showmin/ear_3d_model_survey/jp/05-acoustic-constraints.md

# Part 5 — 音響幾何制約

ステータス：受入済 ｜ 最終更新 2026-08-21

> 🌐 中文版：[cn/05-acoustic-constraints.md](../cn/05-acoustic-constraints.md)

---

## 5.0 手法の説明

ドライバがまだ選定されていないため、容積系の数値は現段階では絶対値を示せない。本節が示すのは**計算方法と比例関係**である。【仮定・要検証】と表示した箇所は、ドライバ仕様と各機種（S／M／L）のシェルエンベロープが確定した時点でそのまま代入でき、方法を設計し直す必要はない。

IEC 標準の正式条文への取得経路がないため、以下では公開情報で確認できる表題と適用範囲のみを用い、**条文の詳細を捏造しない**。

## 5.1 前気室容積 V_front、後気室容積 V_back

### 5.1.1 ⚠️ まず密閉するか否かを確定する——それが V_front の境界を決める

**同じ「前気室」でも、密閉型と非密閉型では定義がまったく異なる。取り違えれば集中定数モデル全体の境界が誤る。**

| 形態 | V_front の定義 | 証拠等級 | 備考 |
|---|---|---|---|
| **密閉型カナル**（イヤーチップが外耳道内で密閉を形成） | V_front ＝ ドライバ振動板からイヤーチップ内孔までの機器内部空間 ＋ イヤーチップから鼓膜までの残留外耳道容積。**耳甲介（concha）は密閉面の外側で大気に開放されており、V_front に算入しない** | 【慣例】電気音響アナロジーの集中定数モデル境界定義 | V_front を規定するのは**外耳道の幾何と挿入深さ**であり、耳甲介ではない |
| **非密閉型イヤホン**（本体が耳甲介腔に座り、外耳道内で密閉しない） | 明確な閉じた前気室は存在しない。本体と耳甲介腔・外界が漏れ結合を形成し、耳甲介容積は**結合気室＋漏れ経路**として模型に入る | 【慣例】同上 | この場合にのみ耳甲介の幾何が関係するが、**役割は結合気室であり密閉 V_front ではない** |

> ⚠️ **耳甲介の寸法は V_front ではない。**
> [Part 2.3](02-anthropometric-basis.md) の耳甲介幅（CW）と耳甲介深さ（CD）が規定するのは**シェルの外形エンベロープ**——本体をどれだけ大きくできるか——であり、音響的な前気室容積ではない。
> また CW／CD は**線形寸法**であり、容積へ換算するには形状仮定を追加で重ねる必要がある（耳甲介は不規則な椀状）。そうして得た数値は「文献の線形値＋形状仮定＋集団年齢の外挿」の複合推定であり、**【文献】と表示してはならない**。
> **本文書はこの外挿を行わない。**
> ⚠️ **耳甲介の「容積」を当チームは取得していない。** [Part 2.4](02-anthropometric-basis.md) が実測したのは耳甲介の**深さ**（CD、単一の長さ）であり容積ではない。P1–P5 の命名ランドマークを要する測定は、2D 注釈と 3D 点群を位置合わせできず中止した（Part 2.4.5 参照）。**したがって V_front には現時点で実測に基づく桁の参照値がない。** ドライバ選定後に機器内部の幾何から直接計算するか、別途、気室容積の測定を取得する必要がある。

### 5.1.2 容積換算と設計目標

| 項目 | 数値／しきい値 | 証拠等級 | 出典 | 備考 |
|---|---|---|---|---|
| 容積→音響コンプライアンス換算 | Ca = V/(ρ₀c²) | 【慣例】 | 線形音響の電気音響アナロジー標準理論 | 前後気室それぞれに代入 |
| 後気室の設計目標 | V_back とドライバ V_as の比を、密閉箱システム理論に従って整合させる | 【仮定・要検証】 | 学術論文：Thiele (1961)、Small (1972) の密閉箱システム理論 | ドライバ選定前は絶対値 cc を示せない。方法は確定済み |
| 桁のサニティチェック（**規範値ではない**） | 小型カナル型イヤホンの後気室容積は概ね 1–10 cm³ の桁 | 【仮定、参考のみ】 | 米国特許文献（請求範囲を逐一照合していない） | 業界標準ではなく桁の傍証にすぎない。**設計根拠としてはならない** |
| 機種 S／M／L の扱い | 各機種のシェル利用可能内部容積に応じて V_front/V_back を**比例配分**し、3 つの固定絶対値は与えない | 【仮定・要検証】 | — | Part 6 が各機種のシェルエンベロープ容積を提供した時点で代入する。機種が変わっても規則を書き直す必要はない。**注意：機種 ≠ 耳型区分。Part 0.4b 参照** |

## 5.2 チューニングポート（採用する場合）

| 項目 | 数値／しきい値 | 証拠等級 | 出典 | 備考 |
|---|---|---|---|---|
| 音響質量の式 | Ma = ρ₀(L+ΔL)/A | 【慣例】 | 線形音響の標準教科書（Helmholtz 共振器のネック理論） | — |
| 開口端補正（unflanged、開口周囲に平面なし） | ΔL ≈ 0.6133 × 半径 | 【文献】 | 学術論文：Levine & Schwinger (1948), *On the Radiation of Sound from an Unflanged Circular Pipe*, Physical Review | 開口が外耳道側へ開く場合に適用 |
| 開口端補正（flanged、開口周囲に平面あり） | ΔL ≈ 0.82 × 半径 | 【文献】 | Rayleigh の古典的近似。後続の数値研究で約 0.8216 と確認 | **文献には 8/(3π)≈0.849 という表記もある**（無限バッフル上のピストン放射の端補正の古典形）。どちらの数値も一般的であり、引用時に採用した方を明記すること |
| チューニングポートを設けない場合 | 前後気室を単一の音響コンプライアンスとみなすか、漏れ経路で代替する | — | — | ポートの要否は音響アーキテクチャ全体の判断であり必須ではない |

> ⛔ **以下はアーキテクチャ別に分ける。密閉式と開放式ではダクトの役割がまったく異なり、取り違えれば「式は正しく、アーキテクチャの適用先が誤り」となる。**

### 5.2.1 開放式（vented／ported）——判定可能

| 項目 | 数値／しきい値 | 証拠等級 | 備考 |
|---|---|---|---|
| 調律関係 | f₀ = (c/2π)·√(A/(V·L_eff))、L_eff = L + ΔL（ΔL は上表の端補正係数） | 【慣例】 | 標準線形音響（ヘルムホルツ共振器）。c=343 m/s |
| **設計手順** | 目標 f₀ と接続する気室容積 V を先に定め → A/L_eff を逆算する。**A と L の自由度は 1 つだけであり、両方を自由に与えてはならない** | 【慣例】 | 判定可能：f₀ と V が与えられていれば、誰でも設計者の A・L を代入して検算できる |
| 表示要求 | 設計値は f₀ と V を併記すること | 条文 | A・L のみで f₀・V がなければ、本条は検査できない |
| CAD 側の孔径補償 | 目標 d、収縮 u → CAD 上は d/(1−u) で作図。収縮 2%→2.041mm、4%→2.083mm（目標 2.0mm） | 【慣例】 | 収縮量は [Part 6.A](06-structure-materials.md#sec-6-a) 参照。**開放式のみ必要**（f₀ が設計目標であるため） |
| f₀ のずれの向き | 未補償の場合 f₀ は**系統的に 2–4% 低くなる**（d −2%→A −4.0%→f₀ −2.0%、d −4%→A −7.8%→f₀ −4.0%） | 【計算｜入力：定数】 | **一方向のずれであり偶然誤差ではない。** 数を多く造形して平均しても消えず、CAD 側での補償が必須 |

### 5.2.2 密閉式（sealed）——**上式は適用不可。一部は欠落として登録**

| 項目 | 内容 | 証拠等級 | 備考 |
|---|---|---|---|
| ダクトの役割 | 音導管は前気室の経路に直列に入る**音響質量** Ma = ρ₀·L_eff/A であり、**調律ネックではない。密閉式に設計者が選べる f₀ は存在しない** | 【慣例】 | 高域のロールオフと位相に効くのであって、共振の調律点ではない |
| 制約(a)：容積収支 | ダクト内容積は V_front に算入される（[5.1.1](#sec-5-1-1) 参照）。前気室の容積配分と食い合う | 【慣例】 | V_front の予算が決まれば判定できる |
| 制約(b)：高域上限 | ダクトの音響質量と**挿入後の残存外耳道容積**のコンプライアンスが高域共振／ロールオフを作る。数学的形式は 5.2.1 と同じだが、ここでの V は**利用者の残存外耳道容積であり設計者が制御できる気室ではない** → 「目標として逆算する」ものではなく「結果として検査する」もの | 【推論】 | 下記の欠落を参照 |
| **⛔ 欠落として登録** | **制約(b) に数値しきい値を与えられない。** 欠けているのは挿入後の残存外耳道容積：本案件のデータに外耳道内部は含まれず（[Part 2](02-anthropometric-basis.md) 参照）、挿入深さも未定の設計変数である。両方とも欠けているため、この検査は閉じない | 【欠落】 | いずれかが埋まれば判定可能になる：残存外耳道容積の実測値、または挿入深さを凍結した外耳道モデル |
| 制約(c)：漏れ経路としての側面 | 密閉が完全でない場合、ダクト自体が [5.3](#sec-5-3) の漏れ経路の 1 つとなる。その形状は 5.3 に従い測定状態を明記すること | 【推論】 | — |

### 5.2.3 両アーキテクチャ共通の下界

| 項目 | 数値／しきい値 | 証拠等級 | 備考 |
|---|---|---|---|
| 造形孔径の下限 | FDM 水平孔 ≥2.0mm、造形 Z 軸に沿う垂直孔 ≥1.0mm | 【慣例】 | 正本は [Part 6.A](06-structure-materials.md#sec-6-a)。⚠️ **最小フィーチャ寸法（0.5mm）とは異なる**（後者は薄壁／細柱用）。断面積の下限で約 16 倍の差 |
| 造形方向 | **調律孔／音導孔の軸は造形 Z 軸に平行とすること。** 平行にできない場合は内部サポートが完全に除去できることを検証し、**除去できないものは音響経路の失効とみなす**（精度劣化ではない） | 条文 | 逆方向の制約は [Part 6.A](06-structure-materials.md#sec-6-a)：機体の造形配置方向は自由変数ではない |
| 質量モデルの適用可能性 | せん断波数 **円孔 s = r·√(ρ₀ω/μ)／狭スリット s = (h/2)·√(ρ₀ω/μ)（h はスリット高。半分を代入）**。**対象帯域の最低周波数で確認すること。** s ≳10 なら質量モデルが綺麗、s ≲1 なら 5.3 の粘性狭路モデルへ、中間はどちらも綺麗でない | 【慣例】 | ⚠️ **これはモデル適用性の基準であって伝達量の基準ではない**——下記の定義境界を参照。**⚠️ 狭スリットは必ず半高を代入する（円管で半径を用いるのと同じ）。全高では s が 2 倍ずれ、s はしきい値と比較する量なので判定が逆側へ反転する** |
| s の実算値 | 2.0mm 孔：100Hz→6.5／500Hz→14.5／1kHz→20.5。1.0mm 孔：100Hz→3.2／500Hz→7.2／1kHz→10.2 | 【計算｜入力：定数】 | **最小造形孔は低域では綺麗な質量支配ではない。** 対象帯域に低域を含む場合、最小孔の質量モデルの結果自体に誤差がある |
| **孔数：単孔を既定とする** | **同一の音響機能の開口は単孔を既定とする。** 独立した 3 つの理由：①分割すると各孔の s が下がる ②各孔径がより早く造形下限を割る ③**総面積が等しくても音響的に等価ではない**（端補正 ΔL ∝ r。n 個に分けると r→r/√n となり L_eff が小さくなって f₀ が上がる） | 【推論】 | ダクトが短いほどずれは大きく、睡眠用イヤホンのダクトはもともと短い |
| 多孔の端補正（独立孔の極限） | n 個の孔にそれぞれ ΔL(r₁/√n) を適用した場合、f₀ のずれは n=2→+5.8%、n=4→+10.5% | 【計算｜入力：定数】 | ⚠️ **孔が音響的に独立とみなせる場合にのみ成立する。本案件の幾何（中心距離/半径≈4）はこの極限にはなく、この値は実際のずれではない** |
| **⛔ 欠落として登録** | **中心距離/半径 ≈ 2–10 の区間における多孔の有効端補正が未確定。** 開口率補正の系はずれがより大きい方向を示し、合体の極限はより小さい方向を示す。両者は矛盾し、しかも前者は本件の開口率では信頼できる範囲の縁にある | 【欠落】 | 必要なもの：この区間を扱う検証可能な文献、または BEM／FEM の数値解。**単孔を既定とするのは、この未解決区間を丸ごと回避するためである** |

> ⚠️ **正しい比は「中心距離/孔半径」であって「中心距離/波長」ではない。** 孔どうしが影響し合うのは付加質量の近傍場の重なりであり、その尺度は孔半径である。中心距離/λ で判定すると「可聴域に独立とみなせる孔配列は存在しない」という結論になり、バスレフポートや有孔板の実務と矛盾する。

### 5.2.4 ⚠️ s 基準の定義境界——今回の誤りの根本修正

| 項目 | 内容 | 証拠等級 | 備考 |
|---|---|---|---|
| s 基準の性質 | **せん断波数 s は「モデル適用性」の基準であって「伝達量」の基準ではない。** s≳10 は粘性を無視でき質量モデルが綺麗であることを、s≲1 は粘性抵抗が支配的で狭路モデルへ移るべきことを意味する | 【慣例】 | 標準的な粘熱音響 |
| ⛔ 禁止される推論 | **s から「音が通るか」や「最小開口寸法」を逆算してはならない。** s<10 は伝達しないことを意味せず、**粘性損失を伴って伝達する**ことを意味する。損失量は完全な粘熱音響インピーダンスから別途計算する | 条文 | **実例**：s≳10 から「520 Hz には 1.36mm の開口が必要」と逆算し、密閉式は成立しないと推論したことがある。**当該推論は撤回済み** |
| **⛔ スリット高の不均一性：補正係数を探してはならない。それは係数ではない** | 平均スリット高を固定しても、区間ごとのインピーダンス合計の倍率は**分布の集中度に依存し、上界がない**：N 区間・指数 n で上界 = N^(n−1)（n=3・N=4 → 16×／N→∞ で非有界）。**倍率は建模者が周方向を何区間に切るかにも依存する** | **【計算｜入力：定数】** | **「文献が来れば書ける」性質のものとは異なる——原理的に係数ではない。** 平均 50µm の 4 区間例：35/35/35/95→1.97×／20/20/20/140→5.54×／0/0/50/150→7.00×／0/0/0/200→16.0× |
| **⛔ さらに実分布は二峰性であり、平均まわりの揺らぎではない** | 軟質イヤーチップを外耳道へ押し込むとき、接触力学が与えるのは**接触域（h＝0。微小な h ではなく隙間が無い）と分離域**である。外耳道断面は円ではないため、密着は**複数の接触パッチ ＋ その間の開放円弧**となる | 【推論】 | **物理的に意味のあるパラメータは開放円弧の弧長と高さであり、全周の平均高さではない。** 二峰の場合（例：0/0/50/150）の倍率は 7×–16× であって 2× ではない。**Part 6 D 節の F_i パッチ単位条文と同一の物理像の別表現である** |
| 伝達量の正しい求め方 | 粘熱狭路の完全な音響インピーダンス（実部・虚部とも）を解き、損失対開口寸法の曲線を得てから逆算する | ⛔【欠落】 | 未計算。計算に先立ちインピーダンス式の形式を外部出典で検証する必要がある（**分野内部の計算であり、分野横断のクロスチェックでは検出できない**） |

[Part 0.4a](00-scope-and-usage.md#sec-0-4) 参照：判定基準は「モデル」を指すのか「物理量」を指すのかを明記すること。

## 5.3 漏れ経路の幾何規範

| 項目 | 数値／しきい値 | 証拠等級 | 出典 | 備考 |
|---|---|---|---|---|
| 判断基準：粘性境界層の厚さ | δ = √(2μ/ρω)、μ=1.8×10⁻⁵ Pa·s、ρ=1.2 kg/m³ | 【慣例】 | 標準的な流体力学／音響の式、公開されている物理定数 | — |
| δ の周波数依存 | 100Hz≈219µm／500Hz≈98µm／1kHz≈69µm／2kHz≈49µm／5kHz≈31µm／8kHz≈24µm | **【計算｜入力：定数】** | 上式による計算。誰でも再計算して検証できる | **当チームが独立に再計算し、6 つの数値すべてが一致** |
| 狭隙（隙間高さ ≲ 100µm） | Crandall の細管粘性音響インピーダンスモデルを用いる。**幅×高さ×長さの 3 寸法が必須** | 【文献】 | 学術論文：Crandall (1926) 細管粘性音響インピーダンス理論 | 粘性抵抗支配 |
| 円孔（孔径が境界層の桁より十分大きい） | 単純な開口の音響質量モデル（5.2 と同じ）を用いる | 【慣例】 | 5.2 に同じ | **半径×深さが必須**。質量支配 |
| **★ 必須規定** | 漏れ経路の納品仕様は**実際の幾何形状を含むこと。等価開口面積のみでは不可** | 条文 | チーム内インタフェース仕様 | 等価面積が同じでも幾何が異なれば → 物理機構が異なる → モデルを取り違える。**しかも誤りは静かに起き、エラーにならない** |
| **★ 測定状態の要件（5 つの次元）** | 漏れ経路の幾何には下記**5 つ**の状態次元を明記すること。単一の数値のみは不可 | 【推論】 | [Part 1A](01a-posture-analysis.md)、Part 6 C 節、Part 7 相互参照 | **2026-08-27 に 2 次元から 5 次元へ拡張**。従来は顎と熱の 2 次元のみ |
| ① 顎の状態 | 閉口／開口。開口を基準とするか 2 組を併記 | 【推論】 | Darkner et al. 2007／Oliveira et al. 1992 | 仰向け寝では下顎の弛緩で外耳道が変形し、閉口で測った隙間は**漏れを過小評価し遮音を過大評価する** |
| ② 熱の状態 | 装着直後／熱平衡後。代表状態は熱平衡後 | 【推論】 | Part 6 C 節の皮膚温硬度ギャップを参照 | **温度駆動の弾性率変化**——昇温でイヤーチップが軟化し密閉形状が変わる。**⚠️ ④ と独立ではない。下記参照** |
| **③ ⛔ 外部荷重（横向き寝の枕による圧迫）** | **無荷重／横臥時の受圧。受圧状態を基準とすること** | 【推論】 | [Part 1A](01a-posture-analysis.md) の横向き寝分析を参照 | **これが最も重大である。** 枕の圧迫がイヤーチップと外耳道を同時に変形させ密閉形状を変える。**無荷重で測った隙間は横向き寝の実値を系統的に過小評価し、しかも横向き寝は本件で凍結された主シーンである。** 無荷重形状から遮音を推すと静かに方向を誤る |
| **④ 持続受圧時間（粘弾性の応力緩和）** | 受圧の経過時間を明記すること | 【推論】 | 材料力学の一般知識 | **② とは異なる機構**：② は温度駆動の弾性率変化、本項は**時間駆動の定ひずみ応力緩和**——一定変位下で反力が時間とともに減衰し、密着圧が低下して**隙間が開きうる**。一晩 6〜9 時間はまさにこの機構が働く区間である |
| **⑤ 挿入深さ／装着の締まり具合** | **単一の代表値は不可。分布で与えること** | 【推論】 | Part 7 参照 | 利用者は装着のたびに異なる。密閉位置と**挿入後の残存外耳道容積**を同時に決め、後者は V_front の構成要素である（5.1 参照） |

> **⚠️ ② と ④ は異なる機構だが独立ではない——代表状態を別々に書いてはならない。**
> **エラストマーの応力緩和速度そのものが温度上昇とともに速くなる**ため、「熱平衡後」と「30 分後」は個別に回せる 2 つのつまみではない：**皮膚温での 30 分は、室温での 30 分より緩和量が大きい。**
> **⇒ 代表状態は「熱平衡後、かつ熱平衡到達時点から起算して持続受圧 ≥30 分」と書くこと**——**時間の起点を熱状態に縛る。装着時からではない。**
> **幅は未評価。数値は捏造しない**。方向は確定（同じ時間なら皮膚温のほうが緩和が大きい）。処置は Part 6 C 節の硬度温度ギャップと同類：方向確定・幅未知でも登録する。【推論】

> **⚠️ 試作機の測定：統合とは同時測定ではない。順序を固定し記録すること。**
> **F_i／A_i は接触界面に圧力センサフィルムを置くが、フィルム自体に厚みがあり締め代と密着を変える**。一方、漏れ形状は接触界面が原状であることを要する。**フィルムを挟んだ状態で測った漏れ形状は、フィルムなしの漏れ形状ではない**——これは「異なる状態の数値どうしを除算する」のと同類であり、ただし干渉源が測定器具そのものである。
> **⇒ 正しい形は「同一の装着で、順に測り、順序を固定する」。** どちらを先に測るかは、前の測定が残す擾乱（圧縮後のエラストマーの短期回復など）に対してどちらが鈍感かによる。**この点は実際に試すまで決められないため、現時点では前提を置かない。**
> **ただし形式層は今すぐ決められる：測定計画に順序と間隔時間を明記すること。** さもなければ 2 組のデータの比較可能性を事後に再構成できない。

> **適用範囲**：測定状態の要件が**主に影響するのは密閉型カナル**（硬い密閉面があり、変形が密閉の完全性へ直接影響する）。非密閉型イヤホンの耳甲介結合気室（5.1.1 参照）も顎の動きで変化するが、硬い密閉面がなく影響の性質が異なり重要度も低いため、本節では展開しない。
>
> **数量は示さない**：現時点で得られているのは「被験者 30 名全員に有意な変形」と「n=1 の症例で前後方向に約 25%」のみであり、**漏れ隙間の変化量に関するデータは一切ない**。したがって方向と要件のみを示し、量をまたぐ外挿は行わない。

### 5.3.1 測定状態の 2 つの次元

| 項目 | 内容 | 証拠等級 | 備考 |
|---|---|---|---|
| 測定状態（2 次元） | **顎の状態**（閉合／開口）×**熱状態**（装着直後／熱平衡後）を明記すること | 【推論】 | 成因が異なる：顎は外耳道の幾何を変え、熱状態はイヤーチップの硬度を変える（[Part 6.C](06-structure-materials.md#sec-6-c) 参照） |
| 代表状態（一晩） | **開口 × 熱平衡後**、または 4 組すべてを提示 | 【推論】 | 6〜9 時間の大部分がこの状態にある |
| 反例の警告 | 装着直後＋口閉合で測った隙間は**漏れを過小評価し、遮音を過大評価する**。実験室では最もこの状態で測りやすい | 【推論】 | **2 つのずれは同方向に重なり、打ち消し合わない** |

熱の次元は硬度の温度係数の数値がなくても成立する——幅が分からなくても「状態を明記せよ」は変わらない。幅は [Part 6.C](06-structure-materials.md#sec-6-c) の欠落を待つ。

### 5.3.2 ⚠️ 変異源は 3 種類あり、状態の明記で防げるのは 2 種類のみ

| 項目 | 内容 | 証拠等級 | 備考 |
|---|---|---|---|
| 変異源の分類 | 顎の状態と熱状態は**同一個体の異なる時刻**の変異であり、同一個体の反復測定で覆える。**公差の積み上げは個体間**の変異であり、同一個体を何度測っても覆えない | 【推論】 | [Part 6.A](06-structure-materials.md#sec-6-a) の製造帯域と相互参照 |
| 条件付きの要求 | 安全経路の最小開口が <0.5mm（Part 6 が造形孔フィーチャではなく**組立隙間**と判定する帯域）の場合、**本節の状態明記では不足し、別途サンプル数の規範が必要** | 【推論】 | 条件の成否は開口寸法の算出待ち |
| ⚠️ 検証レベルへの帰結 | その場合、安全機能は**型式試験では覆えず**、全数検査が必要となる。しかも検査項目は**基本周波数の音響伝達量であって寸法ではない** | 【推論】 | 全数の音響測定と全数の寸法測定では産線コストの桁が異なる |

## 5.4 パッシブ遮音 vs 気室容積のトレードオフ

> ⛔ **方向は 2026-08-25 に確定した：快適を優先し、遮音が譲る。** 大目標が装着感に限定されたため（[GOAL](../GOAL.ja.md) 参照）、このトレードオフはもはや中立記述ではない。**ただし譲歩には下限がある。**

| 項目 | 数値／しきい値 | 証拠等級 | 出典 | 備考 |
|---|---|---|---|---|
| 完全密閉は中高域の遮音を高めるが、オクルージョン効果（occlusion effect）を生じ、現象は低域に集中する | 現象として成立 | 【慣例】 | 聴覚学／電気音響工学の一般知識。**特定の論文は未検証** | 利用者自身の発話音がこもって／うなるように知覚される。**具体的な周波数範囲の数値は示さない**——出典を確認できておらず、かつその数値は設計上の行動を変えない |
| 対策：漏れ経路を設けて圧力を逃がす | 条文 | 【慣例】 | 同上 | 遮音と低域応答の一部を犠牲にする。5.3 の漏れモデルと併せて折衷点を決める |
| 具体的なパッシブ遮音の dB 目標値 | **要確認** | 【仮定、根拠なし】 | — | 検証可能な一次測定データがない。未検証のネット上の数値は採用せず、実測を待って補う |

### 5.4.1 遮音の下限——3 条件のうち最も厳しいものを取る

| 条件 | 内容 | 状態 |
|---|---|---|
| **(a) 内容が聞こえること** | **安全な曝露レベルを超えない範囲で**、L_内容(耳内) − L_環境(遮音後) ≥ SNR_min | ⛔ 数値の欠落 |
| **(b) 同床者を起こさないこと** | L_漏れ音(同床者位置) ≤ 覚醒しきい値 | ⛔ 数値の欠落 |
| **(c) 安全上重要な音で目覚められること** | 火災警報器・目覚まし等が睡眠状態でも覚醒を引き起こすに足ること | ⚠️ **安全制約の候補。製品層の裁定待ち**。数値の欠落 |

**(a) に音量上限を縛り込む理由**：縛らなければ (a) はいつでも音量を上げれば満たせてしまい、下限として機能しない。密閉↓→遮音↓→利用者が音量を上げる→曝露↑ となり、**圧力は本ガイドラインが唯一範囲外としている次元へ移動する**（[5.7](#sec-5-7) 参照）。しかも一晩 6〜9 時間は累積被害に最も有利な条件である。

**(c) の位階**：安全は**制約**であって目標ではない。成功指標には入れず「侵してはならない」側に置く。[GOAL 5.1](../GOAL.ja.md#sec-5-1) 参照。

**(c) が 3 条件中で最も厳しい可能性**：要求されるのは睡眠状態の**覚醒しきい値**であり、覚醒時の可聴しきい値より高い。

### 5.4.2 (c) のスペクトル的性質と検収方法

| 項目 | 数値／しきい値 | 証拠等級 | 備考 |
|---|---|---|---|
| 安全警報の基本周波数 | **520 Hz ±10% 方形波【文献｜出典 NFPA 72（米国）；目標市場の該当規格は未確認】** | 【文献】 | 根拠は低周波の覚醒効力に関する研究。**目標市場が従来型の高周波警報（3100 Hz 帯）を採用する場合、本節の結論は再評価を要する** |
| ⚠️ 方形波のスペクトル的帰結 | 方形波は奇数次高調波を含む（520／1560／2600／3640 Hz、源振幅 1/n）。粘性支配経路では s が周波数とともに上がる ⇒ **高域通過的性質：基本波の減衰が最も大きく、高調波はより通りやすい** | 【計算｜入力：定数】 | 実算 200µm 隙間：s=1.48／2.56／3.30／3.90。500µm：3.69／6.39／8.25／9.76。20°C 基準、再計算可 |
| ⚠️ 失効の性質 | **経路は警報を減衰させるだけでなく、規格が意図的に避けている高周波の形態へ変換してしまう。** 利用者は「聞こえている」（高調波が通る）が、その音はすでに覚醒させる性質を失っている——しかも対象顧客層は高齢寄りであり、まさに高周波警報で寝過ごしやすい層である | 【推論】 | — |
| **(c) の検収方法** | **基本周波数単独で伝達量を測定すること。広帯域や総エネルギーで代替してはならない** | 条文 | 広帯域測定は高調波に押し上げられ、基本波の損失をちょうど覆い隠す。覚醒効力は基本波にある |
| ⚠️ 軽度の失効ほど発見しにくい | 完全閉塞なら少なくとも遮蔽効果（occlusion effect）で気づける。**通っているが減衰が大きすぎる状態には、知覚できる兆候が一切ない** | 【推論】 | ゆえに**「経路が通っていること」を検収根拠にしてはならない** |
| **⛔ 最小開口寸法** | **未確定。** s 基準から逆算してはならない（[5.2.4](#sec-5-2-4) 参照） | 【欠落】 | 粘熱インピーダンスの計算待ち。**それまでは、これを根拠にいかなるアーキテクチャも否決してはならない** |

### ⛔ 5.4 の欠落登録

寝室の環境騒音レベル分布（WHO 夜間騒音ガイドラインは全文未取得。印象で引用しない）／SNR_min（内容の種別に依存し、**製品の音声戦略が未定義**）／同床者および睡眠状態の覚醒しきい値（未検証）／機器→同床者への漏れ音の伝達（実測が必要。当チームに FEM／BEM も測定能力もない）／**安全音の帯域に対応する目標市場の規格**（未確認）。
**いずれか 1 つが埋まっても本節は閉じない。** (a)(b)(c) はそれぞれ異なる組み合わせを要する。

> **⏳ 候補解を先に登録し、早すぎる排除を防ぐ**：安全経路の要求が [Part 6.A-3](06-structure-materials.md#sec-6-a) の第 1 帯（<0.5mm）に落ちても、**その帯が脱落するとは限らない**。音響ダンピングメッシュ（acoustic mesh）は**音響抵抗**を規格として販売されており、「音響的性質」と「造形可能な幾何」を分離できる——筐体には造形も検査もしやすい大きな孔を開け、音響抵抗はメッシュが担う。個体間変異は公差の積み上げからサプライヤ規格へ移る。
> ⚠️ **3 つの限界を同時に登録する**：①**サプライヤ規格は未検証**（当チームは規格書を一切入手していない。「一般的なメッシュはおおよそこの程度」で代入してはならない）②メッシュは**抵抗性**要素であり、加わるのは減衰である——**その価値は減衰の低減ではなく分離にある** ③メッシュは耳垢で目詰まりする（業界ではまさに wax guard として用いられる）。**閉塞を設計問題から保守問題へ移すのであって、消去するのではない**。交換部品の失効は利用者が実行するかに依存し、製品層の判断に属する。
> ④ 音響抵抗は**サプライヤ規格 ＋ 固定工程**の双方で決まり、単一の出荷値ではない。接着剤は繊維に沿って毛細浸透し、音響抵抗を**一方向に上昇させる（＝減衰増、危険側）**——処置は [Part 0.4c](00-scope-and-usage.md#sec-0-4c) の第 1 類型：**構造的除去が補償に優先する**。

### 前提への依存

下限の厳しさは**製品が一晩中マスキング音を流すか**に依存する。流すならマスキング自体が遮音の仕事をし、受動遮音の要求は下がる。静かな受動防護として位置づけるなら遮音が製品の本体になる。**この前提が定義されるまで数値は示さない。**

> ⚠️ **上記のトレードオフは「幾何が静的である」という仮定を含んでおり、その仮定は密閉型カナルの仰向け寝では成立しない。**
> 下顎の弛緩による外耳道の変形（[Part 1A](01a-posture-analysis.md) 参照）により実際の密閉状態は静的測定値から乖離し、**静的幾何から導いた遮音性能は楽観側に偏る**。
> 現時点で漏れ隙間の変化量のデータがないため、数量は示さず方向性の注意喚起にとどめる。【推論、Part 1A に基づく】

## 5.5 シミュレーションが信頼できる周波数境界

| 項目 | 数値／しきい値 | 証拠等級 | 備考 |
|---|---|---|---|
| 判断基準 | kL = 2πL/λ ≪ 1、L = 最大の気室／導管の代表寸法、c = 343 m/s | 【慣例】自ら導出 | — |
| 数値が信頼できる境界 | f_reliable = c/(8L)（L = λ/8） | 【慣例】自ら導出 | 誤差の桁は許容範囲 |
| 完全に破綻する境界 | f_breakdown = c/(4L)（L = λ/4、最初の 1/4 波長定在波モード） | 【慣例】自ら導出 | 両者の間はグレーゾーンであり、傾向の参考にしかならない |

| L (mm) | f_reliable | f_breakdown |
|---|---|---|
| 8 | ~5.4 kHz | ~10.7 kHz |
| 10 | ~4.3 kHz | ~8.6 kHz |
| 12 | ~3.6 kHz | ~7.1 kHz |
| 20 | ~2.1 kHz | ~4.3 kHz |
| 25 | ~1.7 kHz | ~3.4 kHz |
| 30 | ~1.4 kHz | ~2.9 kHz |

（当チームが全表を独立に再計算し、数値は一致。）

**保守性に関する注記（削除してはならない）**：f_breakdown = c/(4L) は一端開放・一端閉管に対応する。両端が閉じた気室の第 1 縦モードは λ/2（f = c/(2L)）であり、本表より遅く現れる。**本表は保守側であり、実際の破綻は表の値より遅く生じうる。** 外部へ引用する際は、これが保守的推定であり正確な物理境界ではない旨を明記すること。

**形態による影響**：カナル型（L≈8–12mm）はシミュレーションが ~3.5–5.4kHz まで信頼できる。オーバーイヤー型（L≈20–30mm）では ~1.4–2.1kHz まで低下する。大きな気室の形態を採る場合、中高域は実測に頼るほかなくシミュレーションに依存できない。

## 5.6 標準の引用範囲に関する宣言

IEC 60318-4:2010《Electroacoustics – Simulators of human head and ear – Part 4: Occluded-ear simulator for the measurement of earphones coupled to the ear by means of ear inserts》。公開情報により適用範囲 100Hz–10kHz、イヤーインサート型イヤホンの測定であることを確認。

**表題と範囲のみを確認しており、条文の詳細は確認していない。最新版かどうかも照合していない。条番号を捏造しない。**

### 5.6.1 本章の【計算】値の基準と温度感度

> 本章のすべての【計算】値は **20°C、101.325 kPa の乾燥空気**を基準とする（ρ₀=1.204 kg/m³、μ=1.813×10⁻⁵ Pa·s、c=343.2 m/s）。
>
> **実際の気室温度は室温と体温の間にあり**、装着時間とともに変化する。37°C 側では **c と f₀ が約 3% 高く、s が約 5% 低く、δ が約 5% 高い**（ρ は理想気体、μ は Sutherland、c は 331.3√(1+T/273.15) による）。より高い精度が必要な場合は実際の気室温度で再計算すること。
>
> **すべてを 37°C で計算し直さない理由**：気室の実温度は不明であり時間とともに変化する。「37°C 版」を出すことは、別の未申告の仮定に置き換えるだけである。**基準を開示して感度を示すほうが誠実である。**
>
> 湿度の影響は温度より小さく、評価していない。

## 5.7 本節が扱わないもの：音量安全境界

音量安全境界は電気出力／DSP リミッタの範疇であり幾何制約ではない。また WHO／NIOSH 等の騒音暴露に関する正式標準の裏付けを要するが、当チームには検証済みの取得経路がない。

**明示的に数値を置かない。** 後続段階または別章での扱いとする。これは意図的な除外であり、見落としではない。
