showmin/ear_3d_model_survey/jp/09-checklist.md

# Part 9 — チェックリスト

ステータス：初稿 ｜ 最終更新 2026-08-21

> 🌐 中文版：[cn/09-checklist.md](../cn/09-checklist.md)

## このリストは誰のためのものか

**利用者＝このガイドラインを使って設計する人。** 3D モデルを作成した後、本リストと項目ごとに照合して自己点検する。

**これは要求元に記入して返してもらうアンケートではない。** リストは成果物の一部であり、成果物を書くための前提条件ではない。

リストには性質の異なる 2 種類の項目がある。分けて読むこと：

| 区分 | 性質 | 誰がいつ扱うか |
|---|---|---|
| **A. シーン前提** | **プロジェクト範囲の決定** | **要求元が着手前に確定する**。以降は変更しない。3–4 問のみ |
| **B–H** | **モデル点検項目** | **設計者がモデル完成後に**自分のモデルを項目ごとに照合する |

表示の説明：
- 「⛔」＝**却下項目**：不適合なら製品として成立しない。減点ではない
- 「⏳」＝**現時点で数値しきい値がない**。本ガイドラインは方法のみを示し、実測で補う必要がある
- 「**⚑**」＝**ゲート項目**｜「**◆**」＝**形式制約**：下記参照

**すべての項目は判定可能である**——はい／いいえで答えられる。答えられなければその項目の情報が不足しているということであり、それ自体が結論である。

### 0. これらの規範自体の索引——「いつ使うか」で並べる。長い一覧にしない

**規範層は 1 日で 5 条まで増えた。どれにも実際の由来がある。しかし規則が一定数を超えると、遵守はいつのまにか選択的遵守に変わり、どれを選んだかは外から見えない。** それは規範層に、我々がずっと防いできたのと同じ現象を起こす：**規則は揃って見えるのに誰も全部は使っていない。しかも文書上の証拠が揃っているぶん、規則がない場合より気づきにくい。**

**対処は規則を削ることではなく、各条をその発動タイミングに結びつけることである。** ある作業のときだけ効く規則は、別の作業のときに頭の容量を取らない。

| いま何をしているか | 適用される条 | その条が防いだ実際の誤り |
|---|---|---|
| **新しい項目を書く** | 「無作為時の既定値は失敗側に」 | 5.2-6「ヘルムホルツを使っていない」——何もしなくても通過し、条項として機能しない |
| **項目に印を付ける** | ⚑ ゲートの見分け方／◆ 形式制約（⚑ と併存可） | 6C-2-1 を二者択一にすると「Shore A と 00 は相互比較不可」の半分が失われる |
| **ゲート判定のあと** | 3 つの表示状態（判定不能／非該当／入力待ち） | 開口 <0.5mm のとき孔径項目を「判定不能」と書くと、永久に閉じられない偽の穴が残る |
| **他章の項目を参照する** | 否定形には肯定形を対に＋前提を明記 | 「配置方向が孔軸に抵触していない」だけでは、孔軸が未指定の設計が静かに通過する |
| **ある出典の結論を別分野へ持ち込む** | **持ち込み先の分野の担当者に一言貼ってから使う**（下記参照） | 3 件の持ち込み誤りはすべて**持ち込み先**が検出。持ち込んだ側は一度も自分で気づかなかった |
| **しきい値が手に入らないとき** | 先に形式を固める（◆）。空欄にも保留にもしない——**ただし形式そのものが固定可能かを先に確認する。判定基準は下記** | P9-A：未定なのはしきい値だけでなく、どの帯域を見るかも未定 |

> **⚠️「先に形式を固める」は常にできるとは限らない。判定基準は、形式の候補を列挙できるかである。**
>
> | 状況 | 候補を列挙できるか | 処置 |
> |---|---|---|
> | 帯域が未定（P9-A） | **できる**——オクターブ／1/3 オクターブ帯は有限集合 | **形式を固める**：帯域で記し、しきい値が来たら埋める |
> | 回路トポロジーが未定（メッシュ前容積の無関係性基準） | **現時点ではできないが、本質的にできないのではない**（2026-08-27 訂正） | **止めて欠落として登録し、何を待っているのかを明記する** |
>
> 後者の実例：当該基準は 3 版とも誤っていた（無次元比 → 純体積比 → ωR·C ≪ 1）。第 4 版は提出が拒否された。**そのとき挙げた理由は「分野内部の誤りでクロスチェックが効かない」——それは検証が要る理由であって、形式を先に固められない理由ではない。** 完全な理由は候補が列挙できないことである。
> **この行がなければ「先に形式を固める」は形容詞規則になる**——常に可能に聞こえ、いつ不可能かが分からない。
>
> **⚠️ ただし「列挙できない」はさらに 2 種に分けること。さもないと一時的なものを恒久的なものとして書いてしまう**（2026-08-27 訂正）：
>
> | | 意味 | 処置 |
> |---|---|---|
> | **本質的に列挙不能** | 候補集合そのものが非有界 | 本当に書ける形式がない |
> | **まだ列挙できる時点に達していない** | **列挙できないのは上流の設計が未選択だからであり、設計が決まれば一意になる** | **待っているのは文献ではなく決定である。誰のどの決定を待っているかを明記する** |
>
> **実例**：メッシュ前容積の判定基準のトポロジーは固定方式に依存する（座ぐり容積の有無／押さえリングの絞りの有無／接着溝が幾何を変えるか）。3 通りの作り方が 3 つの異なる回路を与える。**先に「トポロジーの候補は列挙できない」と書いたのは半分しか当たっていない**——非有界なのではなく**設計が未定**なのである。固定方式は安全経路の形態条文に属し現在は停止対象なので、真の順序は：**設計の決定 → トポロジーが一意に定まる → そこで初めて当該トポロジーの式を文献に求める。**

> ⛔ **規範を追加する条件：それが防いだ実際の誤りを名指しできないなら、追加しない。**
> この条は規則を**増やす**のではなく**減らす**ために置く——「もっともらしい」だけでは規範にならない。
> 上表の最終列は簡素化のときの判断材料でもある：**後から規則が多すぎると感じた人が手を付ける際、各条が何を防いだかが見えていなければならない。見えなければ直感で削ることになり、直感は最も直感に反する条から削る**——充足性ゲートと否定形の対付けはまさにその種であり、そしてまさに実際に踏んだものである。

### ⚠️ 結論を持ち込むとき、誤りが見えるのは持ち込み先であって出典側ではない

2026-08-27 の文献統合で同型の誤りが 3 件続いた。**いずれもある出典の結論を別の文脈へ持ち込んだものである**：

| 持ち込み | 誰が検出したか |
|---|---|
| 深さに年齢傾向なし → 容積に年齢傾向なし（**次元**をまたぐ） | 音響の容積計算へ持ち込み → **音響側**が検出 |
| 彼らの CD の免除 → 我々の CD の免除（**定義**をまたぐ） | 我々の測定定義へ持ち込み → **測定側**が検出 |
| 左右相関係数 → 解剖学的対称性の証拠（**測定の性質**をまたぐ） | 測定信頼性の領域へ持ち込み → **測定側**が検出 |

**3 件とも持ち込んだ本人は気づいていない。これは不注意ではなく構造的である：**

> **出典の文脈では、その文は正しい。** 持ち込んだ側が見直しても、見えるのは依然として正しい文である。
> **持ち込み先の前提を知っているのは持ち込み先だけ**なので、そこで成立しないことを見抜けるのも持ち込み先だけである。

**⇒ この種に自己点検は効かない。** 対処は[公告規則](#sec-9-rules)の発動タイミングを「指示を受けたとき」から「結論を持ち込むとき」へ広げることである：**X 分野の結論を Y 分野で使う前に、「X のこの結論を Y で使う」と一言 Y の担当者へ貼る。** 返信を待つ必要はなく、貼れば足りる——**これは新しい規則ではなく、既存の公告規則の発動タイミングの拡張である。**

**持ち込む前に自問する 3 点**（上表の 3 類型から）：**次元は同じか。定義は同じか。この数値は自分が思っているものを測っているか。**

### ⚠️ 発動タイミングのある誤り vs ない誤り——後者は定期的な全表点検でしか取れない

**どちらも他者の目を要するが、予見可能性が異なる：**

| | 機構 | 「いま自分はそれをしている」瞬間があるか | 処置 |
|---|---|---|---|
| **持ち込みの誤り**（分野をまたいで結論を使う） | **視点**——持ち込み先の前提を知るのは持ち込み先だけ | **ある**。持ち込む前に自分で分かる | **発動タイミングに紐づける**：持ち込む前に一言貼る |
| **⛔ 切り分けの誤り**（表そのものの切り方が違う） | **惰性**——自分が作った表は、見直すとき当初の切り方に沿って読んでしまい、**切り方自体の誤りが見えない** | **ない**。表は静的で、誤りはずっとそこにある | **⇒ 定期的に表全体を通す。この種には紐づけられる事象がない** |

**実例（同日、方向が逆の 2 件）**：
- **前段の層を落とす** → 実際より単純に見える（F_i を「試作機待ち」と登録したが、第一層の測定状態は今すぐ決めるべきだった）
- **2 つの量を統合する** → 実際より阻害されて見える（耳甲介容積と筐体利用可能総容積を合報し、**アーキテクチャに依存しないツールの問題**まで (c) に阻まれているように見せた）

> **どちらも自分で気づいたものではなく、相手の反例を見て初めて戻って調べたものである。** だから**「報告された数件を直す」では足りず、表全体を一度通す必要がある**——切り分けの誤りはひとりでに浮かび上がらない。

### ⚑ ゲート項目——通過していない場合、その配下は「判定不能」とする

一部の項目は**他の項目を判定するための前提**である。例：「構成を密閉型かベント型か宣言済みか」。宣言せずに先へ進むと、**誤ったほうの組にチェックを付け、しかもすべて通過してしまう。**

> ⛔ **チェックリストで最も危険な失効は「通らないこと」ではなく、「誤った組に付けて全部通ること」である。**

**規則**：ゲート項目が通過していない場合、その配下の項目はすべて**「判定不能」**と記す。
**空欄にしてはならない**（「まだやっていない」と読まれる）。**チェックを付けてもならない**（偽の通過である）。

### 項目の「無作為時の既定値」は失敗側になければならない

判定基準は**項目が肯定形か否定形か**ではなく、**設計者が何もしなかったときにその項目が通るか通らないか**である。

> ⛔ **既定値が通過側にある項目は、無いのと同じである。**

| 項目 | 何もしないと | 判定 |
|---|---|---|
| 「ヘルムホルツ f₀ の逆算でダクト寸法を決めていない」（密閉型） | 実際に使っていない → **通過** | ⛔ 素通り。「ダクト寸法の決定根拠を記載済みか」を対にする |
| 「f₀ の収縮補償を適用していない」（密閉型） | 実際に適用していない → **通過** | ⛔ 素通り。「補償していない」≠「正しく処理した」。「収縮量の V_front への影響を算入済みか」を対にする |
| 「硬度のギャップを保守的推定として扱っていない」 | そもそもギャップに言及していない → **通過** | ⛔ 素通り。「ギャップを記載済みか」を前提にする |
| 「機体の造形配置方向が音響孔軸に抵触していない」 | 孔軸が一度も指定されていない → **通過** | ⛔ 素通り。「孔軸を Z 軸と平行に指定済みか」を前提にする |
| 「接触領域に R < X の稜線が存在しない」 | CAD の既定エッジは鋭角 R≈0 < X → **失敗** | ✅ 成立。無作為が安全側に落ちる |

**最後の行は対照例である**：同じく否定形だが既定状態が失敗であるため、対にする必要がない。**チェックリストを書くときは各項目について「何もしなければどうなるか」を問い、「否定文かどうか」を問わない。**

### ⚑ ゲート項目の見分け方

**「測る基準を定義しないと、どのしきい値を使うのか／何を個別に確認するのかが決まらない」項目がゲートである。**

本ガイドラインの 6 つのゲートはすべてこの形をとる——5.2-1 は構成を、5.3-1 は形状を、5.5-1 は特徴寸法を、6A-3-1 は寸法帯を、6C-2-1 は硬度スケールを、6D-2-1 はパッチ集合を定義する。**まず測る基準を定義し、それからしきい値を語る。**

### ◆ 形式制約——⚑ ゲートと直交する。同時に成立しうる

**両者は異なる問いに答えるものであり、同一分類の 2 つの値ではない：**

| 表示 | 何に答えるか | 何についてか |
|---|---|---|
| **⚑ ゲート** | これが通らないと**後続を判定できるか** | **依存と順序** |
| **◆ 形式制約** | 値を入れたあと、**しきい値と比較できるか** | **比較可能性** |

**1 つの項目が両方でありうる。** 例：
- **6C-2-1**（ショア硬度のスケール）：ゲートであり（未記載なら後続の硬度項目でどちらの組を使うか決まらない）、形式制約でもある（**Shore A と Shore 00 の数値は相互比較できない**）
- **5.3-1**（漏れ経路を実形状で明記）：充足性のゲートであり（等価面積のみでは後続の状態注記が無効）、形式制約でもある（スリットは幅×高さ×長さ、円孔は半径×深さ。**形式が違えば比較できない**）

> ⛔ **どちらか一方を選ばせてはならない。** 両方の性質が実在し、選ばせれば一方が失われる。項目は ⚑ と ◆ を同時に持ってよい。

**★ 形式制約の実務的価値：しきい値を知らなくても書けて、しきい値が確定しても書き直しにならない。** しきい値が未定のとき、形式を先に固めることは唯一無駄にならない作業である。

### 3 つの表示状態。混用してはならない

ゲートは 2 種類の異なる出力を生む。混同すると偽の穴を作るか、本物の穴を消してしまう：

| 表示 | 意味 | 閉じられるか |
|---|---|---|
| **判定不能** | 前提が欠けている（ゲート未実施）。**ゲートを済ませれば解消する** | 一時的 |
| **非該当** | ゲートの答えによって除外された。**どのゲートのどの答えで除外されたか明記すること** | 恒久的 |
| **入力待ち** | 判定可能だが入力が未到着（例：PDT の数値待ち） | 入力待ち |

**例**：6A-3-1 が開口 <0.5mm と判定 → その設計に造形孔は存在しない → 孔径の項目は**非該当**であって判定不能ではない。
誤表示の代償：「非該当」を「判定不能」と書けば**永久に閉じられない偽の穴**ができる。本物の穴を「非該当」と書けばそれが消える。

> **前提関係は項目に明記し、章の並び順に依存しない。** 後で章を並べ替えたとき、並び順の慣習は壊れるが、明記された前提は壊れない。

---

## A. シーン前提（Part 1）

> **本節は要求元が着手前に決定する。** 設計者の点検項目ではない。以下の数問のみであり、B–H 節がモデル点検にあたる。

### A-0 まずこの問いに答える——以下のどの節が該当するかを決める

- [ ] ⛔ **どのシーンを対象とするか？ A 一晩中の臥位睡眠／B 座位睡眠／両方。**
  B はさらに分かれる：**B1 オフィス仮眠**／**B2 短距離通勤**（降車駅を見る必要あり）／**B3 長距離交通**。
  **両方を対象とする場合、両制約の和集合を満たす必要があり、横向き寝が依然として拘束条件となる。**

### A-1 全域項目——シーンを問わず一律に適用

- [ ] 「**利用者は睡眠中に無意識であり**、自分で調整も不快への反応もできない」という前提を受け入れるか？
- [ ] ⛔ **装着試験に高齢被験者を含めているか？** 現有の寸法データは年齢が低いか不明であり、耳の寸法は生涯にわたり増大する。**この欠落は試験でしか埋められず、数値では埋められない**（Part 2.0.2 参照）
- [ ] 寸法設計は上限側に余裕を持たせ、高齢利用者をカバーしているか？
- [ ] 耳珠（tragus）を主たる保持支点にすることを避けているか？ 同部位は**最も圧迫に敏感な領域であり（Part 3）、かつ顎の動きで変形する（Part 1A）**
- [ ] ⛔ **耳型採取または装着検証は「開口」状態を含んでいるか？** 下顎の弛緩が外耳道を変形させる（被験者 30 名全員で発生）。閉口のみでは必要なフィット許容幅を系統的に過小評価する。
  **仰向け寝と座位睡眠の双方で生じる**——仰臥では下顎が落ち、座位では頭部前傾時に口がわずかに開く（[Part 1A.2、1A.4](01a-posture-analysis.md) 参照）

### A-2 シーン A（一晩中の臥位睡眠）専用

- [ ] 製品は**一晩中連続装着**か、それとも入眠後に外すか？ 後者なら圧力と耐久の要求を大幅に緩和できる
- [ ] **右側臥位**を重点的に検証したか？（高齢利用者は右側臥位を明確に好み、右耳の累積圧迫が高い）

### A-3 シーン B（座位睡眠）専用 — ⛔ **非該当（第一段階の範囲外）**

> **本組はすべて「非該当」とする。除外の根拠：発注者が 2026-08-25 に第一段階を夜間の長時間睡眠のみと裁定。**
> **チェックを付けてはならず、「判定不能」と記してもならない**——これは範囲の決定による恒久的な除外であって、前提の欠如ではない（上記の 3 状態の説明を参照）。
> 項目は将来シーンを拡張する際に使えるよう残す。

- [ ] ⛔ **居眠り時に頭部が前傾・側方へ倒れても、保持され脱落しないか？**（保持はシーン B の支配的制約であり、横向き寝の突出高さに代わる位置を占める）
- [ ] U 字型ネックピローが耳後部と頭部側面に接触する影響を考慮したか？（イヤーフック型で特に関係する）
- [ ] 遮音は静かな寝室ではなく交通騒音（低周波が主体）を対象に設計したか？（**B2／B3**）
- [ ] 着脱と収納は容易か？（使用が頻繁であり 1 日 1 回ではない）
- [ ] ⛔ **状況安全に必要な環境音の把握を確保しているか？**（**B2 が最も重要**——降車駅を見る必要があり乗り過ごしてはならない。完全な密閉遮断はこのシーンでは利点ではなく欠点）
- [ ] 公共の場での外観は受容可能か？（**B1 が最も厳しい**——同僚がいる。B3 が最も緩い）
- [ ] 日中の環境光に対処しているか？（**座位睡眠に固有**——夜間の問題は「光をなくす」ことだが、日中は逆に「光が多すぎる」。Part 1A.4.1 参照）

## B. 敏感領域と配置禁止領域（Part 3）

- [ ] ⛔ **荷重を受ける保持構造は耳珠（tragus）を避けているか？**（耳甲介 6 点のうち実測で最も敏感）
- [ ] ⛔ **カナル部は外耳道（EAM）の後下壁を避けているか？**（Arnold 咳嗽反射の誘発領域。約 2–4% の利用者に咳嗽が生じる）
- [ ] 保持力は主に耳輪（helix）／対耳輪（antihelix）が担っているか？
- [ ] 耳甲介舟（cymba conchae）への持続的な集中圧迫を避けているか？
- [ ] 文書やマーケティングで自律神経（autonomic）への効果を主張していないか？（taVNS の文献は電気刺激であり、受動的圧迫へ外挿できない）

## C. 設計可能領域（Part 4）

- [ ] ⛔⏳ **横向き寝の境界を満たすか？ 判定基準は形態ごとに異なる。Part 4.2.1 参照。** 現時点で**数値がなく**、実測後に記入する必要がある
  （**シーン A のみ該当。シーン B は枕による圧迫がないため本項は成立しない**——これは座位睡眠が解消する最大の制約である）
  - カナル型 → 耳介外縁に対する突出高さ
  - イヤーフック型 → 頭部側面最外縁の厚さ ＋ 乳様突起部（mastoid）への圧力 ＋ 耳介が折れ曲がらないこと ＋ フックが剛体レバーでないこと
  - フラットオーバーイヤー型／ヘッドバンド／骨伝導 → Part 4.2.1 の該当行を参照
- [ ] **突出高さは代理指標にすぎず**、本当の物理量は枕から耳へ伝わる接触圧であることを理解しているか？（低くても硬く尖った突起は、高くても幅広く丸く弾性のあるものより痛いことがある）
- [ ] イヤーフック型専用：耳後部本体は十分に薄くしたか？ フックはレバー増幅を避けるため低剛性としたか？
- [ ] ⛔ **イヤーフック型を選ぶ場合：実機による横向き寝検証を計画に入れたか？** 本ガイドラインはイヤーフック型について**実測に基づく根拠を一切持たない**（耳後部のスキャンデータがない）。Part 4.2.2 はすべて推論であり、**そのまま確定してはならない**
- [ ] 幾何は解剖学的エンベロープ内にあるか？（**機種 S／M／L は同一の耳に装着できる 3 種類の本体サイズであり、耳のサイズ区分ではない**。3 つの機種は同一のエンベロープを共有し、それぞれが耳型の全範囲を収容しなければならない）
- [ ] 3 種類の「サイズ」を区別しているか？ **機種 S／M／L**（本体の大きさ）／**イヤーチップ XS〜L**（アクセサリ）／**耳型区分 I／II／III**（利用者の耳の大きさ）。Part 0.4b 参照
- [ ] 寸法の基準に**アジアの成人**データを用いているか？（集団差が顕著であり、欧米のデータと混用してはならない）
- [ ] 解剖学的エンベロープは男女別か？（耳の寸法は分ける。圧迫しきい値は分けない）
- [ ] **角度**を伴う保持構造で、左右共用を前提としていないか？（角度系の寸法は左右非対称）
- [ ] 2 つの境界が衝突する場合、横向き寝の境界を優先しているか？

## D. 音響（Part 5）

- [ ] 前気室（V_front）／後気室（V_back）の容積は定義済みか。各機種のシェル容積に応じて比例配分しているか？
- [ ] ⛔ **漏れ経路は実際の幾何形状を示しているか**（狭隙は幅×高さ×長さ、円孔は半径×深さ）。**等価面積のみになっていないか？**（幾何が質量支配か粘性抵抗支配かを決める。誤ると静かに誤り、エラーにならない）
- [ ] **漏れ経路の幾何に測定時の顎の状態を明記しているか？** 密閉型カナルは開口状態を基準とするか両方を併記する——静止測定は漏れを過小評価し遮音を過大評価する（Part 1A の仰向け寝での外耳道変形を参照）
- [ ] シミュレーションが信頼できる周波数上限を理解しているか？（カナル型 L≈8–12mm → ~3.5–5.4 kHz。オーバーイヤー型 L≈20–30mm → ~1.4–2.1 kHz）
- [ ] 上限を超える音響性能について、シミュレーションではなく実測で検証する計画があるか？
- [ ] 完全密閉を採る場合、オクルージョン効果（occlusion effect）に対処しているか？

### D-2 条文レベルの点検（2026-08-25 追加。[Part 5](05-acoustic-constraints.md) 改訂に対応）

**⚑ 構成の宣言（他の音響項目の前提）**
- [ ] **⚑ 5.2-1 構成をベント型か密閉型か宣言済み**——未宣言なら 5.2-2〜5.2-8 はすべて「判定不能」とする

**ベント型ダクト**〔構成が密閉型なら本組は「非該当（5.2-1＝密閉型）」〕
- [ ] 5.2-2 目標同調周波数 f₀ と接続される空洞体積 V を明記済み
- [ ] 5.2-3 断面積 A と長さ L は f₀ と V から逆算したもので、両者を個別に指定していない
- [ ] 5.2-4 明記した A・L・ΔL・V を f₀=(c/2π)√(A/(V·L_eff)) に代入して明記の f₀ が再現できる
- [ ] 5.2-5 孔径は CAD 側で収縮量を事前補償済み（公称 d を d/(1−u) で作図、u は当該工程の収縮率）

**密閉型ダクト**〔構成がベント型なら本組は「非該当（5.2-1＝ベント型）」〕
- [ ] 5.2-6 ヘルムホルツ f₀ の逆算をダクト寸法の決定に使用していない
- [ ] **5.2-6b〔5.2-6 と対〕ダクト寸法の決定根拠を記載済み**（容積配分／高域上限／漏れ経路としての役割）、または欠落として登録済み
- [ ] 5.2-7 ダクト内容積を V_front に算入済み
- [ ] 5.2-8 f₀ の収縮補償を適用していない（密閉型に f₀ の設計目標は存在しない）
- [ ] **5.2-8b〔5.2-8 と対〕収縮量が V_front の容積計算に与える影響を算入済み**

**開口数と孔軸**
- [ ] 5.2-9 同一音響機能の開口は単一である。複数の場合、端補正の未確定領域（孔中心間距離／孔半径 2–10）に該当することと、f₀ 変位の方向・大きさが未確定であることを明記済み
- [ ] 5.2-10 **音響孔の軸を造形 Z 軸と平行に指定済み**。平行でない場合、内部サポートが完全に除去可能であることを検証済み（除去不能なものは音響経路の喪失とみなす）

**⚑ 漏れ経路**
- [ ] **⚑◆ 5.3-1a 幾何形式**：スリットは幅×高さ×長さ、円孔は半径×深さで与えること。**等価開口面積のみは不可**〔**現時点で判定可能**〕——未達なら 5.3-2〜5.3-5 は「判定不能」（モデルを支えられない形状の上に状態を注記しても、チェックは付くが実質がない）
- [ ] **◆ 5.3-1b 取得状態**：当該形状は**装着・受荷重状態で取得**し、5 つの状態次元を明記すること。**CAD の公称値を本欄の入力としてはならない**〔しきい値系。試作機待ち〕
  > **分割する理由**：元の条文の「実形状」という語は多義的であった——意図は「等価面積ではなく幾何形式」だったが、「実際に測った寸法」とも読める。**設計者が CAD の公称スリット幅を記入しても字面上は適合する**が、それは無荷重・未装着・室温の値である。**接触面積 A_i と同じ問題：異なる状態から来た数値どうしを除算・代入しても物理的な意味がない。**
- [ ] 5.3-2 顎の状態（閉口／開口）を明記済み
- [ ] 5.3-3 熱の状態（装着直後／熱平衡後）を明記済み
- [ ] 5.3-4 代表状態は「開口×熱平衡後」、または 4 組すべてを提示済み
- [ ] 5.3-5 漏れ経路の寸法が造形特徴ではなく組立公差の積み上げで決まる場合、別途サンプリング規定を定めている（状態注記は個体内変動を覆うが**個体間変動は覆わない**）
- [ ] **5.3-6 挿入深さを分布として与えている（単一の代表値ではない）**

- [ ] **◆ 5.3-7 測定計画に各量の測定順序と間隔時間を明記済み**〔**現時点で判定可能**〕

> **★ 試作機の測定計画は統合すること。ただし「統合」＝同一装着で順に測ることであり、同時測定ではない。**
> 挿入深さは密閉位置と挿入後の残存外耳道容積を同時に決めるため、**漏れ形状と接触力 F_i の分布要求は同一の収集アクションから来る**。分けて計画すると 1 巡余分になり、2 組のデータが異なる装着状態から取られれば相互に照合できない。
> **⚠️ しかし同時には測れない**：F_i／A_i は接触界面に圧力センサフィルムを置くが、**フィルムには厚みがあり締め代と密着を変える**。漏れ形状は界面が原状であることを要する——**フィルムを挟んで測った隙間は、フィルムなしの隙間ではない**。干渉源は測定器具そのものである。
> **⇒ 同一装着・順次測定・順序固定。どちらを先にするかは前の測定が残す擾乱への鈍感さで決まり、実際に試すまで確定しない。**
> **順序と間隔は必ず記録すること（5.3-7）**。さもなければ 2 組の数値の比較可能性を事後に再構成できない。

**⚑ シミュレーション信頼限界**
- [ ] **⚑ 5.5-1 本設計の最大空洞／ダクト特徴寸法 L を明記済み**——未明記なら 5.5-2 は「判定不能」（設計者が 2 つの数値を書いても誰も検算できない）
- [ ] 5.5-2 L に基づき f_reliable=c/(8L) と f_breakdown=c/(4L) を明記済み
- [ ] 5.5-3 当該限界が保守的推定であることを明記済み（両端閉空洞の第一縦モードは λ/2 で、λ/4 より遅く現れる）

**計算の基準**
- [ ] 5.6-1 すべての【計算】値に温度・気圧の基準を明記済み（20°C、101.325 kPa 乾燥空気、ρ₀・μ・c の採用値を併記）
- [ ] 5.6-2 37°C 側の感度を明記済み（c と f₀ が約 +3%、s が約 −5%、δ が約 +5%）

## E. 構造と材料（Part 6）

- [ ] 肉厚は選定した造形プロセスの下限を満たすか？（FDM ≥1.0–1.2mm、荷重部材 ≥2.0mm。SLA 0.4–0.6mm）
- [ ] オーバーハング角はサポート不要の上限内か？（FDM 45°。SLA 30° かつ張り出し ≤2mm）
- [ ] ⛔ **耳シェル内腔のサポートは取り出せるか？**（完全に閉じた行き止まり穴を避けるか、可溶性サポート材を用いる）
- [ ] 軟質接触面は**複合方式**（硬質シェルを造形＋軟質チップを外部調達）か、**完全造形**か？ 完全造形の場合、接触面硬度の下限が約 Shore A 43–50（睡眠用イヤーチップに一般的な 10–20A よりはるかに硬い）となることを受け入れるか？
- [ ] Shore A と Shore 00 を混用していないか？（低反発フォーム／軟質ゲルは Shore 00、一般的なシリコーンは Shore A。数値は相互比較できない）
- [ ] 耐久試験方法は材料種別に対応しているか？（弾性材は ASTM D5963。硬質シェル塗膜は ASTM D4060。**両者を混用してはならない**）
- [ ] ISO 105-E04 を誤用していないか？（これは繊維製品の染色堅牢度であり、シリコーン／プラスチックの劣化には適用できない）

### E-2 条文レベルの点検（2026-08-25 追加。[Part 6](06-structure-materials.md) 改訂に対応）

**⚑ 製造帯域（以降どの条文群が適用されるかを決める）**
- [ ] **⚑ 6A-3-1 各音響開口が属する帯域を明記済み**
  - ≥2.0mm：水平孔が確実 → 孔フィーチャ条文を適用
  - ≥1.0mm かつ <2.0mm：垂直孔のみ確実 → 孔フィーチャ条文を適用、配置方向は固定
  - ≥0.5mm かつ <1.0mm：Z 軸垂直孔のみ辛うじて可能 → 孔フィーチャ条文を適用、配置方向は固定
  - **<0.5mm：造形の孔フィーチャとして成立しない → 6A-3-2 を適用。6A-2-4／6A-2-5 は「非該当（6A-3-1＝<0.5mm 帯）」とする**
- [ ] 6A-3-2 〔<0.5mm 帯のみ〕組立隙間による設計へ変更し、公差積み上げ解析を添付済み
- [ ] 6A-3-3 多孔配列の孔壁 ≥1.0mm（FDM 最小肉厚）
- [ ] 6A-3-4 穴径の収縮量を CAD 側で事前補償済み（10mm 以下は 2–4% 小さい。ベント型の補正計算は 5.2-5 の管轄）

**プリント配置方向**〔前提 5.2-10／ゲート 6A-3-1〕
- [ ] 6A-2-1 **前提 5.2-10 が合格済み**（孔軸が指定され方向が確認済み）
- [ ] 6A-2-2 筐体全体のプリント配置方向が 5.2-10 の孔軸に反していないことを確認済み
- [ ] 6A-2-3 DFM 上の理由（サポート低減／表面品質／強度／反り）で配置方向を変更した場合：孔軸が 5.2-10 を依然満たすことを再確認済み
- [ ] 6A-2-4 〔孔フィーチャ帯で適用〕水平穴の径 ≥2.0mm（FDM）
- [ ] 6A-2-5 〔孔フィーチャ帯で適用〕プリント Z 軸に沿った垂直穴の径 ≥1.0mm（FDM）

**⚑ 硬度値のスケールと温度基準**
- [ ] **⚑◆ 6C-2-1 各ショア硬度値に測定スケール（Shore A か Shore 00 か）を明記済み**——未明記なら硬度関連の全項目を「判定不能」とする。**Shore 00 の値を Shore A のしきい値に照合すると、全て合格し、かつ誤った組で合格する**
- [ ] 6C-2-2 各ショア硬度値に温度基準（室温、ASTM D2240 標準試験条件）を明記済み
- [ ] 6C-2-3 ギャップを記載済み：皮膚温下では室温規格値より実際に軟らかい、幅は未評価
- [ ] 6C-2-4 **〔前提 6C-2-3〕** 当該ギャップを保守的推定として扱っていない（装着感には有利、保持力には不利で二方向が相反）

**⚑ 接触パッチ毎の接触圧**
- [ ] **⚑ 6D-2-1 全ての接触パッチを個別に列挙済み**——未列挙なら 6D-2-2／6D-2-4／6D-2-5 は「判定不能」。**接触面積の合計では代替不可**
- [ ] 6D-2-2 荷重分布が不明な場合は最不利分布で計算済み
- [ ] 6D-2-3 耳珠（tragus）を配置禁止領域として指定済み（**⛔ 配置禁止であり「面積を十分取れば可」ではない**。圧迫に最も敏感な領域であり、かつ下顎運動による変形領域でもある）
- [ ] 6D-2-4 〔入力待ち〕各パッチが個別に A_i ≥ F_i / PDT(該当部位) を満たす
- [ ] 6D-2-5 〔入力待ち〕接触領域に R < X のエッジが存在しない（X は PDT から逆算）

> 6D-2-4／6D-2-5 の**入力待ち**は PDT の部位別絶対値である（Yuan et al. 2023, *Applied Ergonomics* 113:104078。ペイウォール。現時点で相対順位のみ取得）。**入手すれば 2 条とも同時に閉じられる。**

## F. 装着圧と快適性（Part 7）

- [ ] ⏳ **本項目はシミュレーション検証できず**、実機装着試験が必須であることを理解しているか？
- [ ] 短時間の PDT をそのまま一晩装着の圧力上限としていないか？（長時間の耐容値は必然的に低いが、どれだけ低いかのデータはない）
- [ ] 接触は点接触ではなく面接触か？
- [ ] 接触面は丸められ、鋭利なエッジや硬い稜がないか？
- [ ] Part 7.4 の 4 項目の実機試験を計画しているか？

**3 つの低コスト簡易スクリーニング（Part 7.4.1）——機器不要。これを済ませてから本測定へ：**

- [ ] **頭振り試験**：素早く首を左右に振り、上下に頷いたとき、イヤホンは微動だにしないか？ ずれる＝サイズが小さすぎるか角度が合っていない
- [ ] ⛔ **咀嚼／開口試験**：口を開閉し話す真似をしたとき、耳珠（tragus）に鋭い痛みが出ないか？ **出ればサイズが大きすぎる。直ちに 1 段小さくする——これは慣れの問題ではなく構造が合っていない**
- [ ] ⛔ **15 分ルール**：装着したまま 15 分歩く。**持続する圧迫感はすべて誤ったサイズの兆候であり、慣れるべきものではない**
- [ ] **装着角度**は耳介の曲線に沿っているか？ 角度がずれれば、サイズが正しくても痛む

## G. CMF（Part 8）

- [ ] ⛔ **スリープモードで充電ケース／ドックのインジケータは既定で全消灯か？**（充電ケースはベッドサイドで目を正面から向いており、イヤホン本体の光よりはるかに重要）
- [ ] 点灯が必要な場合、集団平均 24.6 lux ではなく**最も感受性の高い個人の 6 lux** を基準としているか？
- [ ] 輝度は照度計を用い、**実使用時の距離と角度で目の位置に到達する値**を測定して検証したか。LED のスペックシートを引用していないか？
- [ ] スリープモードで点滅／ブリージング効果を禁止しているか？
- [ ] 左右耳と表裏を**触覚で識別**できるか？（暗所で装着するため視覚に頼れない）
- [ ] 表面処理は想定する洗浄方法に耐えるか？（毎日の IPA 拭き取りはマット面を光沢化させ、設計を破綻させる）

## H. 文書品質（Part 0）

- [ ] 本ガイドラインに追記した各数値に【実測】【文献】【慣例】【推論】【要確認】を表示したか？
- [ ] 引用した論文を**実際に開いて読んだか**。検索要約から推定していないか？
- [ ] 引用した標準は番号と適用範囲を実際に確認したか。記憶で書いていないか？
- [ ] 根拠が見つからない数値は、**もっともらしい値を埋めるのではなく空欄にして【要確認】と表示したか**？

---

## 現時点で通過できない項目（正直な一覧）

- [ ] **◆ P9-A 本設計の受動遮音量を周波数帯域形式で明記済み**（オクターブまたは 1/3 オクターブ帯、可聴範囲を網羅）。測定・推定条件、根拠レベル、取得方法を併記
  > **本項はしきい値を一切必要とせずに実行でき**、しきい値が確定しても書き直しにならない。3 条件が要求する帯域は現時点ですべて未定である——(c) は警報規格待ち、(a) は内容戦略と環境騒音データ待ち、(b) は内容戦略待ち。**未定なのはしきい値だけでなく、どの帯域を見るべきかも未定である。** 帯域形式で記すことが唯一やり直しにならない方法であり、そもそも受動遮音は帯域ごとに記述する量で単一の数値ではない。

- [ ] ⛔ **遮音下限の数値しきい値は未確定。** 3 条件：(a) 安全な曝露レベルを超えない範囲で内容が聞こえること／(b) 同床者を起こさないこと／(c) 安全上重要な音で目覚められること。欠落：寝室の環境騒音レベル分布、SNR_min、覚醒しきい値、漏れ音の伝達量。**(c) は必須要件とするか製品層の裁定待ち。本項は現時点でチェック不可。** → [Part 5.4.1](05-acoustic-constraints.md#sec-5-4-1)

以下の項目は本ガイドラインの現段階で**数値しきい値がなく**、誰も照合できない。これは既知の欠落であり、見落としではない：

**登録形式は [Part 0.4c ⑦–⑩](00-scope-and-usage.md#sec-0-4c) に従う**：各項に**型**（取得型＝待てば手に入る／定式化型＝待っても来ない）、**転換条件**、**アクション種別**（文献／ツール／収集／裁定）を付す。**複数経路のものは経路ごとに状態を記し、裁定で閉じられた経路は必ず明記する。開いている経路だけを書いてはならない。**

| 項目 | 型 | 転換条件 | アクション種別 |
|---|---|---|---|
| ⛔⏳ **横向き寝の突出高さ上限** | 取得型 | 競合品のノギス実測 ＋ 枕の沈み込み実測 | **収集** |
| **PDT の部位別絶対値** | 取得型 | Yuan et al. 2023 の全文数値表を取得 | **文献**（ジャーナル購読） |
| アジア成人の**性別別の耳介外形**エンベロープ | 取得型 | 人口統計を伴う 3D スキャン、または系統的レビューの原著追跡 | **文献 または 収集** |
| 長時間の静的圧迫の耐容値 | 取得型 | 実機装着試験 | **収集**（試作機なし） |
| 硬度—圧力の対応関係 | 取得型 | 硬度違いのテストピースで界面圧を実測 | **収集** |
| パッシブ遮音の dB 目標 | 定式化型 | **まずどの帯域を見るかを決める**（P9-A 参照）。帯域未定では数値に意味がない | **裁定**（(c)／内容戦略）**→ その後に収集** |
| **F_i 各パッチの接触力** | **二層** | 第一層：**測定状態が未定義**（顎／熱／挿入深さ。代表値か分布か）→ **今すぐ決められる**<br>第二層：数値が未取得 | 第一層：**裁定（当方。外部依存なし）**<br>第二層：**収集**——⛔ **シミュレーション経路は task #3 の裁定により閉鎖済** |
| **耳甲介容積**（解剖量：この椀の大きさ） | 定式化型 | 点群上での P1–P5 の確実な検出（**Zhu et al. が定義は与えている。足りないのは検出能力であって文献ではない**） | **ツール／能力**——論文が 10 本あっても動かない。**アーキテクチャに依存せず、(c) に阻まれない** |
| **筐体の利用可能総容積**（設計量：本体が実際に占められる量） | **二層** | 第一層：**アーキテクチャの選択**（深部挿入／耳甲介着座／安全通気孔の要否）＋ 装着余裕<br>第二層：耳甲介容積 | 第一層：⛔ **裁定／(c) により停止**——安全通気孔の要否が本体形態と占有可能範囲を変える<br>第二層：**ツール**（上行と同じ） |
| **左右対称性（当方データが発言できるか）** | 定式化型 | 同一耳の反復測定によるノイズの独立推定 | **収集**——現有データでは補えない |
| **多孔の端補正の未確定区間**（孔中心間距離/半径 2–10） | 定式化型 | 当該区間を覆う検証可能な文献 | **文献**——⛔ **BEM/FEM 経路は task #4 の裁定により閉鎖済。並行する代替案ではない** |
| **粘熱スリットのインピーダンス式が未照合**（5.3 Crandall 引用） | 取得型 | 権威ある出典で当該式を照合 | **文献**——**今すぐ着手可能。停止対象の影響を受けない**。⚠️ **解錠されるのは方法であって数値ではない**：振動スリット解を補っても得られるのは区間ごとのインピーダンス式であり、その入力 h(θ) は個人差があるため試作機のパッチ別圧力図と漏れ測定を要する → **下流は直ちに「試作機待ち／(c) 待ち」に接続する** |
| **⛔ スリット高不均一性の補正倍率** | **欠落ではなく、問いの立て方の誤り** | **なし**——平均を固定しても倍率に上界がなく（N^(n−1)、N→∞ で非有界）、建模者の区間分割数にも依存する | **⛔ 該当なし。**「文献待ち」として登録してはならない——出典が来れば書けると誤読される。**必要なのは係数ではなく区間ごとの h(θ) である** |
| **メッシュ前容積の無関係性基準** | **二層** | 第一層：判定基準の形式が未定——**トポロジーは固定方式に依存し、設計が決まれば一意になる**<br>第二層：メッシュの R ＋ 固定構造の実形状 | 第一層：⛔ **上流の設計で停止中**（固定方式が停止対象内）<br>第二層：**サプライヤ仕様 ＋ 機構設計** |

> ⚠️ **2 つの欠落群に共通の根はない**：音響側が待つのは粘熱／放射インピーダンスの参考文献、機構側が待つのはランドマーク検出能力・ジャーナル購読・収集設計である。**1 つのアクションで両側が解けることはない——優先順位を決める際、存在しないてこ点を探す必要はない。**
>
> **⛔ 裁定により閉じられた経路（逆参照。[0.4c ⑨](00-scope-and-usage.md#sec-0-4c) 参照）**：
> - **task #3**（接触力シミュレーションを投入しない）→ **F_i** のシミュレーション経路を閉鎖
> - **task #4**（音響 FEM/BEM を導入しない）→ **多孔の端補正** の数値解経路を閉鎖
> **再開に必要なのは資源ではなく、当該裁定を覆すことである。** いずれの裁定も当初の理由は現時点でも成立している。
| 睡眠用イヤーチップ 10–20A の硬度 | 独立した第 2 の出典がない | 市販品を実測、またはメーカー仕様を取得 |
