showmin/ear_3d_model_survey/jp/02-anthropometric-basis.md

# Part 2 — 人間工学・解剖学的基準

ステータス：**耳介外形と耳甲介深さは【実測】完了。P1–P5 を要する耳甲介寸法は【文献】に切替** ｜ 最終更新 2026-08-24

> 🌐 中文版：[cn/02-anthropometric-basis.md](../cn/02-anthropometric-basis.md)
> **用語規範**：耳の部位名と医学用語は日本語を先に、英語を括弧内に記す。

---

## 2.0.0 ⚠️ 本章のデータは何に答えられ、何に答えられないか

**答えられる：「収まるか」。** 寸法データは幾何学的な実現可能性を規定する——本体が入らないか、エンベロープを超えるか。

**答えられない：「装着して快適か」。**

| 項目 | 内容 | 証拠等級 |
|---|---|---|
| 耳の寸法と主観的な快適性／フィット評点の相関 | **耳の左右対称性、性別、耳甲介長、耳甲介腔幅**と知覚評点の相関は**いずれも有意でないか非常に弱い** | 【文献】⑤ |
| 何が快適性／フィットに有意に影響するか | **使用状況（use condition）と製品サイズ（product size）** | 【文献】⑤ |
| 静的 vs 動的 | **利用者は動的な状況でより大きい製品サイズを好む**（静的ではそうならない） | 【文献】⑤ |

> **推論**：快適性は「利用者の耳を測る」ことからは導けず、「実際の製品を装着して」測るしかない。
> 本章のデータの役割は**幾何学的に成立しない案を排除すること**であり、**最も快適な案を選ぶこと**ではない。後者は [Part 7](07-wearing-pressure-comfort.md) を参照。

**統計上の限界**：出典⑤ は 30 名（男 15・女 15）。**この標本規模での「有意に達しない」は弱い証拠であり、無関係であることの証明ではない**——検出力不足の可能性がある。したがって上記は「寸法の予測力は 30 名の標本で顕在化するほど強くない」と読むべきであり、「寸法がまったく無関係」ではない。

## 2.0 データ源

本節の数値は公開学術データセット **AudioEar3D** に対する実測であり、文献の引用ではない。

| 項目 | 内容 |
|---|---|
| データセット | AudioEar3D、出典① |
| 標本 | **56 名、左右耳あわせて 112 組**の 3D スキャン点群（binary PLY、1 耳あたり 9–24 万頂点） |
| スキャナ | MantisVision F6-SR（面内分解能 0.1mm、深さ分解能 0.4mm）① |
| ライセンス | CC BY 4.0。論文に完全な匿名化処理済みと明記 |
| 単位 | **mm**【推論】— 2.1 参照 |

### ⚠️ 2.0.1 確定した 3 つのデータ上の制約——これは成果物の境界であり、未補充項目ではない

> **状態の説明**：需求方が 2026-08-21 に**他の利用可能データがない**ことを確認済み（人口統計なし、耳後部スキャンなし）。
> 以下の制約は**後続データで埋まることはない**。本ガイドラインの恒久的境界とみなし、2.0.2 の代替手段に従って処理すること。

**一、年齢・性別・民族のデータがない。**
フォルダは 001–056 の番号のみで、論文全文にも公表されていない。したがって：
- **需求方の指示どおり男／女に分けることができない。** 本節は性別を分けない全体分布である。これはデータの制約であり、指示に従わなかったのではない。
- **アジア基準であると主張してはならない。** 研究機関は中国（上海交通大学、安徽大学）に所在し被験者は華人が主である可能性があるが、論文に明記がなく、これは推論であってデータではない。**本節の適用集団は「未確認」と表示する。**

**二、耳介本体のみを含み、耳後部と乳様突起部（mastoid）を含まない。**
論文原文：身体の他の部位を除去し耳の部分のみを保持したと記載。レンダリングした三面図でも一致を確認。
→ **イヤーフック型（ear-hook）に必要な耳後部の空間は本データでは評価できない。** Part 4.2.2 の関連内容は【推論】のままとする。

**三、外耳道（ear canal）深部のデータがない。**
55 個の注釈ランドマークのうち外耳道は入口 1 点のみ。構造化光スキャンは物理的に外耳道内部を撮影できない。
→ 外耳道の深さ、**入口の直径と角度**はいずれも**本データからは取得できない**（単一点は位置しか与えず、直径も角度も与えない）。

---

### 2.0.2 代替手段——制約が固定である以上、代替経路を示す

**「ない」と言うだけでなく、各制約に対する実務的な処理方法を以下に示す。**

| 制約 | 代替手段 |
|---|---|
| **男／女に分けられない** | **「全域をカバーする」方針に変更。** 本 56 名には男女がともに含まれており未表示なだけであるため、2.2 の全体分布は**すでに両性の範囲を包含している**。分けて最適化できないだけである。設計目標を P5–P95 の全域カバーとすれば両性ともその中に入る。耳甲介領域で性別を分ける必要がある場合は 2.3 の【文献】値（同研究は男女別）を用いる。 |
| **年齢が低いか不明** | **⚠️ 年齢の影響は一様ではなく、3 分類で扱う**（2026-08-27 に出典④ に基づき修正）。<br>**① 出典④ が自身の定義のもとで年齢傾向を観察しなかった項目**：耳甲介深さ（CD）、耳珠高、耳介傾斜角。<br>⚠️ **「本プロジェクトの CD は年齢の割り引きを免れる」と書いてはならない。** 出典④ の CD は**彼らの操作的定義**であり、本プロジェクト 2.4 の CD は**別の定義**である（CD の定義差が 2 倍の食い違いを生みうることは本章で既に記録済み）。**「年齢傾向なし」が解剖学的性質であれば援用できるが、当該測定法の産物（例：基準面の選び方がたまたま年齢効果を打ち消す）であれば適用できない。この判断は未検証である。**<br>現時点の扱い：**本類には積極的な年齢余裕を加えないが、「高齢層への適用が確認済み」と表示してもならない。**<br>**② 年齢とともに着実に増加 → 上限側に余裕**：大半の線形寸法。耳甲介幅（CW）等の横方向寸法を含む。<br>**③ ⚠️ 複合量（容積・面積・比）→ 依然として余裕が必要。① に分類してはならない**：容積 ≈ 深さ × 横断面積。深さに傾向がなく横方向に傾向がある → **容積は依然として年齢とともに増加する**。三次元すべてが増加する場合より増分が小さいだけである。<br>**一般則：複合量の年齢挙動は、それを構成する次元のうち「傾向を持つもの」が支配する。「傾向を持たないもの」が決めるのではない。**<br>加えて**装着試験には高齢被験者を必ず含める**——本項は試験で補うのであって数値では補わない。[Part 9](09-checklist.md) に記載済み。 |
| **耳後部と乳様突起部がない** | **イヤーフック型を高リスク経路として明示。** 本ガイドラインはイヤーフック型の横向き寝性能について実測に基づく根拠を一切提供できず、[Part 4.2.2](04-max-design-envelope.md) の関連内容はすべて【推論】である。**イヤーフック型を選ぶ場合、実機検証を経てからでなければ確定してはならない。** 推論は検証ではない。 |
| **外耳道深部の寸法がない** | 挿入深さとイヤーチップ寸法は耳型（ear impression）または実機装着試験で決定すること。本文書から推定してはならない。 |
| **集団が未確認** | 2.2 の適用集団は「未確認」表示を維持する。2.3 は中国人サンプルでありアジアの参考にできるが、耳甲介領域に限る。 |

## 2.1 単位の根拠

データセットは座標の単位を明文で宣言していない。以下の 3 つの独立した証拠が mm に収束する：

| 証拠 | 内容 |
|---|---|
| スキャナ仕様 | MantisVision F6-SR のネイティブ仕様は mm 表記（0.1mm／0.4mm）① |
| 論文の誤差指標 | 論文は scan-to-mesh 誤差を mm で報告（平均 0.11mm）しており、**その誤差は本データの原スキャンに対して直接計算されている**。座標が実体単位でなければこの数値に物理的意味がない① |
| 桁の照合 | 被験者 001 の耳介長軸は 60.6mm（左）／61.9mm（右）であり、人間工学文献の成人耳介高の区間の中ほどに収まる |

**証拠等級：【推論、三方向の相互照合による。データセットは明文で宣言していない】。** 【文献】と表示してはならない——引用可能な公式の単位宣言が存在しない。

## 2.2 耳介外形エンベロープ【実測】

### 測定方法

各耳の点群に対して：中心化 → 3×3 共分散行列を計算 → 固有値分解 → 固有値の降順に PC1／PC2／PC3 の 3 直交主軸を取得 → 点群を各軸へ投影 → 各軸の最大値と最小値の差をその軸方向の広がりとする（すなわち点群自身の形状に沿い、**座標系の向きに依存しない**方向付きバウンディングボックス）。

**なぜ軸平行バウンディングボックスを使わないか**：15 名（30 耳）を抽出して確認したところ、長軸はいずれも +Y 方向にあるものの、PCA 主軸と Y 軸のなす角は 0°–29° に達した。Y 軸の座標範囲をそのまま取ると最悪で約 13% 過小評価する（cos 29°≈0.87）。この誤差の桁は無視できない。

**方法の検証**：データセットには位置合わせ前の中間ファイル `011/right (copy).ply` が混入しており、正式ファイルと同一スキャンの異なる向きの版であった。両者は原座標も軸平行バウンディングボックスも異なるが、**PCA range は完全に一致した**。方法が向きに影響されないことを実証している。当該ファイルは除外済みで、n=112 はクリーンな標本である。

### 統計結果

**「人」を単位とする（n=56）**。左右耳をそれぞれ測定して平均を取った。左右耳は独立標本ではなく、n=112 とみなしてはならない。

| 軸 | min | P5 | P25 | P50 | P75 | P95 | max | mean | std |
|---|---|---|---|---|---|---|---|---|---|
| **PC1 長軸**（耳介の長さ方向） | 56.9 | 59.8 | 63.8 | 66.5 | 69.6 | 73.0 | 75.7 | 66.6 | 4.4 |
| **PC2 幅** | 31.5 | 33.4 | 36.0 | 38.2 | 40.6 | 43.5 | 44.5 | 38.3 | 3.2 |
| **PC3 厚さ** | 17.6 | 19.0 | 20.2 | 21.5 | 23.3 | 25.2 | 28.7 | 21.8 | 2.2 |

単位 mm。PC1／PC2 の分布はおおむね単峰で正規に近い。PC3 はやや右に歪む（最大値は平均から 3.1σ、最小値は −1.9σ にとどまる）。

> ⚠️ **P5／P95 は n=56 では裾の不確かさが大きい**（第 5 百分位はおよそ 3 番目に小さい値にあたり、被験者 1 名で明確に動く）。**精密なしきい値として用いてはならない。** min／max と分布全体を併せて判断すること。

### ⚠️ 2.2.1 PC3 は「横向き寝の突出高さ」ではない

**両者とも「厚さ」と呼ばれるが、まったく別の量であり、混用すれば深刻な設計誤りを招く。**

| | PC3 厚さ | 横向き寝の突出高さ |
|---|---|---|
| 何を測っているか | **耳介自身の巻き込みの深さ**（耳介の前面と後面の間） | **装置が頭部側面輪郭からどれだけ突き出ているか** |
| 基準面 | 耳介の点群それ自体 | 頭部側面の平面 |
| 本データで取得できるか | できる。21.8mm（平均） | **できない——本データに頭部側面／乳様突起部がない** |

→ **21.8mm を横向き寝の設計根拠として用いてはならない。** 横向き寝の境界は [Part 4.2](04-max-design-envelope.md) を参照。依然として実測待ちである。

### 2.2.2 ノギス文献との比較可能性

PC1 の平均 66.6mm は、人間工学文献で一般的な成人耳介高（約 59–65mm）より大きい。**この偏差の方向は方法自体から予測でき、データの異常ではない**：

PCA の第 1 主軸は定義上、広がりが最大となる方向である。したがって PC1 に沿った差し渡しは数学的に**必ず**、他のいかなる軸に沿った差し渡し以上になる。解剖学上の superaurale–subaurale 線も含めてである。**PCA range は、いかなる 2 点間のノギス測定に対しても系統的に大きいか等しい。**

→ 本節の数値は**他の PCA／バウンディングボックス測定とは比較できるが、ノギス測定と無条件に比較してはならない**。引用時は操作的定義を明記すること。

### 2.2.3 左右対称性

| 軸 | mean(L−R) | std(L−R) | mean\|L−R\| | corr(L,R) |
|---|---|---|---|---|
| PC1 長軸 | −0.10 | 2.22 | 1.71 | 0.881 |
| PC2 幅 | −0.61 | 2.14 | 1.73 | 0.804 |
| PC3 厚さ | +0.65 | 2.79 | 1.82 | **0.430** |

単位 mm。

- PC1／PC2 は左右相関が強く（>0.80）、出典② の左右対称性の結論と方向が一致する → **左右を共通化できる**
- **PC3 の相関は明確に弱い（0.430）**。PC3 は固有値が最小の第 3 主軸であり、ノイズとスキャン取得のばらつきに最も敏感で、**PC1／PC2 より信頼度が低い**。重要な設計根拠とすべきではない
- 注意：出典② は**角度系の寸法が左右非対称になりやすい**と指摘している。本節の 3 軸はいずれも長さ系であり、**これをもって角度系の構造も左右共通化できると推論してはならない**（Part 4.1 参照）

## 2.3 耳甲介の寸法【文献】— 中国の若年成人、男女別

**本節は 2.0.1 の 2 つの制約を部分的に補う**：出典③ は中国人サンプルかつ男女別であり、アジア基準と性別区分の根拠として使える——ただし**耳甲介領域に限られ、年齢範囲にも制約がある**（下記の限界を参照）。

### 標本と方法

| 項目 | 内容 |
|---|---|
| 標本 | **中国の若年成人 310 名、18–28 歳**。女 141 名、男 169 名。左右耳とも測定 |
| 方法 | 耳型（ear impression）＋3D スキャン。1 耳あたり 7 ランドマーク |
| 測定 | 耳甲介の形態計測 12 項目 |

> ⚠️ **同一の 310 名標本に関する論文について、ランドマーク数とクラスタ数が二次情報源の間で食い違っている**：本節は出典③ の原文に従い **7 ランドマーク／12 測定**とする。別の二次的記述は「5 特徴点／7 特徴距離／24 クラスタ」とし、検索結果には Ji et al. (2018) が **27 クラスタ**に分けたとするものもある。3 者は互いに一致しない。
> **本ガイドラインは出典③ の原文で確認できる 7 ランドマーク／12 測定のみを採用する。** クラスタ数（24 か 27 か）は本ガイドラインでは使用しない。引用が必要な場合はまず Ji et al. (2018) の全文を取得して照合すること（同論文の Wiley 全文は 403 で未取得）。

### ランドマークの定義（この体系を採用し、独自定義を作らない）

| ランドマーク | 定義 |
|---|---|
| P1 | 前切痕（incisura anterior auris）縁の最後方点 |
| P2 | 耳珠（tragus）の隆起点 |
| P3 | 珠間切痕（intertragic notch）の最深点 |
| P4 | 対耳珠（antitragus）の隆起点 |
| P5 | 対耳輪（antihelix）の曲率が最大の点 |

### 数値（mean ± SD、単位 mm。∠θ は度）

| 測定 | 定義 | 左男 | 右男 | 左女 | 右女 |
|---|---|---|---|---|---|
| TL | 耳珠全長 P1→P3 | 18.07±1.35 | 18.37±0.91 | 16.64±1.21 | 17.03±1.22 |
| TL1 | P1→P2 | 9.38±1.09 | 8.84±0.93 | 8.68±0.97 | 8.26±1.00 |
| TL2 | P2→P3 | 8.69±1.11 | 9.53±0.95 | 7.96±1.13 | 8.77±1.09 |
| ATL | 対耳珠全長 P3→P5 | 13.85±1.25 | 14.19±1.05 | 12.45±1.28 | 12.88±1.17 |
| ATL1 | P3→P4 | 7.41±0.90 | 6.82±0.83 | 6.51±0.87 | 6.16±0.84 |
| ATL2 | P4→P5 | 6.44±0.88 | 7.37±0.89 | 5.94±0.91 | 6.72±0.83 |
| **CW** | **耳甲介幅 P1→P5** | **17.04±1.34** | **17.26±1.38** | **15.69±1.53** | **15.96±1.41** |
| BD | 耳珠—対耳珠の隆起間距離 P2→P4 | 16.10±1.36 | 16.38±1.20 | 14.93±1.40 | 15.25±1.34 |
| HECO | 外耳道開口高 | 9.82±1.06 | 9.93±1.13 | 9.46±0.91 | 9.71±**7.14** ⚠️ |
| WECO | 外耳道開口幅 | 7.74±1.10 | 7.98±1.02 | 7.14±0.86 | 7.41±0.58 |
| **CD** | **耳甲介深さ**（耳甲介最深点から P1P3P5 平面への垂距） | **10.19±0.93** | **9.83±0.81** | **9.65±0.94** | **9.53±0.98** |
| ∠θ | P1P3P5 平面と外耳道開口のなす角 | 62.36±7.42 | 61.87±7.56 | 61.74±7.60 | 61.33±7.82 |

∠θ を除くすべての測定で男女差が統計的に有意（p<0.05）であり、**男性がいずれも女性より大きい**。左右非対称も有意だが、**各項目の左右差はいずれも 1mm 未満**である。

> ⚠️ **HECO 右女の標準偏差 ±7.14 は原文の誤りと判定し、採用しない。**
> 根拠：①他の 43 個の線形測定の標準偏差は 0.58–1.53（平均 1.07）に収まり、7.14 は典型値の 6.7 倍である ②同項目の左女は ±0.91 であり、右耳が突然 ±7.14 になることはありえない ③正規分布とすれば**標本の 8.7% で外耳道開口高が負値**となり、物理的に不可能である。
> 1.14 または 0.714 が妥当と推測されるが、**これは推測であり記入しない**。当該セルは【原文に誤りの疑い】と表示する。他の数値は影響を受けない。

### ⚠️ 使用上の限界

| 限界 | 説明 |
|---|---|
| **年齢が 18–28 歳のみ**（**ただし影響は項目により異なり、表全体に一律ではない**） | **⚠️ 2026-08-27 に出典④ に基づき細分化：本表のすべての行が同じように年齢の影響を受けるわけではない。**<br>**影響を受ける（そのまま適用すると系統的に小さすぎる）**：耳甲介幅（CW）、耳珠全長（TL）、外耳道開口幅（WECO）等の線形寸法——出典② は耳の寸法が生涯増大し続けると指摘し、**出典④（1,120 名、15–79 歳）は「大半の線形変数は年齢とともに着実に増加する」と述べている**。<br>**影響を受けない**：**耳甲介深さ（CD）——出典④ が「特定の年齢傾向を示さない」3 項目の 1 つとして明示**（他は耳珠高、耳介傾斜角）。したがって本表の CD 値はサンプル年齢によって系統的に小さくなることはない。<br>加えて耳介の形態タイプと年齢層には明確な関連がある。睡眠補助製品の利用者は年齢が高く、本表の線形寸法部分は代表性を持たない |
| 耳甲介領域のみを対象 | 耳介全体の外形エンベロープは 2.2 の【実測】データを基準とする |
| 測定媒体が異なる | 本表は耳型＋スキャン、2.2 は点群の直接測定。両者を無条件に相互比較してはならない |

## 2.4 耳甲介深さ CD【実測】

### 操作的定義（出典③ の CD と**同一ではない**）

耳甲介最深点をアンカーとする → その周囲の環帯内の前面側の点（椀の縁の近傍）を取る → その点群に最小二乗平面フィッティングを行う → 耳甲介最深点からその平面への垂直距離を取る。

**環帯半径は各耳自身のスケールに応じて縮尺する**（当該耳の PC1 の 7.6%–30.3%）。固定の絶対値ではない。これは改良版であり、固定絶対半径の初版は却下済み。2.4.2 参照。

> ⚠️ 出典③ の CD の基準面は **P1P3P5 の 3 点平面**（前方の 3 つの命名ランドマーク）である。本節の基準面は**椀の縁近傍のフィッティング平面**であり近似にすぎず、**同一の基準ではない**。両者は桁の比較はできるが、数値を直接照合してはならない。

### 統計結果（n=56、人単位、除外なし）

| 統計量 | 数値 (mm) |
|---|---|
| min | 6.43 |
| P5 | 7.34 |
| P25 | 8.80 |
| P50 | 9.29 |
| P75 | 9.75 |
| P95 | 10.30 |
| max | 10.87 |
| **mean** | **9.15** |
| std | 0.88 |

左右対称性：std(L−R) = 0.96mm、**corr(L,R) = 0.552**。

### ⚠️ 2.4.1 使えるのは平均値のみ。パーセンタイルと個別値は設計しきい値にできない

**corr(L,R) は実質的に本測定の信頼性係数である。** 左右耳を「同一の真値＋それぞれ独立なノイズ」として分解すると：

| 導出 | 初版（絶対半径） | **現行版（相対半径）** |
|---|---|---|
| 片耳測定ノイズ sd ＝ std(L−R)/√2 | 0.70mm | **0.68mm** |
| 真の個人間差 sd | 0.62mm | **0.74mm** |
| モデルが予測する corr(L,R) | 0.436（実測 0.437） | 0.541（**実測 0.552**） |
| **単回測定の分散に占めるノイズ** | 56% | **46%** |

> **単回の CD 測定の分散のうち約 46% は測定ノイズであり、真の解剖学的差異ではない。**【推論、実測データからの導出】
> 相対半径への変更で約 10 ポイント低下したが、**解消はしていない**。
>
> 厳密にはノイズ値は**上界**である——出典③ は左右耳に統計的に有意な真の非対称（<1mm）が存在すると指摘しており、L−R 差の一部は真の差である。

**したがって：**

| 使える | 使えない |
|---|---|
| **mean 9.15mm**（ノイズは 56 名で平均化され、標準誤差 ≈0.12mm） | **P5 = 7.34mm を「最も浅い耳甲介」の設計下限としてはならない** |
| 桁と分布形状の定性的な読み取り | 個々の被験者の CD 値 |

> ⚠️ **本節で設計に安全に使える数値は mean のみである。** パーセンタイルと個別値はいずれもノイズが支配的である。

#### この信頼性指標の既知の盲点

上記の分解は左右耳の差からノイズを推定している。**ある偏りが同一人物の左右耳で一致している場合、この方法はそれを見ることができない。**

現行版は環帯半径を PC1 に応じて縮尺しており、同一人物の左右耳の PC1 はほぼ同じである——**したがって耳の大きさに応じて変化する系統的偏りはすべて L−R 差で相殺され、corr(L,R) には現れないが、「人と人の間」の分散推定を膨らませる。**

まさにここに注意が必要である：真の個人間 sd が 0.62 から 0.74 へ上昇したのは、初版の環帯が大きすぎて真の差を圧縮しており現行版がそれを回復した（楽観的解釈）とも解釈できるし、縮尺がスケール依存の偏りを持ち込んだとも解釈できる。**L−R 基準では両者を区別できないため、以下の検定を別途行った。**

#### スケール依存偏りの検定——「持ち込まれている」と判断する方向

**観察**：CD と耳介全体寸法（PC1）の相関は、初版 0.29 → 現行版 **0.54**。

**検定 1：減衰補正。** 測定ノイズは観測相関を希釈する（classical attenuation、観測 r ≈ 真の r × √信頼性）：

| 版 | 信頼性 | 観測 r(PC1,CD) | 逆算した真の r |
|---|---|---|---|
| 初版 | 0.437 | 0.29 | 0.44 |
| 現行版 | 0.552 | 0.54 | **0.73** |

両版の違いがノイズ量のみであれば、逆算される真の r は一致するはずである。実際には大きく異なる。**真の r が初版の逆算値 0.44 であるなら、現行版は信頼性 0.552 のもとで 0.33 しか観測しないはずだが、実測は 0.54 であり +0.21 超過している。**

この結論の方向は堅牢である：前節のとおり L−R 基準は左右耳に共通する偏りを見られないため、スケール依存偏りが実在するならそれは「真の分散」に計上され、**現行版の信頼性を過大評価する**。この偏りを補正すれば逆算される真の r はさらに高くなり、**本結論を弱めるどころか強める**。

**検定 2：統計的有意性——結論に至らない。** Fisher の z 検定では、0.29 と 0.54 の差は n=56 で約 **1.6 標準誤差**（独立標本近似。2 つの相関係数は同一集団から得られ互いに正相関するため実際の標準誤差はより小さく、真の有意性はやや高い）。**示唆的な証拠であり、決定的ではない。**

**機構面の傍証**：耳が大きいほど → 環帯の絶対半径が大きくなる → サンプリングが耳介のより外側へ及ぶ → その部位は頭部方向へ折れ曲がっている → フィッティング平面が後退する → 測定される深さが大きくなる。**大きい耳→CD 大**であり、観察された正相関の方向とちょうど一致する。初版の固定半径にはこのスケール依存の変位がない。

> **結論**：現行版はスケール依存成分を持ち込んでいると判断する方向にあるが、証拠は示唆的であり決定的ではない。
> **「CD 分布のうち耳の大きさから独立した真の変動」という主張は厳しく見るべきである。**
> **mean 9.15mm は影響を受けず**、本節で設計に安全に使える唯一の数値であり続ける。

### 2.4.2 テストのうえ却下した 2 つの改善方向

付録ではなく本文に残す——P5=7.34 を見て低域を切り落とそうとする人が現れたとき、この記録は読まれるべき場所に現れる必要がある。

#### 却下 1：低域の外れ値を除外する

初版で CD が最も低い 5 耳を確認したところ、確かに検出上の欠陥が見られた（最深点が窪みの中心からずれる、固定絶対半径の環帯が耳に対して大きすぎる）。除外後 n=51 で mean 9.26／std 0.60／P5 8.25 となり、**当時のノイズ分解の予測（真の sd 0.62、生物学的 P5 ≈8.1）と高度に一致した**。

**しかしこの除外は却下し、採用していない。** 理由：

1. **選択バイアス**：低域だけを確認して低域を除外している。同じ基準で CD 最高の 5 耳と中位のランダム 5 耳を確認したところ、**同じ環帯スケールの欠陥が中位と高域にも見られ、比率に明確な差はなかった**——欠陥は全体的な方法上の限界であり、低域固有ではない。
2. **推測した機構が反証された**：当初は「小さい耳→環帯が大きすぎる→CD が低い」と推測した。実際に確認すると低域 5 耳の PC1 平均は 65.1mm で全体平均 66.6mm と同程度であり（5 耳中 3 耳は平均より大きい）、全体の PC1 と CD の相関はわずか 0.29 であった。**低い CD は小さい耳とは無関係である。**
3. **一致は弱い証拠**：どんな分布でも片側の極値を 5 個切り落とせば標準偏差は下がる。したがって 0.60 まで下がったことは除外の正しさの反証にならない。

> **本節は n=56 を維持し、除外を行わない。** 注：**ノイズ分解の結論はこの却下の影響を受けない**——当該分析の入力は std(L−R) と人単位平均の sd であり、低域標本を含めるか否かとは無関係である。その検証は予測 corr と実測値の照合による。

#### 却下 2：固定絶対半径の環帯

初版の環帯は固定 5–20mm であり、耳自身のスケールに応じて縮尺していなかった。寸法にばらつきのある母集団では既知の弱点である。**相対半径（PC1 の 7.6%–30.3%）に変更し、112 耳すべてを再実行した。**

改善の成功判定基準は**再実行前に事前定義**し、事後の合理化を避けた。判定基準の根拠：左右耳の真の解剖学的差は生物学的事実でありアルゴリズムによって変わらない。したがって L−R のばらつきは**測定ノイズの減少によってのみ低下しうる**——これはアルゴリズムの影響を受けない独立指標である。

| 指標 | 初版 | 現行版 | 事前に定めた方向 | 結果 |
|---|---|---|---|---|
| std(L−R) | 0.99mm | 0.96mm | 低下 | ✓ |
| corr(L,R) | 0.437 | 0.552 | 上昇 | ✓ |
| 片耳ノイズ sd | 0.70mm | 0.68mm | 低下 | ✓ |

3 項目すべてが適合したため現行版を採用した。**ただしこの判定基準には盲点がある。** 前節参照。

> ⛔ **P5 = 7.34mm を設計下限とすることは、測定誤差に合わせて設計することに等しい。**

同源の注意：2.2.3 の PC3 corr(L,R)=0.430 は本節の 0.437 とほぼ同じであり、**本データセットにおける深さ系測定の信頼性はこの桁である**。

### ⚠️ 2.4.3 ネット情報と照合するときの落とし穴：「耳甲介深さ」に統一された定義はない

**ネットを調べると「耳甲介深さ 14–17mm」といった数値が出てきて、本節の 9.15mm と 2 倍近く違う。これは通常どちらかの計算間違いではなく、測っている線が同じでないためである。**

| 表記 | 典型値 | 何を測っているか |
|---|---|---|
| 本節と出典③ | **9–10mm** | **耳甲介の椀の縁の平面**から窪みの底まで |
| 一部の文献／ネット情報 | **14–17mm** | **耳介外縁／耳輪**から底までと推定される——対耳輪の壁の高さが余分に加算されている |
| 耳甲介の**直径／幅** | 15–20mm | 深さではまったくない。本文書の CW（出典③）は男 17.0–17.3、女 15.7–16.0mm であり、14–17mm と大きく重なる |

**文献における「耳甲介深さ」の報告値の幅そのものが 9–16.8mm であり、そのばらつきは各研究の測定方法の違いに明確に帰せられている**（多くの研究は定義を明記していない）。

> ⛔ **異なる出典の耳寸法を混用してはならない。** 各数値はそれぞれ固有の基準面定義に紐づいている。
> これは 2.2.2 の「本節の PCA 数値をノギス文献と無条件に比較してはならない」と同一の原則である。

**設計時にどちらを使うか**：「本体を耳甲介の椀に収める」ための寸法決めなら、縁基準（9–10mm のほう）を用いる。「耳の表面から窪みの底まで」は別のより大きい数値であり、本体の使用可能厚さとは関係がない。

### 2.4.4 出典③ との対照

出典③ の CD：男左 10.19±0.93、男右 9.83±0.81、女左 9.65±0.94、女右 9.53±0.98。

本節の mean 9.15mm は文献各群の平均をやや下回るが同一の桁であり、分布は文献の区間と重なる。差異の要因として考えられるもの：基準面の定義が異なる（上記参照）、測定媒体が異なる（点群の直接測定 vs 耳型＋スキャン）、集団と年齢構成が異なる。

（初版の絶対半径法では「56 名中 23 名が文献の 9.53–10.19 区間に入る」と集計していたが、**その計数は現行の相対半径版で再計算していないため記載しない**。）

**この対照の価値は数値の一致にあるのではなく、「点群 → 耳甲介検出 → 深さ測定」というパイプライン全体の妥当性を独立に検証している点にある**——P1–P5 の命名ランドマークを取得できなかったとしても、耳甲介深さというこの中核的測定自体は成立している。

### 2.4.5 取得できなかった耳甲介寸法——文献に切り替え

耳甲介幅（CW）、耳珠全長（TL）、対耳珠全長（ATL）、外耳道開口の高さと幅（HECO／WECO）、開口角（∠θ）など、**P1–P5 の命名ランドマークを要する寸法は、当チームの自動検出では確実に取得できなかったため、2.3 の文献値を引用し【文献】と表示する。**

**技術的障壁**：データセットの 55 ランドマークは **2D 画像座標**（jpg 上に注釈）であり、3D 点群とは**同一の座標系ではない**。公式ソースコードを確認したところ、2D ランドマークは画像幅による正規化を行うのみで、カメラ内部パラメータも投影行列もない。論文にも写真とスキャンは別々の 2 回の撮影であると記載されている。**したがって既成の 2D→3D 対応は存在せず、命名ランドマークは 3D 点群上で直接識別する必要がある。**

**試行の経過と中止の理由**：耳甲介最深点をアンカーとし、環帯を角度でビン分割して「深さ—角度」の 1 次元信号を作る方法の枠組みは**成立した**（2.4.5.1 の中間発見① を参照）。しかしどのピークが耳珠に対応するかを判定できなかった——P1→P5 は耳甲介の**前方の局所弧**しかカバーしておらず、360° 走査で得られるピークには耳輪脚や対耳輪など、この連鎖に属さない構造が混入する。角度範囲を絞り込むにはまず「前方」の方向を確定する必要があるが、その確認に要する耳珠の 3D 座標は**静的なレンダリング画像から目視で確実に指し示すことができない**。

> **中止の理由は「その確認を確実に実行できない」ことであり、「確認の結果が否だった」ことではない。** 無理に指した座標は、標本間で一致しているように見えて実際には目測誤差の産物である結論を生み、しかも事後に誰も見分けられない。**したがって産出しない。**

#### 2.4.5.1 2 つの中間発見（後続の担当者向け）

1. **環状 1 次元信号によるランドマーク検出の枠組みは成立する。** 耳甲介アンカーを中心に 5–20mm の環帯を取り、角度でビン分割（5°×72 区画）して深さプロファイルを取ると、信号はクリーンで標本間の一貫性があり、ピーク／谷の交替リズムも解剖学的予想と合致する（5/5 標本で振幅が他より格段に大きい主ピーク＋規則的な 4 ピーク 4 谷が出現）。**枠組みは成立しており、欠けているのは最後の一片：前方弧における耳珠の命名的な位置決めである。** インタラクティブな 3D マーキング、または真の 2D–3D ピクセルレベル位置合わせのツールが必要である。
2. **原座標系（PCA 回転ではない）の Z 軸は標本を通じて一貫した深さ軸である。** Z-vs-Y 投影は 6/6 標本で正しく識別可能な耳の正面輪郭を与えたが、X-vs-Y はそうならなかった。既知の一貫した Y 軸（長軸）と合わせると、本データセットの原 XYZ が意味のある標準化された向きであり任意値でないことが分かる。**後続でランドマーク検出を再試行する際はそのまま流用でき、再発見の必要はない。**

## 2.5 未取得

**注意**：以下には**進行中**の項目のみを挙げる。取得できないことが確定したデータ制約は 2.0.1 と 2.0.2 にあり、ここには含めない。

| 欠落 | 取得方法 | 影響 |
|---|---|---|
| 高齢層の**数値**寸法 | 出典④ の存在は確認済み（1,120 名、15–79 歳、中国大陸、耳装着機器向け）だが、**数値表は有料の壁の内側で未取得**。取得までは 2.0.2 に従い「上限側に余裕＋高齢者の装着試験」で処理する | 中。代替手段があり阻害要因ではない |
| 耳後部と乳様突起部 | 頭部側面を含むスキャンを別途取得する必要がある | 中。イヤーフック型の評価に必要 |
| 外耳道深部と入口径／角度 | 耳型（ear impression）または他の測定手段が必要 | 中 |

---

## 出典

① Huang, X., Wang, Y., Liu, Y., Ni, B., Zhang, W., Liu, J., Li, T. **AudioEar: Single-View Ear Reconstruction for Personalized Spatial Audio.** *AAAI 2023*. arXiv: [2301.12613](https://arxiv.org/abs/2301.12613) ｜ データセット：Zenodo レコード 7592895 ｜ コード：github.com/seanywang0408/AudioEar
　種別：学術論文＋公開データセット（CC BY 4.0）。**arXiv ページを実際に開いて照合済み**（表題、著者、112 point cloud ear scans、55 landmarks がいずれも一致）。

② Fu, F., Luximon, Y. **A systematic review on ear anthropometry and its industrial design applications.** *Human Factors and Ergonomics in Manufacturing & Service Industries*, 2020, 30: 176–194. DOI: [10.1002/hfm.20832](https://doi.org/10.1002/hfm.20832)
　種別：学術論文。**ダウンロードして原文を読解のうえ確認済み。**

③ Zhu, Z., Ji, X., Gao, Z., Hu, G. **A Morphometric Study of Auricular Concha in the Population of Young Chinese Adults.** *International Journal of Morphology*, 2017, 35(4): 1451–1458.
　全文：<https://scielo.conicyt.cl/scielo.php?script=sci_arttext&pid=S0717-95022017000401451>
　種別：学術論文（オープンアクセス）。**全文を実際に開き、数値表をセル単位で転記した。** 注：`www.scielo.cl` の PDF と全文ページは Cloudflare に阻まれるが、`scielo.conicyt.cl` の旧ドメインなら取得できる。

④ Wang, M., Fan, H., Yu, S., Wang, L., Chu, J., Tang, X., Li, W., Zhao, X., Zhang, S., Chen, D. **Analysis of the auricles and auricular shape types for ear-related wearables: A study of mainland Chinese sample aged 15–79.** *Work*, 2022, 73(1): 335–352. DOI: [10.3233/WOR-210799](https://doi.org/10.3233/WOR-210799)
　種別：学術論文。中国大陸の被験者 1,120 名、15–79 歳、キャスティング（casting）＋3D スキャン、耳介測定変数 18 項目、耳介形態を 5 タイプに分類。
　**要旨は Europe PMC API で確認済み（2026-08-27 に一文ずつ再照合）。全文はクローズドアクセス（Unpaywall 照会：is_oa=false）で数値表は未取得。** 現時点では定性的結論のみを引用し、**数値は一切引用していない**：
　- 測定値は年齢とともに連続的に変化し、**大半の線形変数は着実に増加する**
　- **⚠️ 例外：耳介傾斜角・耳甲介深さ（conchal depth）・耳珠高（tragal height）の 3 項目は「特定の年齢傾向を示さなかった」**——原文：*"The auricular inclination angle, conchal depth and tragal height did not exhibit any specific trend across the age groups."* **本ガイドライン唯一の自前の実測値（CD）が年齢の疑義を免れる根拠はこの一文である。**
　- 形態タイプと年齢層が強く関連する（5 タイプに分類）
　- 男女とも有意な左右差は観察されなかった——**⚠️ この点は出典③（左右非対称は有意だが各項 <1mm）と一致しない——これは「二者」の不一致であり、三者ではない。**<br>**⛔ 本章 2.2.3 の PC3 左右相関 0.430 を 第三のデータ点として並べてはならない。** 低い相関は真の非対称からも測定ノイズからも生じ、**単一の相関係数の中では両者が交絡して分離できない**。本章は既に CD のノイズが分散の約 46% を占めることを分解しており、PC3 の 0.430 は CD の 0.437 とほぼ同じ——**それは深さ系測定の信頼性水準であって解剖学的結論ではない。本プロジェクトのデータは ③ と ④ の相違を裁定できず、どちらの側も支持も否定もしない。**<br>**さらに ③④ の測定方法は異なる**（③ は耳型＋3D スキャンの名前付きランドマーク、④ は方法未確認）。**方法が異なる以上、収束を期待すべきではなく、数値を調和させようとしてはならない。** 比較するならまず測定定義を統一すること

⑤ Fu, F., Luximon, Y. **Comfort and fit perception based on 3D anthropometry for ear-related product design.** *Applied Ergonomics*, 2022, 100: 103640. DOI: [10.1016/j.apergo.2021.103640](https://doi.org/10.1016/j.apergo.2021.103640)
　種別：学術論文。**要旨を Europe PMC API で確認済み。** 被験者 30 名（男 15・女 15）、被験者内計画。
　出典② と同一の著者群。原文の結論：耳の左右対称性、性別、耳甲介長、耳甲介腔幅と知覚評点の相関は有意でないか非常に弱い。使用状況と製品サイズは有意に影響する。動的な状況ではより大きいサイズが好まれる。
