showmin/ear_3d_model_survey/cn/01-use-scenario.md

# Part 1 — 使用場景定義

> **本章不含設計規則。** 這裡定義的是**前提**——產品用在什麼情況、使用者處於什麼狀態。後面每一條規則的數字都建立在這些前提上，前提一改，數字要重算。
> **要看實際的設計規則，讀 [GUIDELINE.md](../GUIDELINE.md)。**

狀態：初稿 ｜ 最後更新 2026-08-21

> 🌐 日本語版：[jp/01-use-scenario.md](../jp/01-use-scenario.md)

**所有約束的源頭。** 後面每一個數字都建立在這節的場景假設上；場景假設一改，數字要重算。

> **用語規範**：耳部與醫學名詞中文在前、英文於括號內。

---

> ⛔ **範圍裁定（2026-08-25）：第一階段只服務夜間長時間睡眠（整夜臥睡）。坐睡（辦公室午睡、交通工具）已移出。**
> 本章與坐睡／情境 B 相關的段落**保留但不適用於第一階段**——保留是為了讓「考慮後排除」與「未曾考慮」可以區分，未來擴充情境時可直接取用。
> **引用本章任何形態評分或約束時，必須確認該結論是否綁定坐睡。** 坐睡移出會翻轉部分形態的排序（掛耳式、頭帶眼罩式）。

> 📄 **三種睡姿（正睡／側睡／坐睡）的分別分析見 [附篇 1A](01a-posture-analysis.md)。** 本章定義場景，附篇 1A 逐姿勢拆解約束與設計判準。

## 1.0 兩個使用情境

需求方於 2026-08-21 追加**坐睡**情境。兩者的約束差異極大，**不可共用同一套判準**。

| | **情境 A：整夜臥睡** | **情境 B：坐睡** |
|---|---|---|
| 場合 | 臥室，整夜 | 辦公室午睡、大眾運輸、長途交通 |
| 佩戴時長 | 6–9 小時 | **20 分鐘–3 小時** |
| 側睡壓迫 | **主導約束** | **不成立**（無枕頭壓迫） |
| 主導約束 | 側睡凸出高度 | **固位穩定性** |

> 📄 **情境 B 須再分三個子情境**（B1 辦公室午睡／B2 短程通勤／B3 長途交通），三者在外觀規範、遮光需求與情境安全上差異大到會**翻轉形態評分**。見 [Part 1A.4.1](01a-posture-analysis.md)。

> ⏳ **待確認**：本產品服務 A、B、或兩者？三種答案下的指引內容差異極大——
> ①**僅 B** → 側睡約束整個移除，形態排序重寫
> ②**A＋B** → 須滿足兩組約束的**聯集**，側睡仍為綁定條件且較嚴
> ③**同系列兩產品** → 兩套規格分開撰寫

### 1.0.1 情境 B 的約束——不是「限制較少」，是「換一組限制」

| 面向 | 情境 A（臥睡） | 情境 B（坐睡） | 變化 |
|---|---|---|---|
| **固位** | 躺姿，重力方向穩定 | **打瞌睡時頭前傾、側倒，裝置可能脫落** | **更嚴苛** |
| 受壓 | 全身重量透過枕頭 | 靠頭枕、車窗、頸枕仍有側向接觸，但壓力低很多且位置不固定。**低但非零** | 大幅緩解 |
| 靜態受壓時長 | 可超過 30 分鐘不變位 | 時長本身較短 | 緩解 |
| 外觀 | 僅自己可見 | **公開場合可見** | **更嚴苛** |
| 環境噪音 | 安靜臥室 | **交通噪音，低頻為主** | 需求性質不同 |
| 情境安全 | 無 | **須聽得到廣播、不可坐過站。完全隔絕反成缺點** | **新增約束** |
| 穿脫頻率 | 一日一次 | 頻繁，好戴好收重要 | **新增約束** |
| 指示燈 | 暗室，關鍵約束（Part 8） | 白天環境，問題幾乎消失 | 大幅緩解 |

**頸枕（travel pillow）需特別注意**：U 型頸枕接觸的正是耳後與頭側，對掛耳式（ear-hook）有直接影響。

## 1.1 佩戴情境（以情境 A 為基準；情境 B 差異見 1.0.1）

| 項目 | 假設 | 來源等級 | 備註 |
|---|---|---|---|
| 佩戴時長 | **整夜（約 6–9 小時）連續佩戴** | 【假設】 | 待需求方確認。若改為「入睡後取下」，壓力與耐久要求可大幅放寬 |
| 使用姿勢 | 平躺於床，頭部接觸枕頭 | 【假設】 | — |
| 環境 | 室內臥室，可能有棉被覆蓋頭頸部 | 【假設】 | 影響散熱與濕氣累積 |
| 使用者狀態 | **無意識**——睡眠中無法主動調整配戴位置或反應不適 | 【推論】 | **這是睡眠耳機與一般耳機最根本的差異**，見 1.4 |

## 1.2 睡姿與翻身（有實證數據）

來源① 為實驗室多導睡眠圖（polysomnography）研究，五個年齡層各 10 人，連續數夜攝影記錄。

### 翻身頻率隨年齡顯著下降

| 年齡層 | 姿勢變換次數／小時 | 來源等級 |
|---|---|---|
| 3–5 歲 | 4.4 | 【文獻】① |
| 8–12 歲 | 4.7 | 【文獻】① |
| **18–24 歲** | **3.6** | 【文獻】① |
| **35–45 歲** | **2.7** | 【文獻】① |
| **65–80 歲** | **2.1** | 【文獻】① |

同時，來源① 亦報告隨年齡增長**姿勢維持時間延長**，且**超過 30 分鐘完全不動的時段數增加**。

### 姿勢分佈隨年齡改變

| 發現 | 內容 | 來源等級 |
|---|---|---|
| 兒童 | 俯臥（prone）、仰臥（supine）、側臥（lateral）約各佔相等比例 | 【文獻】① |
| 成人化趨勢 | **俯臥姿勢逐步消失** | 【文獻】① |
| 老年 | **明顯偏好右側臥（right-side position）** | 【文獻】① |
| 成人各姿勢確切百分比 | **待核** | 【待核】未取得可核驗數值 |

## 1.3 上述數據對設計的三個直接影響

**① 目標客群年齡偏高 → 靜態受壓時間更長。**
助眠產品使用者年齡通常偏高。65–80 歲翻身頻率僅 2.1 次／小時，約為年輕成人的 6 成，且超過 30 分鐘完全不動的時段增加。**這正是壓瘡與壓迫不適的典型受力條件**——不是尖峰壓力大，而是中等壓力持續太久。

→ 設計判準應為「長時間靜態接觸壓力」，不是「瞬間可承受壓力」。【推論】

**② 老年偏好右側臥 → 右耳承受的累積壓迫顯著高於左耳。**
→ 佩戴測試不應只做「側睡」，應**特別加重右側臥情境**；長時間耐受測試以右耳為主要樣本。【推論】
→ 若未來考慮左右不對稱設計，這是唯一有實證支撐的不對稱理由。（注意：來源② 指出角度類耳部尺寸本就左右不對稱，兩者可一併考量。）

**③ 成人俯臥罕見 → 不需為俯臥情境最佳化。**
設計資源應集中於側臥與仰臥。【推論】

### 證據限制
來源① 為 1992 年研究，**每個年齡層僅 10 人**（5 男 5 女），樣本小。趨勢方向可信度高（多項指標一致且呈單調變化），但絕對數值不宜當精確設計參數。年代較早，寢具與生活型態已有變化。

## 1.4 睡眠耳機與一般耳機的本質差異

這節的存在理由。設計者若把一般 TWS 耳機的規範搬過來，會在下列每一項出錯：

| 面向 | 一般耳機 | 睡眠耳機 |
|---|---|---|
| 使用者能否反應不適 | 能，隨時可調整或取下 | **不能。睡眠中無意識** |
| 受力型態 | 短時間、可中斷 | **長時間靜態受壓，最長可超過 30 分鐘不變位** |
| 外側壓迫 | 無 | **枕頭持續施壓**（見 Part 4 側睡邊界） |
| 可接受的凸出高度 | 寬鬆 | **極嚴格，是產品生死線** |
| 指示燈 | 無妨 | **暗室中可能干擾睡眠**（見 Part 8） |
| 咳嗽反射風險 | 短時間接觸，風險低 | **整夜接觸，風險放大**（見 Part 3.2） |
| 佩戴時長 | 數小時 | 6–9 小時連續 |

## 1.5 枕頭接觸（待補）

| 缺口 | 說明 | 阻塞程度 |
|---|---|---|
| 枕頭材質與下陷深度 | 不同枕頭（記憶棉、羽絨、乳膠）壓陷特性差異大，直接決定 Part 4 的側睡邊界 | **高** |
| 耳廓（auricle）受壓變形量 | 側睡時耳廓本身會變形，影響動態間隙 | 中 |

兩者皆須實測，見 Part 4.2 建議的量測方法。

---

## 來源

① De Koninck, J., Lorrain, D., Gagnon, P. **Sleep positions and position shifts in five age groups: an ontogenetic picture.** *Sleep*, 1992, 15(2): 143–149. DOI: [10.1093/sleep/15.2.143](https://doi.org/10.1093/sleep/15.2.143)
　類型：學術論文。**摘要已透過 Europe PMC API 取得並核對。** 方法：多導睡眠圖＋每 8 秒一格攝影記錄，五年齡層各 10 人。

② Fu, F., Luximon, Y. **A systematic review on ear anthropometry and its industrial design applications.** *Human Factors and Ergonomics in Manufacturing & Service Industries*, 2020, 30: 176–194. DOI: [10.1002/hfm.20832](https://doi.org/10.1002/hfm.20832)
　類型：學術論文。**已下載並讀取原文確認。**
