showmin/ear_3d_model_survey/cn/01a-posture-analysis.md

# 附篇 1A — 睡姿分別分析：正睡／側睡／坐睡

狀態：初稿 ｜ 最後更新 2026-08-22

> 🌐 日本語版：[jp/01a-posture-analysis.md](../jp/01a-posture-analysis.md)
依需求方 2026-08-22 指示，針對三種睡姿分別分析。

> **用語規範**：耳部與醫學名詞中文在前、英文於括號內。

---

> ⛔ **範圍裁定（2026-08-25）：第一階段只服務夜間長時間睡眠（整夜臥睡）。坐睡（辦公室午睡、交通工具）已移出。**
> 本章與坐睡／情境 B 相關的段落**保留但不適用於第一階段**——保留是為了讓「考慮後排除」與「未曾考慮」可以區分，未來擴充情境時可直接取用。
> **引用本章任何形態評分或約束時，必須確認該結論是否綁定坐睡。** 坐睡移出會翻轉部分形態的排序（掛耳式、頭帶眼罩式）。

## 1A.0 為什麼必須分姿勢談

**三種姿勢的「主導約束」完全不同，而且不是同一件事的程度差異。**

| 姿勢 | 主導約束 | 若只顧這一項而忽略其他 |
|---|---|---|
| **正睡（supine）** | **耳道變形**（下顎張開） | 密封失效、漏音、低頻流失 |
| **側睡（lateral）** | **凸出高度／傳遞壓力** | 痛到無法整夜佩戴，產品直接不可用 |
| **坐睡（seated）** | **固位穩定性** | 打瞌睡時脫落遺失 |

→ **「為睡眠設計」若不指明姿勢，等於沒有指明約束。** 一個在側睡下完美的設計，可能在坐睡下掉下來；一個坐睡下優秀的設計，側睡可能會痛。

**未涵蓋俯臥（prone）**：來源① 指出俯臥比例隨年齡**逐步消失**，成人已罕見，而本產品客群年齡偏高。若目標客群包含年輕族群則需另行評估。

### 姿勢偏好本身受不適驅動

來源④ 對 41 名中高齡成人做兩夜居家多導睡眠圖，結論：**部分個體對仰臥耐受度低**（仰臥時清醒指數相對高），**並以增加側臥比例來代償**。

→ 對本專案的意義：**姿勢偏好不是隨機分布，部分人是因為仰臥不舒服才轉側臥。** 這群人側臥比例會偏高，而側臥正是對耳機最嚴苛的姿勢。**設計若只顧平均姿勢分布，會低估側臥使用者的權重。**【推論】

---

## 1A.1 三姿勢速查表

| 面向 | 正睡（supine） | 側睡（lateral） | 坐睡（seated） |
|---|---|---|---|
| **主導約束** | 耳道變形 | **凸出高度／傳遞壓力** | **固位** |
| 耳部直接受壓 | 低。耳廓不承重 | **最高。** 全身重量透過枕頭 | 低但不固定（頭枕／車窗／頸枕） |
| 受壓部位 | 枕頭下陷時之耳廓側面 | 耳甲腔、耳屏；掛耳式則為乳突區 | 隨倚靠物而異，不可預期 |
| **固位難度** | **最低。** 重力大致垂直耳道軸 | 低。躺姿穩定 | **最高。** 頭前傾、側倒 |
| **下顎張開** | **常見**（仰躺時下顎鬆弛下墜） | 較少 | **常見**（頭前傾時嘴微張） |
| 佩戴時長 | 6–9 小時 | 6–9 小時 | **20 分鐘–3 小時** |
| 靜態受壓時長 | 長，但壓力低 | **長且壓力高**（可超過 30 分鐘不變位） | 短 |
| 環境噪音 | 安靜臥室 | 安靜臥室 | **交通噪音，低頻為主** |
| 外觀要求 | 低 | 低 | **高（公開場合）** |
| 環境感知需求 | 無 | 無 | **必要**（廣播、到站） |
| 指示燈約束 | **關鍵**（暗室） | **關鍵**（暗室） | 低（白天） |

---

## 1A.2 正睡（supine）

### 受壓情況

耳廓不直接承重，頭部重量由枕骨（occiput）承擔。**但不等於零接觸**：

- 枕頭偏軟或偏高時頭部下陷，**枕面會由側方接觸耳廓**
- 下陷較深時，枕頭邊緣可能**將耳廓（auricle）往前折**
- 壓力量級遠低於側睡，但接觸位置與側睡不同（耳廓外緣、耳後而非耳甲腔）

### ★ 正睡的特有問題：下顎張開造成耳道變形

**仰躺時下顎（mandible）容易鬆弛下墜、口部微張。** 顳顎關節（temporomandibular joint, TMJ）緊鄰外耳道（external acoustic meatus）前壁，下顎髁突（mandibular condyle）前下移動會牽動周圍軟組織與纖維軟骨，**使耳道在特定區域擴張或塌陷**。

| 證據 | 內容 | 來源等級 |
|---|---|---|
| 30 名受試者（9 女 21 男）耳印模比對 | **全部受試者在耳屏（tragus）與耳道皆呈現顯著變形**；形狀變異可解釋約 50% 的變形變異；變形量與性別有關聯 | 【文獻】② |
| 單一受試者矽膠印模＋MRI | 不同下顎位置下，耳道在**前後向（anterior/posterior）約 25% 變化**；上下向變化極小 | 【文獻】③（n=1，個案研究） |

**對設計的意義：**

1. **密封式入耳在正睡時有失效風險。** 入睡時口閉合、入睡後下顎鬆弛張開 → 耳道幾何改變 → 耳塞密封可能鬆脫。**低頻與被動隔音最先受影響**（見 Part 5）。
2. **變形集中在耳道軟骨部與耳屏**——而耳屏正是 Part 3 認定的**壓力最敏感區**。**同一個部位既最敏感、又會隨下顎移動**：以耳屏為固位支點的設計，同時承受這兩個問題。
3. 個體差異大（來源② 指出變形量與形狀變異相關），**無法用單一補償量涵蓋所有人**。

> ⚠️ **量測時的實務含意**：若日後取耳印模或做佩戴驗證，**須分別在口閉合與口張開兩種狀態下進行**。只取一種狀態會系統性低估所需的貼合寬容度。

### 其他考量

- **打鼾**：仰睡為打鼾與阻塞性睡眠呼吸中止較嚴重的姿勢【慣例，本團隊未核驗具體文獻】。若產品含鼾聲遮蔽功能，正睡是主要使用時機。
- **固位最寬鬆**：耳道軸向大致朝側上方，重力不直接把裝置往外拉。三種姿勢中固位要求最低。

### 正睡設計判準

- [ ] 耳塞是否能容忍耳道前後向變形而不失密封？
- [ ] 佩戴驗證是否涵蓋**口張開**狀態？
- [ ] 是否避免以耳屏為主要固位支點？
- [ ] 枕頭下陷時，耳廓外緣接觸區是否無硬稜或銳邊？

---

## 1A.3 側睡（lateral）

**本專案已針對側睡做最完整分析，詳見 [Part 4.2](04-max-design-envelope.md)。此處僅摘要。**

### 核心約束

**傳遞壓力**——枕頭透過裝置壓進耳朵的實際接觸壓力。凸出高度是最實用的代理指標，但不是物理量本身（另受枕頭順應性、凸起形狀、殼體剛性影響）。

**判準依形態族而異**（見 Part 4.2.1）：入耳式量相對耳廓外緣的凸出高度；掛耳式則須量頭側最外緣厚度、乳突區壓力、耳廓是否被折彎、耳掛是否成為槓桿。

### 側睡特有事實

| 事實 | 內容 | 來源等級 |
|---|---|---|
| **老年明顯偏好右側臥** | 隨年齡增長，右側臥偏好愈發明顯 | 【文獻】① |
| 翻身頻率隨年齡下降 | 18–24 歲 3.6 次/小時 → 65–80 歲 **2.1 次/小時**；超過 30 分鐘完全不動的時段增加 | 【文獻】① |

→ **右耳承受的累積壓迫高於左耳**，佩戴測試應加重右側臥。
→ 客群年齡偏高 → **長時間靜態受壓才是真正的受力條件**，不是瞬間尖峰壓力。

### ⛔ 最大缺口

**側睡凸出高度上限無公開數據，只能實測。** 廠商一律不公布，齊平（flush）是行銷用詞無量測定義。見 Part 4.2。

---

## 1A.4 坐睡（seated）

### 核心約束：固位

**打瞌睡時頭部前傾或側倒**，裝置面臨側睡所沒有的脫落力。且遺失後果較嚴重——辦公室或交通工具上不易尋回。

**這取代了側睡凸出高度的地位，成為坐睡的第一道門檻。**

### 受壓：低但不可預期

無枕頭壓迫，但**倚靠頭枕、車窗、頸枕時仍有側向接觸**。與側睡的差異：
- 壓力量級低很多
- **接觸位置不固定**，隨倚靠物與姿勢而異
- 持續時間短

**U 型頸枕（travel pillow）需特別注意**：接觸區正是耳後與頭側，**對掛耳式（ear-hook）的耳後主體有直接影響**。

### 下顎張開

頭部前傾時口部常微張，**耳道變形問題與正睡相同**（見 1A.2）。坐睡雖時間短，但密封失效會立即影響隔音效果，而交通環境噪音正是需要隔音的場合。

### 環境與情境約束

| 約束 | 說明 |
|---|---|
| **環境感知** | 須聽得到廣播、不可坐過站。**完全隔絕在此情境是缺點而非優點** |
| 噪音性質 | 交通噪音以**低頻為主**，與安靜臥室的需求完全不同 |
| 外觀 | 公開場合可見，外觀重要性大幅上升 |
| 穿脫與收納 | 使用頻繁，非一日一次 |
| 指示燈 | 白天環境，Part 8 的暗室亮度約束大幅緩解 |

### ⚠️ 1A.4.1 坐睡必須再分三個子情境

**先前把「辦公室午睡」與「搭車」合為一個情境，是過度概化。** 三者在外觀規範、時長與情境安全上差異顯著，且**足以翻轉形態評分**（眼罩式即為一例）。

| | **B1 辦公室午睡** | **B2 短程通勤**（捷運／公車） | **B3 長途交通**（飛機／高鐵／客運） |
|---|---|---|---|
| 時長 | 15–30 分鐘 | 10–40 分鐘 | 1–8 小時 |
| **外觀規範** | **最嚴**——同事在場，趴睡本身已顯眼 | 中 | **最寬**——閉眼睡覺是常態 |
| **遮光需求** | 高（室內燈全開） | 中 | **高**（機艙燈、車窗日照） |
| **情境安全** | 低（不會坐過站） | **最高**——**須看站，不可錯過** | 低（有廣播與空服提醒） |
| 倚靠方式 | 趴桌／後仰 | 頭枕／車窗 | 頭枕／頸枕 |
| **眼罩可接受度** | **低** | 中低 | **完全正常**——航空公司主動提供 |

**遮光是坐睡特有的需求。** 夜間臥睡的光線問題是「不要有光」（Part 8 的指示燈約束）；**白天坐睡反過來是「環境光太多」**。

→ **眼罩式在 B3 同時解決遮光與音訊，這是它在該子情境的獨有優勢**，非劣勢。

### 坐睡設計判準

- [ ] 頭前傾 45°、側倒 45° 時是否仍固位不脫落？
- [ ] 是否保留環境感知（可聽見廣播）？
- [ ] U 型頸枕接觸耳後時是否造成壓迫？
- [ ] 公開場合外觀是否可接受？
- [ ] 隔音是否針對低頻交通噪音而非高頻設計？

---

## 1A.5 各形態族 × 三姿勢

| 形態族 | 正睡 | 側睡 | B1 辦公室 | B2 通勤 | B3 長途交通 |
|---|---|---|---|---|---|
| 入耳式（in-ear） | **中**（下顎張開易失密封） | 中 | 中 | 中（**須留環境感知看站**） | 佳 |
| **掛耳式（ear-hook）** | 佳 | **高風險**（耳後躺壓於乳突骨） | **佳 ★** | **佳 ★** | **佳 ★** |
| 扁平耳罩 | 中 | 中高 | 中低（顯眼） | 中 | 佳 |
| **頭帶／眼罩式** | **佳** | **佳 ★** | **低**（社交） | 中低（**遮眼看不到站**） | **佳 ★★**（**遮光＋音訊一次解決，航空常態**） |
| 骨傳導 | 佳（不涉耳道密封） | 中 | 佳（開放耳道，環境感知佳） | **佳 ★**（聽得到廣播） | 中 |

**排序在姿勢與子情境間都會翻轉。沒有通用最佳解。**

**眼罩式是最典型的例子**：側睡最佳 → 辦公室最差 → **長途交通又回到最佳**。原因是它的評分同時受三個互不相關的因素驅動——機械壓迫（側睡有利）、社交規範（辦公室不利）、遮光需求（白天有利）。**用單一分數表達會失真。**

> **先前版本將坐睡評為「眼罩式實用性低」，係將辦公室規範概化至全部坐睡情境，並漏計白天遮光的功能優勢。已於 2026-08-24 更正。**

---

## 1A.6 綜合：哪個姿勢綁定哪個參數

若產品須同時服務多種姿勢，**取約束的聯集**——每個參數由對它最嚴苛的那個姿勢決定：

| 設計參數 | 由哪個姿勢綁定 | 理由 |
|---|---|---|
| **凸出高度／幾何包絡** | **側睡** | 唯一有枕頭壓迫的姿勢 |
| **固位強度** | **坐睡** | 唯一有頭部前傾側倒的姿勢 |
| **耳道貼合寬容度** | **正睡**（坐睡次之） | 下顎張開最常發生於仰躺 |
| **長時間靜態受壓耐受** | **側睡** | 壓力最高且時間最長 |
| **環境感知／不可完全隔絕** | **坐睡** | 唯一有情境安全需求 |
| **外觀** | **坐睡** | 唯一在公開場合使用 |
| **指示燈亮度** | 正睡／側睡 | 暗室環境 |
| **低頻隔音** | **坐睡** | 交通噪音以低頻為主 |

> **關鍵推論**：三種姿勢**各自綁定不同參數，幾乎沒有重疊**。
> 這代表若要全部服務，**不能只針對最嚴苛的一種姿勢設計就以為涵蓋其他**——每個姿勢都會單獨綁死至少一個參數。
> 反之，**若能限定姿勢，可鬆綁的約束相當可觀**：例如只做坐睡，凸出高度與暗室指示燈兩項整組消失。【推論】

---

## 1A.7 缺口

| 缺口 | 說明 | 阻塞程度 |
|---|---|---|
| 成人各姿勢的**分佈比例** | **仍未取得可核驗數值。** 來源① 僅給趨勢（俯臥消失、老年偏好右側）。來源④ 的摘要亦不含百分比。<br>**線索**：網路檢索層級的來源將「仰臥 34.4±22.8%／側臥 61.8±22.6％／俯臥 3.9±8.7%」歸於來源④，但 Wiley 全文為 403，**本團隊未能對照原文核實，故不採用此組數字**。有期刊訂閱者可快速查證。 | 中。影響各姿勢的權重分配 |
| 側睡凸出高度上限 | 見 Part 4.2，只能實測 | **高**（僅側睡） |
| 下顎張開的**變形量分布** | 來源② 為 30 人但未取得數值表；來源③ 僅 n=1 | 中。影響貼合寬容度的量化 |
| 坐睡固位的量化門檻 | 「頭前傾幾度不脫落」無現成標準，須自訂並實測 | 中 |

---

## 來源

① De Koninck, J., Lorrain, D., Gagnon, P. **Sleep positions and position shifts in five age groups: an ontogenetic picture.** *Sleep*, 1992, 15(2): 143–149. DOI: [10.1093/sleep/15.2.143](https://doi.org/10.1093/sleep/15.2.143)
　類型：學術論文。**摘要已核。** 五年齡層各 10 人，樣本小。

② Darkner, S., Larsen, R., Paulsen, R.R. **Analysis of deformation of the human ear and canal caused by mandibular movement.** *MICCAI*, 2007, 10: 801–808. DOI: [10.1007/978-3-540-75759-7_97](https://doi.org/10.1007/978-3-540-75759-7_97)
　類型：學術論文。**摘要已透過 Europe PMC API 核實。** 30 對耳印模／30 名受試者（9 女 21 男）。**全部受試者於耳屏與耳道皆有顯著變形。** 數值表未取得。

③ Oliveira, R.J., Hammer, B., Stillman, A., Holm, J., Jons, C., Margolis, R.H. **A look at ear canal changes with jaw motion.** *Ear and Hearing*, 1992, 13: 464–466. DOI: [10.1097/00003446-199212000-00013](https://doi.org/10.1097/00003446-199212000-00013)
　類型：學術論文。**摘要已核。** **n=1 個案研究**，矽膠印模＋MRI，前後向約 25% 變化。單一受試者，不可外推為母體數值。

④ Rayward, L., Ho, S.W.K., Green, D., Little, J.P. **Sleep disruption and sleep position: Increased wake frequency in supine predicts lateral position preference.** *Journal of Sleep Research*, 2025, 34(1): e14325. DOI: [10.1111/jsr.14325](https://doi.org/10.1111/jsr.14325)
　類型：學術論文。**摘要已透過 Europe PMC API 核實。** 41 名中高齡成人，兩夜居家多導睡眠圖（相隔約兩週），統一使用硬式泡棉床墊。
　**僅引用摘要所載之質性結論**（部分個體對仰臥耐受度低並以側臥代償）。**姿勢分布百分比不在摘要中，Wiley 全文 403 無法取得，故未引用任何百分比數值。**
