showmin/ear_3d_model_survey/cn/07-wearing-pressure-comfort.md

# Part 7 — 佩戴壓力與舒適

狀態：初稿 ｜ 最後更新 2026-08-21

> 🌐 日本語版：[jp/07-wearing-pressure-comfort.md](../jp/07-wearing-pressure-comfort.md)

> **用語規範**：耳部與醫學名詞中文在前、英文於括號內。

---

> ⛔ **範圍裁定（2026-08-25）：第一階段只服務夜間長時間睡眠（整夜臥睡）。坐睡（辦公室午睡、交通工具）已移出。**
> 本章與坐睡／情境 B 相關的段落**保留但不適用於第一階段**——保留是為了讓「考慮後排除」與「未曾考慮」可以區分，未來擴充情境時可直接取用。
> **引用本章任何形態評分或約束時，必須確認該結論是否綁定坐睡。** 坐睡移出會翻轉部分形態的排序（掛耳式、頭帶眼罩式）。

## 7.0 ⚠️ 本節無法以現有工具模擬驗證

必須先講清楚，且這句話不放附註：

**本團隊無法模擬耳塞（eartip）壓在耳部軟組織上的實際接觸壓力。** 原因有二，且兩者互相加乘：

1. **缺求解器**：無超彈性（hyperelastic）材料模型，無接觸（contact）非線性求解器。矽膠在大應變下的行為不能用線彈性近似。
2. **缺輸入參數**：即使補上求解器，耳部軟組織的材料參數本團隊沒有可核驗來源。輸入是猜的，輸出就不可信。

補其中一項沒有意義——缺的那一半補不上，先補的那一半就沒有價值。

**因此本節給的是設計原則與風險分級，不是模擬驗證過的數值門檻。佩戴壓力最終必須以實體樣機試戴驗證。**

## 7.0b ⚠️ 也不能用「量耳朵」預測舒適度

7.0 講的是「模擬不出來」。這裡是更前面的一層：**即使有精確的耳部尺寸，也預測不了舒適度。**

| 發現 | 內容 | 來源等級 |
|---|---|---|
| 耳部尺寸 vs 主觀舒適／貼合評分 | 耳部對稱性、性別、耳甲長度、耳甲腔寬度的相關性**皆不顯著或很弱** | 【文獻】⑤ |
| 什麼才顯著 | **使用情境**與**產品尺寸** | 【文獻】⑤ |
| **靜態 vs 動態** | **動態情境下使用者偏好較大的產品尺寸** | 【文獻】⑤ |

**統計限制**：n=30。**「未達顯著」在此樣本量下是弱證據，不等於證明無關聯。** 應讀作「尺寸的預測力不足以在 30 人中顯現」。

### ★ 動態／靜態偏好差異對睡眠產品是一個真實的張力

睡眠同時包含兩種狀態，而且**兩者的最佳尺寸方向相反**：

| 狀態 | 佔比 | 需求 | 偏好尺寸 |
|---|---|---|---|
| **靜態**（維持同一姿勢） | **主導**——65–80 歲可超過 30 分鐘不變位（Part 1A.3） | 低持續壓迫 | **較小／較軟** |
| **動態**（翻身、坐睡點頭） | 次要但關鍵 | 固位不脫落 | **較大**（來源⑤） |

→ **睡眠情境以靜態為主，故舒適度應向「較小」傾斜；固位則靠幾何形狀與接觸面設計解決，而非靠加大尺寸。**【推論】
→ 這與 Part 3 的結論一致：固位改用耳輪／對耳輪承擔，而非靠尺寸撐緊。

## 7.1 壓力上限

| 條目 | 數值／門檻 | 來源等級 | 來源出處 | 備註 |
|---|---|---|---|---|
| 耳甲（concha）六個量測點中最敏感部位 | **耳屏（tragus）** | 【文獻】① | 學術論文，80 名受試者 | 見 Part 3.3 |
| 壓力不適閾值（pressure discomfort threshold, PDT）絕對數值 | **待核** | 【待核】 | 全文付費牆，僅取得摘要 | 取得後本節可從相對排序升級為可判定數值門檻 |
| 性別（sex）對 PDT 影響 | **無顯著影響** → 壓力門檻男女共用單一數值 | 【文獻】① | 同上 | 與尺寸類不同，見 Part 3.3 |
| 長時間靜態受壓的可承受值 | **待核** | 【待核】 | — | PDT 量的是短時間施壓的不適閾值，**不等於整夜持續受壓的可承受值**。見 7.2 |

### ⚠️ PDT 不能直接當整夜佩戴的門檻

這是本節最容易被誤用的地方。PDT 實驗量的是短時間施壓造成不適的閾值。睡眠耳機面對的是**持續 6–9 小時、且可能超過 30 分鐘完全不變位**的靜態受壓（見 Part 1.2）。

長時間受壓的可承受值**必然低於**短時間 PDT，但低多少沒有可核驗數據。**不可直接把 PDT 當設計上限使用。**【推論】

## 7.2 壓力分佈原則

| 條目 | 內容 | 來源等級 | 備註 |
|---|---|---|---|
| 面接觸優於點接觸 | 相同總支撐力下，接觸面積越大則局部壓力越低 | 【慣例】 | 基礎力學。壓力＝力／面積 |
| 避開敏感點 | 承壓結構避開耳屏（tragus）與外耳道（EAM）後下壁 | 【文獻】① ② | 見 Part 3.1 |
| 固位改走耳輪 | 固位力優先由耳輪（helix）、對耳輪（antihelix）承擔 | 【推論】 | 市售耳機常用耳屏固位，但耳屏是實測最敏感區。整夜佩戴應改變此慣例 |
| 右耳加重驗證 | 老年使用者明顯偏好右側臥，右耳累積壓迫較高 | 【推論】基於【文獻】③ | 見 Part 1.3 |
| 避免銳邊與硬稜 | 接觸面圓角化，避免應力集中 | 【慣例】 | — |

## 7.3 熱與濕氣

| 條目 | 內容 | 來源等級 | 備註 |
|---|---|---|---|
| 密閉腔體累積體溫與濕氣 | 現象成立 | 【慣例】 | 整夜佩戴放大此問題；棉被覆蓋頭部時更嚴重 |
| 材料層面的熱導率與透氣數據 | 見 Part 6 F 段 | 【文獻】 | 該處數據來自保溫與寢具產業，非耳機專用，僅供數量級參考 |
| 體感可接受的溫升與濕度門檻 | **待核** | 【待核】 | 無可核驗數據 |

## 7.4 驗證方式（本節唯一可靠的路徑）

既然模擬不可行，本節的驗證完全依賴實體測試。建議最小方案：

| 測試 | 方法 | 產出 |
|---|---|---|
| 長時間佩戴試戴 | 受試者實際整夜佩戴，記錄不適發生時間與部位 | 實際可承受時長，非推估 |
| **右側臥加重測試** | 依 Part 1.3，右側臥為主要受壓情境 | 最嚴苛條件下的表現 |
| 接觸壓力量測 | 薄膜壓力感測器貼於接觸面，量測實際界面壓力 | 可與 PDT 比對，補上 7.1 缺的數值 |
| 不同硬度試片比對 | 相同幾何、不同 Shore 硬度，量測界面壓力 | 補上 Part 6 D 段缺的硬度—壓力對應關係 |

**這四項做完，7.1 與 Part 6 D 段的【待核】就能改成【實測】。** 在那之前本節不填數值門檻。

### 7.4.0 ★ 業界做法：不量幾何，量結果

**主流廠商驗證貼合的方式不是量耳朵，是用裝置自己的麥克風測密封。兩家獨立實作，做法不同。**

| 廠商 | 功能名稱 | 協定 | 輸出 |
|---|---|---|---|
| **Apple** | Ear Tip Fit Test（AirPods Pro 1／2）→ **Acoustic Seal Test**（Pro 3） | 播放測試音、內建麥克風分析回授，偵測聲音洩漏 | **通過／不通過**——判定當前配戴的耳塞是否密封 |
| **Sony** | **判斷最佳耳塞**（Sony Headphones Connect App） | 使用者選 2 種以上尺寸（S／M／L），**逐一換上、逐一量測氣密性**，須於安靜環境、量測時不可移動 | **比較排序**——直接告訴你哪個尺寸最貼合 |

【市場商品統計】⑥⑦

> **★ 兩者的差異對本專案有意義。**
> Apple 是**通過／不通過**：回答「這個耳塞行不行」。
> Sony 是**比較式**：回答「哪個尺寸最好」——這正是使用者實際需要的答案，也正是量耳朵想解決卻解決不了的問題（見 7.0b）。
> **若要實作，Sony 的比較式協定更貼近需求**；代價是使用者必須實際更換每個尺寸，UX 成本較高。【推論】

**這對本專案的意義是一條設計建議，不只是驗證方法：**

> **若產品具備麥克風，應內建密封自測功能，並建議採比較式協定（逐一量測各尺寸後排序）。**
> 理由：①它測的是**結果**（實際密封狀況）而非**代理變數**（耳朵尺寸）——見 7.0b，尺寸預測不了貼合；②使用者可自行判定該用哪個耳塞尺寸，不需量測；③密封狀態會隨下顎張閉與姿勢改變（Part 1A），一次性量測本來就無法涵蓋，能隨時重測才實用。

**量測條件**：Sony 要求安靜環境且量測時不可移動。**若實作，須在 UI 上明確要求相同條件**，否則環境噪音與體動會污染結果。

**適用範圍**：僅適用於**密封式入耳**。非密封形態沒有可測的密封面。

> **睡眠情境的延伸考量**：上述協定皆為**清醒、靜止、口閉合**狀態下的一次性量測。而本產品的實際使用狀態是**睡眠中、姿勢改變、下顎鬆弛張開**（Part 1A.2）。**通過密封測試不保證整夜維持密封。** 這個落差目前無資料可量化，僅標示存在。【推論】

**驗證順序建議**：密封自測（若有）→ 7.4.1 三項機械貼合快篩 → 7.4 儀器量測。**由結果測到代理，不是反過來。**【推論】

### 7.4.1 三個低成本的快篩測試

上表四項需要儀器。以下三項只需要受試者本人，**適合在做正式量測前先篩掉明顯不合的方案**。

| 測試 | 做法 | 判定 |
|---|---|---|
| **甩頭測試** | 快速左右搖頭、上下點頭 | 耳機應紋絲不動。有位移＝尺寸偏小或**角度不對** |
| **咀嚼／張口測試** | 張合嘴巴、模擬說話 | **若耳屏（tragus）出現尖銳痛感 → 尺寸過大，立即降一號。這不是適應期問題，是結構不合** |
| **15 分鐘法則** | 戴著走動 15 分鐘 | 真正的舒適是「忘記它的存在」。**任何持續性壓迫感都是錯誤尺寸的訊號，不是需要適應** |

來源等級：【市場商品統計】④——單一產品的消費者選購指南，非人體測量研究、無方法學描述。**作為測試方法採用，不作為數值依據。**

**三點補充：**

1. **甩頭測試對應坐睡的固位判準**（見 [Part 1A.4](01a-posture-analysis.md)）。它比「頭前傾 45°」更容易操作，可作為快篩；正式驗證仍應涵蓋前傾與側倒。

2. **★ 咀嚼測試獨立印證了 Part 1A 的下顎張開效應。** 本指引從 Darkner et al. (2007) 與 Oliveira et al. (1992) 推導出「驗證必須涵蓋口張開狀態」；**一份消費者選購指南從實務經驗獨立走到同一個結論，且指明痛點在耳屏**——與 Part 3 認定耳屏為壓力最敏感區一致。三條互相獨立的線索指向同一件事。

3. **「持續性壓迫感不是適應期」可直接作為驗收準則。** 本節先前只有「必須實體試戴」的原則，缺可判定門檻，此句補上這個缺口。

---

## 來源

① Yuan, X., Wang, Z., Feng, F., Bu, Y., Fan, Z., Liu, H., Li, P., Zhang, L., Li, X., Hu, Z. **Measurement of pressure discomfort threshold in auricular concha for in-ear wearables design.** *Applied Ergonomics*, 2023, 113: 104078. DOI: [10.1016/j.apergo.2023.104078](https://doi.org/10.1016/j.apergo.2023.104078)
　類型：學術論文。**摘要已核；全文付費牆，數值表未取得。**

② Butt, M.F., Albusoda, A., Farmer, A.D., Aziz, Q. **The anatomical basis for transcutaneous auricular vagus nerve stimulation.** *Journal of Anatomy*. DOI: [10.1111/joa.13122](https://doi.org/10.1111/joa.13122) ｜ 開放全文：<https://pmc.ncbi.nlm.nih.gov/articles/PMC7083568/>
　類型：學術論文。**已實際開啟並讀取內文確認。**

③ De Koninck, J., Lorrain, D., Gagnon, P. **Sleep positions and position shifts in five age groups: an ontogenetic picture.** *Sleep*, 1992, 15(2): 143–149. DOI: [10.1093/sleep/15.2.143](https://doi.org/10.1093/sleep/15.2.143)
　類型：學術論文。**摘要已核。** 每年齡層僅 10 人，樣本小。

④ Taobao 選購指南：Soundcore Liberty 3 Pro 耳翼尺寸測量攻略。<https://world.taobao.com/lang/zh-tw/shopping-guide/2009964077014581248.htm>
　類型：**市場商品統計（消費者選購指南）**。單一產品導向，**無方法學描述、無引用來源**，且該頁自承「沒有絕對的官方對應表」「基於人體工學常識的估算，並非廠商的絕對技術規格」。
　**本指引僅採用其測試方法與定性觀察，不採用其任何 mm 數值作為解剖依據**（該頁的「耳甲腔垂直高度」是從耳屏內側邊緣到耳甲底部的斜線，非自碗緣平面的垂直深度，與 Part 2.4 的 CD 不可比）。原文由需求方於 2026-08-24 提供。

⑤ Fu, F., Luximon, Y. **Comfort and fit perception based on 3D anthropometry for ear-related product design.** *Applied Ergonomics*, 2022, 100: 103640. DOI: [10.1016/j.apergo.2021.103640](https://doi.org/10.1016/j.apergo.2021.103640)
　類型：學術論文。**摘要已透過 Europe PMC API 核實。** n=30（15 男 15 女）。

⑥ Apple Ear Tip Fit Test（AirPods Pro 1／2）／Acoustic Seal Test（AirPods Pro 3）。Apple 官方支援文件與媒體報導。
　類型：**市場商品統計**。機制（播放測試音、內建麥克風分析、偵測洩漏）已由多個來源一致描述並經搜尋核實。**未取得 Apple 官方技術白皮書，判定門檻與演算法不明。** 本指引僅引用「業界以密封量測取代幾何量測」此一做法，不引用任何判定數值。

⑦ Sony「判斷最佳耳塞」功能（Sony Headphones Connect App，WF-1000XM 系列）。Sony 官方支援文章編號 00262839 與官方說明指南。
　類型：**市場商品統計**。協定（選 2 種以上尺寸、逐一換上量測氣密性、安靜環境不可移動、輸出最佳尺寸）經 Sony 官方說明指南內容核實。
　註：需求方提供之台灣站連結（sony.com.tw）本團隊存取為 403；同編號文章之香港站與官方 helpguide 內容可取得並一致。**判定門檻與演算法未公開。**
