showmin/ear_3d_model_survey/jp/01-use-scenario.md

# Part 1 — 使用シーンの定義

> **本章に設計規則は含まれない。** ここで定義するのは**前提**——製品がどの状況で使われ、利用者がどの状態にあるか。以降のすべての規則の数値はこの前提の上に成り立っており、前提が変われば数値を計算し直す必要がある。
> **実際の設計規則を見たい場合は [GUIDELINE.ja.md](../GUIDELINE.ja.md) を読むこと。**

ステータス：初稿 ｜ 最終更新 2026-08-21

> 🌐 中文版：[cn/01-use-scenario.md](../cn/01-use-scenario.md)
> **用語規範**：耳の部位名と医学用語は日本語を先に、英語を括弧内に記す。

---

> ⛔ **範囲の裁定（2026-08-25）：第一段階は夜間の長時間睡眠（一晩の臥位睡眠）のみを対象とする。座位睡眠（オフィスの仮眠・交通機関）は除外。**
> 本章のうち座位睡眠／シーン B に関する箇所は**残すが第一段階には適用しない**——残すのは「検討して外した」と「検討しなかった」を区別できるようにするためであり、将来シーンを拡張する際はそのまま使える。
> **本章の形態評価や制約を引用する際は、その結論が座位に紐づいていないか必ず確認すること。** 座位の除外により一部の形態（イヤーフック型、ヘッドバンド／アイマスク型）の順位は反転する。

> 📄 **3 つの睡眠姿勢（仰向け／横向き／座位）の個別分析は [付篇 1A](01a-posture-analysis.md) を参照。** 本章はシーンを定義し、付篇 1A が姿勢ごとに制約と設計判定基準を分解する。

## 1.0 2 つの使用シーン

需求方が 2026-08-21 に**座位睡眠**シーンを追加した。両者の制約は大きく異なり、**同一の判定基準を共用してはならない**。

| | **シーン A：一晩中の臥位睡眠** | **シーン B：座位睡眠** |
|---|---|---|
| 場面 | 寝室、一晩中 | オフィスでの仮眠、公共交通、長距離移動 |
| 装着時間 | 6–9 時間 | **20 分–3 時間** |
| 横向き寝の圧迫 | **支配的制約** | **成立しない**（枕による圧迫がない） |
| 支配的制約 | 横向き寝の突出高さ | **保持の安定性** |

> 📄 **シーン B はさらに 3 つのサブシーンに分ける必要がある**（B1 オフィス仮眠／B2 短距離通勤／B3 長距離交通）。3 者は外観規範・遮光要求・状況安全において、**形態の評価を反転させる**ほどの差がある。[Part 1A.4.1](01a-posture-analysis.md) 参照。

> ⏳ **要確認**：本製品は A、B、あるいは両方を対象とするか？ 3 つの答えでガイドラインの内容は大きく異なる——
> ①**B のみ** → 横向き寝の制約が丸ごと外れ、形態の順位を書き直す
> ②**A＋B** → 両制約の**和集合**を満たす必要があり、横向き寝が依然として拘束条件かつより厳しい
> ③**同シリーズ 2 製品** → 2 つの仕様を分けて記述する

### 1.0.1 シーン B の制約——「制約が少ない」のではなく「別の制約に入れ替わる」

| 側面 | シーン A（臥位） | シーン B（座位） | 変化 |
|---|---|---|---|
| **保持** | 臥位、重力方向が安定 | **居眠り時に頭が前傾・側方へ倒れ、脱落しうる** | **より厳しい** |
| 圧迫 | 全体重が枕を介してかかる | ヘッドレスト・車窓・ネックピローによる側方接触はあるが、圧力ははるかに低く位置も一定しない。**低いがゼロではない** | 大幅に緩和 |
| 静的圧迫の持続時間 | 30 分以上動かないことがある | 装着時間自体が短い | 緩和 |
| 外観 | 自分にしか見えない | **公共の場で見られる** | **より厳しい** |
| 環境騒音 | 静かな寝室 | **交通騒音、低周波が主体** | 要求の性質が異なる |
| 状況安全 | なし | **アナウンスが聞こえる必要があり、降車駅を逃してはならない。完全遮断はむしろ欠点** | **新規制約** |
| 着脱頻度 | 1 日 1 回 | 頻繁。着けやすさ・仕舞いやすさが重要 | **新規制約** |
| インジケータ | 暗所、重要な制約（Part 8） | 日中環境、問題はほぼ消える | 大幅に緩和 |

**ネックピロー（travel pillow）には特に注意**：U 字型ネックピローが接触するのはまさに耳後部と頭部側面であり、イヤーフック型（ear-hook）に直接影響する。

## 1.1 装着シーン（シーン A を基準とする。シーン B との差異は 1.0.1 参照）

| 項目 | 仮定 | 証拠等級 | 備考 |
|---|---|---|---|
| 装着時間 | **一晩中（約 6–9 時間）連続装着** | 【仮定】 | 需求方の確認待ち。「入眠後に外す」に変われば圧力と耐久の要求を大幅に緩和できる |
| 使用姿勢 | ベッドに横たわり、頭部が枕に接触 | 【仮定】 | — |
| 環境 | 室内の寝室。掛け布団が頭頸部を覆う可能性あり | 【仮定】 | 放熱と湿気の蓄積に影響 |
| 利用者の状態 | **無意識**——睡眠中は装着位置を能動的に調整できず、不快にも反応できない | 【推論】 | **これが睡眠用イヤホンと一般イヤホンの最も根本的な違い**。1.4 参照 |

## 1.2 睡眠姿勢と寝返り（実証データあり）

出典① は実験室での睡眠ポリグラフ（polysomnography）研究。5 つの年齢層に各 10 名、連続数夜の撮影記録。

### 寝返り頻度は加齢とともに有意に低下する

| 年齢層 | 姿勢変換回数／時 | 証拠等級 |
|---|---|---|
| 3–5 歳 | 4.4 | 【文献】① |
| 8–12 歳 | 4.7 | 【文献】① |
| **18–24 歳** | **3.6** | 【文献】① |
| **35–45 歳** | **2.7** | 【文献】① |
| **65–80 歳** | **2.1** | 【文献】① |

同時に出典① は、加齢に伴い**姿勢の維持時間が延び**、**30 分以上まったく動かない時間帯の数が増える**ことも報告している。

### 姿勢の分布は加齢とともに変化する

| 発見 | 内容 | 証拠等級 |
|---|---|---|
| 小児 | うつ伏せ（prone）、仰向け（supine）、横向き（lateral）がほぼ等しい比率 | 【文献】① |
| 成人化の傾向 | **うつ伏せ姿勢が徐々に消失する** | 【文献】① |
| 高齢 | **右向き寝（right-side position）を明確に好む** | 【文献】① |
| 成人の各姿勢の正確な比率 | **要確認** | 【要確認】検証可能な数値を未取得 |

## 1.3 上記データが設計に与える 3 つの直接的影響

**① 対象顧客層の年齢が高い → 静的圧迫の時間がより長い。**
睡眠補助製品の利用者は通常年齢が高い。65–80 歳の寝返り頻度はわずか 2.1 回／時で若年成人の約 6 割にとどまり、30 分以上まったく動かない時間帯も増える。**これこそが褥瘡や圧迫不快の典型的な荷重条件である**——ピーク圧力が大きいのではなく、中程度の圧力が長く続くことが問題となる。

→ 設計の判定基準は「長時間の静的接触圧」であるべきで、「瞬間の耐圧」ではない。【推論】

**② 高齢者は右向き寝を好む → 右耳の累積圧迫が左耳より有意に高い。**
→ 装着試験は「横向き寝」だけでなく、**特に右側臥位を重点化すべき**。長時間耐性試験は右耳を主サンプルとする。【推論】
→ 将来的に左右非対称設計を検討する場合、これが実証的裏付けのある唯一の非対称理由となる。（注：出典② は角度系の耳寸法がもともと左右非対称であると指摘しており、併せて考慮しうる。）

**③ 成人のうつ伏せ寝は稀 → うつ伏せ向けの最適化は不要。**
設計リソースは横向きと仰向けに集中すべきである。【推論】

### 証拠の限界
出典① は 1992 年の研究であり、**各年齢層わずか 10 名**（男 5 名・女 5 名）と小標本である。傾向の方向は信頼度が高い（複数指標が一致し単調変化を示す）が、絶対値を精密な設計パラメータとして扱うべきではない。年代も古く、寝具や生活様式は変化している。

## 1.4 睡眠用イヤホンと一般イヤホンの本質的な違い

本節が存在する理由。設計者が一般的な TWS イヤホンの規範をそのまま持ち込むと、以下のすべてで誤る：

| 側面 | 一般イヤホン | 睡眠用イヤホン |
|---|---|---|
| 利用者が不快に反応できるか | できる。いつでも調整・取り外し可能 | **できない。睡眠中は無意識** |
| 荷重の型 | 短時間、中断可能 | **長時間の静的圧迫。最長 30 分以上動かないことがある** |
| 外側からの圧迫 | なし | **枕が継続的に加圧**（Part 4 の横向き寝境界を参照） |
| 許容される突出高さ | 緩い | **極めて厳格。製品の生死を分ける** |
| インジケータ | 問題なし | **暗所で睡眠を妨げうる**（Part 8 参照） |
| 咳嗽反射のリスク | 短時間接触、リスク低 | **一晩中の接触でリスクが拡大**（Part 3.2 参照） |
| 装着時間 | 数時間 | 6–9 時間連続 |

## 1.5 枕との接触（未取得）

| 欠落 | 説明 | 阻害度 |
|---|---|---|
| 枕の材質と沈み込み深さ | 枕の種類（低反発、羽毛、ラテックス）で沈み込み特性が大きく異なり、Part 4 の横向き寝境界を直接決める | **高** |
| 耳介（auricle）の圧迫変形量 | 横向き寝では耳介自体が変形し、動的な間隙に影響する | 中 |

いずれも実測が必要。Part 4.2 の推奨測定方法を参照。

---

## 出典

① De Koninck, J., Lorrain, D., Gagnon, P. **Sleep positions and position shifts in five age groups: an ontogenetic picture.** *Sleep*, 1992, 15(2): 143–149. DOI: [10.1093/sleep/15.2.143](https://doi.org/10.1093/sleep/15.2.143)
　種別：学術論文。**要旨を Europe PMC API で取得し照合済み。** 方法：睡眠ポリグラフ＋8 秒ごと 1 コマの撮影記録、5 年齢層各 10 名。

② Fu, F., Luximon, Y. **A systematic review on ear anthropometry and its industrial design applications.** *Human Factors and Ergonomics in Manufacturing & Service Industries*, 2020, 30: 176–194. DOI: [10.1002/hfm.20832](https://doi.org/10.1002/hfm.20832)
　種別：学術論文。**原文をダウンロードし読解のうえ確認済み。**
