showmin/ear_3d_model_survey/jp/01a-posture-analysis.md

# 付篇 1A — 睡眠姿勢別分析：仰向け／横向き／座位

ステータス：初稿 ｜ 最終更新 2026-08-22
需求方の 2026-08-22 指示により、3 つの睡眠姿勢を個別に分析する。

> 🌐 中文版：[cn/01a-posture-analysis.md](../cn/01a-posture-analysis.md)
> **用語規範**：耳の部位名と医学用語は日本語を先に、英語を括弧内に記す。

---

> ⛔ **範囲の裁定（2026-08-25）：第一段階は夜間の長時間睡眠（一晩の臥位睡眠）のみを対象とする。座位睡眠（オフィスの仮眠・交通機関）は除外。**
> 本章のうち座位睡眠／シーン B に関する箇所は**残すが第一段階には適用しない**——残すのは「検討して外した」と「検討しなかった」を区別できるようにするためであり、将来シーンを拡張する際はそのまま使える。
> **本章の形態評価や制約を引用する際は、その結論が座位に紐づいていないか必ず確認すること。** 座位の除外により一部の形態（イヤーフック型、ヘッドバンド／アイマスク型）の順位は反転する。

## 1A.0 なぜ姿勢を分けて論じる必要があるか

**3 つの姿勢の「支配的制約」はまったく異なり、しかも同一事象の程度差ではない。**

| 姿勢 | 支配的制約 | この 1 点だけを見て他を無視した場合 |
|---|---|---|
| **仰向け寝（supine）** | **外耳道の変形**（顎の開口） | 密閉不良、音漏れ、低域の喪失 |
| **横向き寝（lateral）** | **突出高さ／伝達圧** | 痛くて一晩装着できず、製品として成立しない |
| **座位睡眠（seated）** | **保持の安定性** | 居眠り中に脱落・紛失 |

→ **「睡眠向けに設計する」と言いながら姿勢を指定しないのは、制約を指定していないのと同じである。** 横向き寝で完璧な設計が座位で落ちることもあり、座位で優れた設計が横向きで痛むこともある。

**うつ伏せ（prone）は対象外**：出典① はうつ伏せの比率が加齢とともに**徐々に消失**し成人では稀であると示している。本製品の顧客層は年齢が高い。対象顧客に若年層を含める場合は別途評価が必要。

### 姿勢の好み自体が不快によって駆動されている

出典④ は中高年成人 41 名に 2 夜の在宅睡眠ポリグラフを実施し、**一部の個体は仰向けへの耐性が低く**（仰向け時の覚醒指数が相対的に高い）、**横向きの比率を増やして代償している**と結論している。

→ 本プロジェクトへの意味：**姿勢の好みはランダムな分布ではなく、一部の人は仰向けが不快だから横向きに移っている。** この層は横向きの比率が高く、そして横向きこそイヤホンにとって最も過酷な姿勢である。**平均的な姿勢分布だけを見て設計すると、横向き寝利用者の比重を過小評価する。**【推論】

---

## 1A.1 3 姿勢クイックリファレンス

| 側面 | 仰向け（supine） | 横向き（lateral） | 座位（seated） |
|---|---|---|---|
| **支配的制約** | 外耳道の変形 | **突出高さ／伝達圧** | **保持** |
| 耳への直接圧迫 | 低。耳介は荷重を受けない | **最大。** 全体重が枕を介してかかる | 低いが一定しない（ヘッドレスト／車窓／ネックピロー） |
| 圧迫部位 | 枕が沈み込んだときの耳介側面 | 耳甲介腔、耳珠。イヤーフック型では乳様突起部 | 寄りかかる対象により変動し予測不能 |
| **保持の難度** | **最低。** 重力はほぼ外耳道軸に垂直 | 低。臥位で安定 | **最高。** 頭部の前傾・側方への傾き |
| **顎の開口** | **頻繁**（仰臥時に下顎が弛緩し落ちる） | 少ない | **頻繁**（頭部前傾時に口が薄く開く） |
| 装着時間 | 6–9 時間 | 6–9 時間 | **20 分–3 時間** |
| 静的圧迫の持続 | 長いが圧力は低い | **長くかつ圧力が高い**（30 分以上動かないことがある） | 短い |
| 環境騒音 | 静かな寝室 | 静かな寝室 | **交通騒音、低周波が主体** |
| 外観要求 | 低 | 低 | **高（公共の場）** |
| 環境音把握の必要性 | なし | なし | **必須**（アナウンス、到着駅） |
| インジケータの制約 | **重要**（暗所） | **重要**（暗所） | 低（日中） |

---

## 1A.2 仰向け寝（supine）

### 圧迫の状況

耳介は直接荷重を受けず、頭部重量は後頭骨（occiput）が担う。**ただし接触ゼロという意味ではない**：

- 枕が柔らかいか高い場合、頭部が沈み込み、**枕面が側方から耳介に接触する**
- 沈み込みが深いと、枕の縁が**耳介（auricle）を前方へ折り曲げる**ことがある
- 圧力の桁は横向き寝よりはるかに低いが、接触位置が横向きとは異なる（耳甲介腔ではなく耳介外縁・耳後部）

### ★ 仰向け寝に固有の問題：顎の開口による外耳道の変形

**仰臥時、下顎（mandible）は弛緩して落ちやすく、口がわずかに開く。** 顎関節（temporomandibular joint, TMJ）は外耳道（external acoustic meatus）の前壁に密接しており、下顎頭（mandibular condyle）が前下方へ移動すると周囲の軟組織と線維軟骨が引かれ、**外耳道が特定の領域で拡張または虚脱する**。

| 証拠 | 内容 | 証拠等級 |
|---|---|---|
| 被験者 30 名（女 9・男 21）の耳型比較 | **全被験者において耳珠（tragus）と外耳道の双方に有意な変形**。形状のばらつきが変形のばらつきの約 50% を説明。変形量と性別に関連あり | 【文献】② |
| 単一被験者のシリコーン印象＋MRI | 顎の位置により外耳道が**前後方向（anterior/posterior）に約 25% 変化**。上下方向の変化は極小 | 【文献】③（n=1、症例研究） |

**設計上の意味：**

1. **密閉型カナルは仰向け寝で密閉が失われるリスクがある。** 入眠時は閉口、入眠後に下顎が弛緩して開口 → 外耳道の幾何が変化 → イヤーチップの密閉が緩みうる。**低域とパッシブ遮音が真っ先に影響を受ける**（Part 5 参照）。
2. **変形は外耳道の軟骨部と耳珠に集中する**——そして耳珠は Part 3 が認定した**最も圧迫に敏感な領域**である。**同一部位が最も敏感でありかつ顎の動きで変形する**：耳珠を保持支点とする設計はこの 2 つの問題を同時に負う。
3. 個人差が大きく（出典② は変形量が形状のばらつきと相関すると指摘）、**単一の補正量で全員をカバーすることはできない**。

> ⚠️ **測定上の実務的含意**：今後、耳型を採取するか装着検証を行う際は、**閉口と開口の 2 状態でそれぞれ実施すること**。1 状態のみでは必要なフィット許容幅を系統的に過小評価する。

### その他の考慮事項

- **いびき**：仰向けはいびきと閉塞性睡眠時無呼吸がより重くなる姿勢である【慣例。当チームは具体的な文献を未検証】。製品にいびきマスキング機能を含むなら、仰向けが主要な使用場面となる。
- **保持は最も緩い**：外耳道の軸はおおむね側上方を向き、重力が装置を直接外へ引き出さない。3 姿勢の中で保持要求が最も低い。

### 仰向け寝の設計判定基準

- [ ] イヤーチップは外耳道の前後方向の変形を許容しつつ密閉を保てるか？
- [ ] 装着検証は**開口**状態を含んでいるか？
- [ ] 耳珠を主たる保持支点にすることを避けているか？
- [ ] 枕が沈み込んだとき、耳介外縁の接触領域に硬い稜や鋭利なエッジがないか？

---

## 1A.3 横向き寝（lateral）

**本プロジェクトは横向き寝について最も詳細な分析を行っている。[Part 4.2](04-max-design-envelope.md) を参照。ここでは要約のみ。**

### 中核的制約

**伝達圧**——枕が装置を介して耳に押し込む実際の接触圧。突出高さは最も実用的な代理指標だが物理量そのものではない（枕の順応性、突起形状、シェル剛性の影響も受ける）。

**判定基準は形態ごとに異なる**（Part 4.2.1 参照）：カナル型は耳介外縁に対する突出高さを測り、イヤーフック型は頭部側面最外縁の厚さ、乳様突起部への圧力、耳介が折れ曲がるか、フックがレバーになっていないかを測る。

### 横向き寝に固有の事実

| 事実 | 内容 | 証拠等級 |
|---|---|---|
| **高齢者は右側臥位を明確に好む** | 加齢に伴い右側臥位への選好が顕著になる | 【文献】① |
| 寝返り頻度は加齢とともに低下 | 18–24 歳 3.6 回/時 → 65–80 歳 **2.1 回/時**。30 分以上まったく動かない時間帯が増加 | 【文献】① |

→ **右耳の累積圧迫が左耳より高い**ため、装着試験は右側臥位を重点化すべき。
→ 顧客層の年齢が高い → **長時間の静的圧迫こそが真の荷重条件**であり、瞬間的なピーク圧ではない。

### ⛔ 最大の欠落

**横向き寝の突出高さ上限には公開データがなく、実測するほかない。** メーカーは一切公表せず、フラッシュ（flush）はマーケティング用語で測定上の定義を持たない。Part 4.2 参照。

---

## 1A.4 座位睡眠（seated）

### 中核的制約：保持

**居眠り時に頭部が前傾または側方へ倒れ**、装置は横向き寝にはない脱落力を受ける。しかも紛失の影響が大きい——オフィスや交通機関では見つけにくい。

**これが横向き寝の突出高さに代わり、座位睡眠の第一関門となる。**

### 圧迫：低いが予測不能

枕による圧迫はないが、**ヘッドレスト・車窓・ネックピローに寄りかかる際に側方接触は生じる**。横向き寝との違い：
- 圧力の桁がはるかに低い
- **接触位置が一定しない**。寄りかかる対象と姿勢により変動する
- 持続時間が短い

**U 字型ネックピロー（travel pillow）には特に注意**：接触領域がまさに耳後部と頭部側面であり、**イヤーフック型（ear-hook）の耳後部本体に直接影響する**。

### 顎の開口

頭部が前傾すると口がわずかに開くことが多く、**外耳道の変形問題は仰向け寝と同じである**（1A.2 参照）。座位は時間こそ短いが、密閉不良は遮音効果に即座に影響し、しかも交通環境の騒音はまさに遮音が必要な場面である。

### 環境・状況の制約

| 制約 | 説明 |
|---|---|
| **環境音の把握** | アナウンスが聞こえる必要があり、降車駅を逃してはならない。**完全遮断はこのシーンでは利点ではなく欠点** |
| 騒音の性質 | 交通騒音は**低周波が主体**であり、静かな寝室での要求とはまったく異なる |
| 外観 | 公共の場で見られるため、外観の重要性が大幅に上がる |
| 着脱と収納 | 使用が頻繁であり、1 日 1 回ではない |
| インジケータ | 日中環境のため、Part 8 の暗所輝度制約は大幅に緩和される |

### ⚠️ 1A.4.1 座位睡眠はさらに 3 つのサブシーンに分ける必要がある

**以前「オフィス仮眠」と「乗車中」を 1 つのシーンにまとめていたのは過度の一般化であった。** 3 者は外観規範・時間・状況安全において顕著に異なり、**形態の評価を反転させるに足る**（アイマスク型がその一例）。

| | **B1 オフィス仮眠** | **B2 短距離通勤**（地下鉄／バス） | **B3 長距離交通**（航空機／高速鉄道／高速バス） |
|---|---|---|---|
| 時間 | 15–30 分 | 10–40 分 | 1–8 時間 |
| **外観規範** | **最も厳しい**——同僚がいる。机に伏せること自体が目立つ | 中 | **最も緩い**——目を閉じて眠るのが普通 |
| **遮光要求** | 高（室内灯が全点灯） | 中 | **高**（機内灯、車窓からの日射） |
| **状況安全** | 低（乗り過ごしはない） | **最高**——**降車駅を見る必要があり、逃してはならない** | 低（アナウンスと客室乗務員の案内あり） |
| 寄りかかり方 | 机に伏せる／後ろに反る | ヘッドレスト／車窓 | ヘッドレスト／ネックピロー |
| **アイマスクの受容度** | **低** | 中〜低 | **完全に普通**——航空会社が自ら配布する |

**遮光は座位睡眠に固有の要求である。** 夜間の臥位睡眠における光の問題は「光をなくすこと」（Part 8 のインジケータ制約）だが、**日中の座位睡眠では逆に「環境光が多すぎる」ことが問題となる**。

→ **アイマスク型は B3 において遮光と音響を同時に解決する。これは当該サブシーンにおける固有の優位性**であり、欠点ではない。

### 座位睡眠の設計判定基準

- [ ] 頭部前傾 45°、側方傾斜 45° でも保持され脱落しないか？
- [ ] 環境音の把握（アナウンスが聞こえること）を確保しているか？
- [ ] U 字型ネックピローが耳後部に接触したとき圧迫を生じないか？
- [ ] 公共の場での外観は受容可能か？
- [ ] 遮音は高周波ではなく低周波の交通騒音を対象に設計されているか？

---

## 1A.5 各形態 × 3 姿勢

| 形態 | 仰向け | 横向き | B1 オフィス | B2 通勤 | B3 長距離交通 |
|---|---|---|---|---|---|
| カナル型（in-ear） | **中**（顎の開口で密閉が失われやすい） | 中 | 中 | 中（**環境音把握が必要、降車駅**） | 良 |
| **イヤーフック型（ear-hook）** | 良 | **高リスク**（耳後部が乳様突起の骨上で圧迫） | **良 ★** | **良 ★** | **良 ★** |
| フラットオーバーイヤー型 | 中 | 中〜高 | 中〜低（目立つ） | 中 | 良 |
| **ヘッドバンド／アイマスク型** | **良** | **良 ★** | **低**（社会的受容） | 中〜低（**目が覆われ降車駅が見えない**） | **良 ★★**（**遮光＋音響を一度に解決。航空機では常態**） |
| 骨伝導 | 良（外耳道の密閉に関与しない） | 中 | 良（外耳道が開放され環境音把握が良好） | **良 ★**（アナウンスが聞こえる） | 中 |

**順位は姿勢間でもサブシーン間でも反転する。万能な最適解は存在しない。**

**アイマスク型が最も典型的な例である**：横向き寝で最良 → オフィスで最悪 → **長距離交通で再び最良**。その評価が互いに無関係な 3 つの要因——機械的圧迫（横向きに有利）、社会的規範（オフィスに不利）、遮光要求（日中に有利）——に同時に駆動されるためである。**単一のスコアで表現すると実態を歪める。**

> **以前の版は座位睡眠を「アイマスク型は実用性が低い」と評価していた。これはオフィスの規範を座位睡眠全体へ一般化し、かつ日中の遮光という機能上の優位性を計上していなかったためである。2026-08-24 に訂正済み。**

---

## 1A.6 統合：どの姿勢がどのパラメータを拘束するか

複数の姿勢に同時対応する必要がある場合、**制約の和集合を取る**——各パラメータは、それに対して最も厳しい姿勢によって決まる：

| 設計パラメータ | どの姿勢が拘束するか | 理由 |
|---|---|---|
| **突出高さ／幾何エンベロープ** | **横向き** | 枕による圧迫がある唯一の姿勢 |
| **保持力** | **座位** | 頭部の前傾・側方傾斜がある唯一の姿勢 |
| **外耳道フィットの許容幅** | **仰向け**（座位が次ぐ） | 顎の開口は仰臥で最も頻繁に生じる |
| **長時間の静的圧迫への耐性** | **横向き** | 圧力が最も高くかつ時間が最も長い |
| **環境音把握／完全遮断の禁止** | **座位** | 状況安全の要求がある唯一の姿勢 |
| **外観** | **座位** | 公共の場で使用される唯一の姿勢 |
| **インジケータ輝度** | 仰向け／横向き | 暗所環境 |
| **低周波遮音** | **座位** | 交通騒音は低周波が主体 |

> **重要な推論**：3 つの姿勢は**それぞれ異なるパラメータを拘束し、ほとんど重複しない**。
> つまりすべてに対応するなら、**最も厳しい 1 つの姿勢だけを狙って設計すれば他もカバーできる、とはならない**——各姿勢が少なくとも 1 つのパラメータを単独で拘束する。
> 逆に、**姿勢を限定できれば緩められる制約はかなり大きい**：例えば座位のみとすれば、突出高さと暗所インジケータの 2 項目が丸ごと消える。【推論】

---

## 1A.7 欠落

| 欠落 | 説明 | 阻害度 |
|---|---|---|
| 成人の各姿勢の**分布比率** | **依然として検証可能な数値を未取得。** 出典① は傾向のみ（うつ伏せの消失、高齢者の右向き選好）。出典④ の要旨にも百分率はない。<br>**手がかり**：検索レベルの情報源が「仰向け 34.4±22.8%／横向き 61.8±22.6%／うつ伏せ 3.9±8.7%」を出典④ に帰しているが、Wiley の全文は 403 であり、**当チームは原文と照合できていないため、この数値群は採用しない**。雑誌購読があれば短時間で確認できる。 | 中。各姿勢への重み配分に影響 |
| 横向き寝の突出高さ上限 | Part 4.2 参照。実測するほかない | **高**（横向きのみ） |
| 顎の開口による**変形量の分布** | 出典② は 30 名だが数値表は未取得。出典③ は n=1 のみ | 中。フィット許容幅の定量化に影響 |
| 座位睡眠における保持の定量的しきい値 | 「頭部前傾何度で脱落しないか」に既存の標準はなく、自ら定めて実測する必要がある | 中 |

---

## 出典

① De Koninck, J., Lorrain, D., Gagnon, P. **Sleep positions and position shifts in five age groups: an ontogenetic picture.** *Sleep*, 1992, 15(2): 143–149. DOI: [10.1093/sleep/15.2.143](https://doi.org/10.1093/sleep/15.2.143)
　種別：学術論文。**要旨を確認済み。** 5 年齢層各 10 名、小標本。

② Darkner, S., Larsen, R., Paulsen, R.R. **Analysis of deformation of the human ear and canal caused by mandibular movement.** *MICCAI*, 2007, 10: 801–808. DOI: [10.1007/978-3-540-75759-7_97](https://doi.org/10.1007/978-3-540-75759-7_97)
　種別：学術論文。**要旨を Europe PMC API で確認済み。** 耳型 30 対／被験者 30 名（女 9・男 21）。**全被験者において耳珠と外耳道に有意な変形。** 数値表は未取得。

③ Oliveira, R.J., Hammer, B., Stillman, A., Holm, J., Jons, C., Margolis, R.H. **A look at ear canal changes with jaw motion.** *Ear and Hearing*, 1992, 13: 464–466. DOI: [10.1097/00003446-199212000-00013](https://doi.org/10.1097/00003446-199212000-00013)
　種別：学術論文。**要旨を確認済み。** **n=1 の症例研究**。シリコーン印象＋MRI、前後方向に約 25% の変化。単一被験者であり母集団の数値へ外挿してはならない。

④ Rayward, L., Ho, S.W.K., Green, D., Little, J.P. **Sleep disruption and sleep position: Increased wake frequency in supine predicts lateral position preference.** *Journal of Sleep Research*, 2025, 34(1): e14325. DOI: [10.1111/jsr.14325](https://doi.org/10.1111/jsr.14325)
　種別：学術論文。**要旨を Europe PMC API で確認済み。** 中高年成人 41 名、2 夜の在宅睡眠ポリグラフ（約 2 週間の間隔）、硬質フォームマットレスに統一。
　**要旨に記載された定性的結論のみを引用**（一部の個体は仰臥への耐性が低く横向きで代償する）。**姿勢分布の百分率は要旨に含まれず、Wiley 全文は 403 で取得できないため、百分率は一切引用していない。**
