showmin/ear_3d_model_survey/jp/07-wearing-pressure-comfort.md

# Part 7 — 装着圧と快適性

ステータス：初稿 ｜ 最終更新 2026-08-21

> 🌐 中文版：[cn/07-wearing-pressure-comfort.md](../cn/07-wearing-pressure-comfort.md)
> **用語規範**：耳の部位名と医学用語は日本語を先に、英語を括弧内に記す。

---

> ⛔ **範囲の裁定（2026-08-25）：第一段階は夜間の長時間睡眠（一晩の臥位睡眠）のみを対象とする。座位睡眠（オフィスの仮眠・交通機関）は除外。**
> 本章のうち座位睡眠／シーン B に関する箇所は**残すが第一段階には適用しない**——残すのは「検討して外した」と「検討しなかった」を区別できるようにするためであり、将来シーンを拡張する際はそのまま使える。
> **本章の形態評価や制約を引用する際は、その結論が座位に紐づいていないか必ず確認すること。** 座位の除外により一部の形態（イヤーフック型、ヘッドバンド／アイマスク型）の順位は反転する。

## 7.0 ⚠️ 本節は現有ツールではシミュレーション検証できない

先に明確にしておく。そしてこの一文は注記に置かない：

**当チームはイヤーチップ（eartip）が耳の軟組織を圧迫する実際の接触圧をシミュレーションできない。** 理由は 2 つあり、しかも互いに増幅し合う：

1. **ソルバがない**：超弾性（hyperelastic）材料モデルがなく、接触（contact）非線形ソルバもない。大ひずみ下のシリコーンの挙動を線形弾性で近似することはできない。
2. **入力パラメータがない**：仮にソルバを揃えても、耳の軟組織の材料パラメータに当チームは検証可能な出典を持たない。入力が当て推量なら出力も信用できない。

片方だけ補っても意味がない——足りない半分が埋まらない限り、先に補った半分に価値は生じない。

**したがって本節が示すのは設計原則とリスク等級であり、シミュレーションで検証された数値しきい値ではない。装着圧は最終的に実機装着試験で検証しなければならない。**

## 7.0b ⚠️「耳を測る」ことでも快適性は予測できない

7.0 が述べたのは「シミュレーションできない」ことである。ここではさらに一段手前の話をする：**正確な耳の寸法があっても、快適性は予測できない。**

| 発見 | 内容 | 証拠等級 |
|---|---|---|
| 耳の寸法 vs 主観的な快適性／フィット評点 | 耳の左右対称性、性別、耳甲介長、耳甲介腔幅との相関は**いずれも有意でないか非常に弱い** | 【文献】⑤ |
| 何が有意なのか | **使用状況**と**製品サイズ** | 【文献】⑤ |
| **静的 vs 動的** | **動的な状況では利用者はより大きい製品サイズを好む** | 【文献】⑤ |

**統計上の限界**：n=30。**この標本規模での「有意に達しない」は弱い証拠であり、無関係であることの証明ではない。**「寸法の予測力は 30 名で顕在化するほど強くない」と読むべきである。

### ★ 動的／静的の選好差は睡眠製品にとって現実の緊張関係である

睡眠は 2 つの状態を同時に含み、しかも**両者の最適サイズは逆方向を向く**：

| 状態 | 比重 | 要求 | 好まれるサイズ |
|---|---|---|---|
| **静的**（同一姿勢を維持） | **支配的**——65–80 歳では 30 分以上動かないことがある（Part 1A.3） | 持続圧迫が低いこと | **より小さく／より柔らかい** |
| **動的**（寝返り、座位でのうなずき） | 副次的だが決定的 | 保持され脱落しないこと | **より大きい**（出典⑤） |

→ **睡眠は静的が主体であるため、快適性は「より小さい」側へ寄せるべきである。保持は幾何形状と接触面の設計で解決し、サイズを大きくして解決しない。**【推論】
→ これは Part 3 の結論と一致する：保持は耳輪／対耳輪に担わせ、サイズで突っ張って支えるのではない。

## 7.1 圧力上限

| 項目 | 数値／しきい値 | 証拠等級 | 出典 | 備考 |
|---|---|---|---|---|
| 耳甲介（concha）6 測定点のうち最も敏感な部位 | **耳珠（tragus）** | 【文献】① | 学術論文、被験者 80 名 | Part 3.3 参照 |
| 圧迫不快閾値（pressure discomfort threshold, PDT）の絶対値 | **要確認** | 【要確認】 | 全文は有料の壁の内側。要旨のみ取得 | 取得できれば本節を相対順位から判定可能な数値しきい値へ格上げできる |
| 性別（sex）の PDT への影響 | **有意差なし** → 圧力しきい値は男女共通の単一値とする | 【文献】① | 同上 | 寸法系とは異なる。Part 3.3 参照 |
| 長時間の静的圧迫における耐容値 | **要確認** | 【要確認】 | — | PDT が測るのは短時間加圧の不快閾値であり、**一晩中持続する圧迫の耐容値とは等価でない**。7.2 参照 |

### ⚠️ PDT をそのまま一晩装着のしきい値にしてはならない

本節で最も誤用されやすい箇所である。PDT の実験が測るのは短時間の加圧による不快の閾値である。睡眠用イヤホンが直面するのは**6–9 時間持続し、かつ 30 分以上まったく動かないことがある**静的圧迫である（Part 1.2 参照）。

長時間圧迫の耐容値は短時間 PDT より**必然的に低い**が、どれだけ低いかを示す検証可能なデータはない。**PDT をそのまま設計上限として用いてはならない。**【推論】

## 7.2 圧力分布の原則

| 項目 | 内容 | 証拠等級 | 備考 |
|---|---|---|---|
| 面接触は点接触に優る | 同じ支持力なら接触面積が大きいほど局所圧力は低くなる | 【慣例】 | 基礎力学。圧力＝力／面積 |
| 敏感点を避ける | 荷重構造は耳珠（tragus）と外耳道（EAM）後下壁を避ける | 【文献】① ② | Part 3.1 参照 |
| 保持は耳輪へ移す | 保持力は耳輪（helix）、対耳輪（antihelix）に優先的に担わせる | 【推論】 | 市販イヤホンは耳珠で保持することが多いが、耳珠は実測で最も敏感な領域である。一晩中の装着ではこの慣例を変えるべきである |
| 右耳を重点検証 | 高齢利用者は右側臥位を明確に好み、右耳の累積圧迫が高い | 【推論】【文献】③ に基づく | Part 1.3 参照 |
| 鋭利なエッジと硬い稜を避ける | 接触面を丸め、応力集中を避ける | 【慣例】 | — |

## 7.3 熱と湿気

| 項目 | 内容 | 証拠等級 | 備考 |
|---|---|---|---|
| 密閉空間に体温と湿気が蓄積する | 現象として成立 | 【慣例】 | 一晩装着はこの問題を拡大する。掛け布団が頭部を覆うとさらに悪化する |
| 材料レベルの熱伝導率・通気データ | Part 6 F 節参照 | 【文献】 | 同節のデータは断熱材および寝具業界のものでイヤホン専用ではなく、桁の参考にとどまる |
| 体感として許容できる温度上昇と湿度のしきい値 | **要確認** | 【要確認】 | 検証可能なデータがない |

## 7.4 検証方法（本節で唯一信頼できる経路）

シミュレーションが不可能である以上、本節の検証は完全に実機試験に依存する。推奨する最小構成：

| 試験 | 方法 | 産出 |
|---|---|---|
| 長時間装着試験 | 被験者が実際に一晩装着し、不快の発生時刻と部位を記録する | 実際の耐容時間。推定ではない |
| **右側臥位の重点試験** | Part 1.3 に従い、右側臥位を主たる圧迫状況とする | 最も過酷な条件下での挙動 |
| 接触圧測定 | 薄膜圧力センサを接触面に貼り、実際の界面圧を測定する | PDT と照合でき、7.1 に欠けている数値を補える |
| 硬度違いのテストピース比較 | 同一幾何で Shore 硬度のみを変え、界面圧を測定する | Part 6 D 節に欠けている硬度—圧力の対応関係を補える |

**この 4 項目を実施すれば、7.1 と Part 6 D 節の【要確認】を【実測】へ変更できる。** それまで本節は数値しきい値を記入しない。

### 7.4.0 ★ 業界の方法：幾何を測らず、結果を測る

**主流メーカーがフィットを検証する方法は耳を測ることではなく、機器自身のマイクで密閉度を測ることである。2 社の独立した実装があり、やり方が異なる。**

| メーカー | 機能名 | プロトコル | 出力 |
|---|---|---|---|
| **Apple** | Ear Tip Fit Test（AirPods Pro 1／2）→ **Acoustic Seal Test**（Pro 3） | テスト音を再生し、内蔵マイクで反射音を解析して音漏れを検出する | **合否判定**——現在装着中のチップが密閉しているかを判定 |
| **Sony** | **最適なイヤーピースの判定**（Sony Headphones Connect アプリ） | 利用者が 2 種類以上のサイズ（S／M／L）を選び、**順に装着して 1 つずつ気密性を測定する**。静かな環境で、測定中は動かないこと | **比較順位**——どのサイズが最も合うかを直接示す |

【市場製品統計】⑥⑦

> **★ 両者の違いは本プロジェクトにとって意味がある。**
> Apple は**合否判定**であり、「このチップで良いか」に答える。
> Sony は**比較方式**であり、「どのサイズが最良か」に答える——これこそが利用者が実際に必要とし、かつ耳を測っても解決できない問いである（7.0b 参照）。
> **実装するなら Sony 式の比較プロトコルのほうが要求に近い。** 代償として利用者が各サイズを実際に付け替える必要があり、UX コストが高い。【推論】

**これは本プロジェクトにとって検証方法にとどまらず、設計上の推奨事項でもある：**

> **製品にマイクがあるなら、密閉度の自己テスト機能を内蔵し、比較方式のプロトコル（各サイズを順に測定して順位付けする）を推奨する。**
> 理由：①測るのが**結果**（実際の密閉状態）であって**代理変数**（耳の寸法）ではない——7.0b のとおり寸法ではフィットを予測できない。②利用者が自分でどのチップサイズを使うべきか判定でき、測定が不要になる。③密閉状態は顎の開閉と姿勢で変化する（Part 1A）ため、1 回限りの測定では元来カバーできず、随時再測定できることが実用上重要である。

**測定条件**：Sony は静かな環境と、測定中に動かないことを要求している。**実装する場合、UI 上で同じ条件を明示的に要求すること。** さもないと環境騒音と体動が結果を汚染する。

**適用範囲**：**密閉型カナルにのみ適用。** 非密閉形態には測定できる密閉面が存在しない。

> **睡眠シーンへの拡張的考察**：上記のプロトコルはいずれも**覚醒・静止・閉口**状態での 1 回限りの測定である。一方、本製品の実際の使用状態は**睡眠中・姿勢変化・下顎の弛緩による開口**である（Part 1A.2）。**密閉テストに合格しても、一晩中密閉が保たれる保証はない。** この乖離を定量化するデータは現時点でなく、存在の明示にとどめる。【推論】

**推奨する検証順序**：密閉自己テスト（あれば）→ 7.4.1 の 3 つの機械的フィット簡易スクリーニング → 7.4 の計測機器による測定。**結果から代理指標へ進むのであって、その逆ではない。**【推論】

### 7.4.1 3 つの低コスト簡易スクリーニング

上表の 4 項目は計測機器を要する。以下の 3 項目は被験者本人だけで実施でき、**本測定の前に明らかに不適合な案を落とすのに適する**。

| 試験 | やり方 | 判定 |
|---|---|---|
| **頭振り試験** | 素早く首を左右に振る・上下に頷く | イヤホンは微動だにしないこと。ずれる＝サイズが小さすぎるか**角度が合っていない** |
| **咀嚼／開口試験** | 口を開閉する、話す真似をする | **耳珠（tragus）に鋭い痛みが出る → サイズが大きすぎる。直ちに 1 段小さくする。これは慣れの問題ではなく構造が合っていない** |
| **15 分ルール** | 装着したまま 15 分歩く | 真の快適さとは「存在を忘れること」である。**持続する圧迫感はすべて誤ったサイズの兆候であり、慣れるべきものではない** |

証拠等級：【市場製品統計】④——単一製品の消費者向け選び方ガイドであり、人体計測研究ではなく方法論の記述もない。**試験方法として採用し、数値の根拠としては用いない。**

**3 点の補足：**

1. **頭振り試験は座位睡眠の保持判定基準に対応する**（[Part 1A.4](01a-posture-analysis.md) 参照）。「頭部前傾 45°」より実施しやすく簡易スクリーニングに使えるが、正式な検証では前傾と側方傾斜を依然としてカバーすべきである。

2. **★ 咀嚼試験は Part 1A の顎開口効果を独立に裏付けている。** 本ガイドラインは Darkner et al. (2007) と Oliveira et al. (1992) から「検証は開口状態を含まなければならない」を導出した。**消費者向けの選び方ガイドが実務経験から独立に同じ結論に到達し、しかも痛みの箇所が耳珠であると明示している**——これは Part 3 が耳珠を最も圧迫に敏感な領域と認定したことと一致する。互いに独立した 3 本の線が同じ一点を指している。

3. **「持続する圧迫感は慣れの問題ではない」はそのまま受入基準として使える。** 本節にはこれまで「実機装着試験が必須」という原則しかなく判定可能なしきい値を欠いていたが、この一文がその欠落を埋める。

---

## 出典

① Yuan, X., Wang, Z., Feng, F., Bu, Y., Fan, Z., Liu, H., Li, P., Zhang, L., Li, X., Hu, Z. **Measurement of pressure discomfort threshold in auricular concha for in-ear wearables design.** *Applied Ergonomics*, 2023, 113: 104078. DOI: [10.1016/j.apergo.2023.104078](https://doi.org/10.1016/j.apergo.2023.104078)
　種別：学術論文。**要旨は確認済み。全文は有料の壁の内側で数値表は未取得。**

② Butt, M.F., Albusoda, A., Farmer, A.D., Aziz, Q. **The anatomical basis for transcutaneous auricular vagus nerve stimulation.** *Journal of Anatomy*. DOI: [10.1111/joa.13122](https://doi.org/10.1111/joa.13122) ｜ オープンアクセス全文：<https://pmc.ncbi.nlm.nih.gov/articles/PMC7083568/>
　種別：学術論文。**実際に全文を開いて本文を確認済み。**

③ De Koninck, J., Lorrain, D., Gagnon, P. **Sleep positions and position shifts in five age groups: an ontogenetic picture.** *Sleep*, 1992, 15(2): 143–149. DOI: [10.1093/sleep/15.2.143](https://doi.org/10.1093/sleep/15.2.143)
　種別：学術論文。**要旨は確認済み。** 各年齢層わずか 10 名、小標本。

④ Taobao 選び方ガイド：Soundcore Liberty 3 Pro イヤーウィングのサイズ測定ガイド。<https://world.taobao.com/lang/zh-tw/shopping-guide/2009964077014581248.htm>
　種別：**市場製品統計（消費者向け選び方ガイド）**。単一製品向けであり、**方法論の記述も引用出典もない**。同ページ自身が「絶対的な公式対応表はない」「人間工学の常識に基づく推定であり、メーカーの絶対的な技術仕様ではない」と認めている。
　**本ガイドラインは同ページの試験方法と定性的観察のみを採用し、いかなる mm 数値も解剖学的根拠としては採用しない**（同ページの「耳甲介腔の垂直高さ」は耳珠内側縁から耳甲介底部への斜線であり、椀の縁の平面からの垂直深さではないため、Part 2.4 の CD とは比較できない）。原文は需求方が 2026-08-24 に提供。

⑤ Fu, F., Luximon, Y. **Comfort and fit perception based on 3D anthropometry for ear-related product design.** *Applied Ergonomics*, 2022, 100: 103640. DOI: [10.1016/j.apergo.2021.103640](https://doi.org/10.1016/j.apergo.2021.103640)
　種別：学術論文。**要旨を Europe PMC API で確認済み。** n=30（男 15・女 15）。

⑥ Apple Ear Tip Fit Test（AirPods Pro 1／2）／Acoustic Seal Test（AirPods Pro 3）。Apple 公式サポート文書およびメディア報道。
　種別：**市場製品統計**。機構（テスト音の再生、内蔵マイクによる解析、漏れの検出）は複数の情報源が一致して記述しており、検索により確認済み。**Apple 公式の技術白書は未取得であり、判定しきい値とアルゴリズムは不明。** 本ガイドラインは「業界が幾何測定を密閉測定で置き換えている」という事実のみを引用し、判定数値は一切引用しない。

⑦ Sony「最適なイヤーピースの判定」機能（Sony Headphones Connect アプリ、WF-1000XM シリーズ）。Sony 公式サポート記事番号 00262839 および公式ヘルプガイド。
　種別：**市場製品統計**。プロトコル（2 種類以上のサイズを選択、順に装着して気密性を測定、静かな環境で動かない、最適サイズを出力）は Sony 公式ヘルプガイドの内容で確認済み。
　注：需求方が提供した台湾サイトのリンク（sony.com.tw）は当方からのアクセスが 403 であったが、同一記事番号の香港サイトおよび公式 helpguide の内容は取得でき、内容は一致している。**判定しきい値とアルゴリズムは非公開。**
