showmin/ear_3d_model_survey/cn/03-sensitive-zones.md

# Part 3 — 耳部敏感區與禁置區

狀態：初稿 ｜ 最後更新 2026-08-21

> 🌐 日本語版：[jp/03-sensitive-zones.md](../jp/03-sensitive-zones.md)

回答需求方的提問：**耳朵哪些部位痛覺神經較敏感，不建議規劃部件。**

> **用語規範**：耳部與醫學名詞一律中文在前、英文於括號內，例如 耳屏（tragus）。首次出現標全稱與縮寫，其後可只用中文。

---

## 3.0 先講這節的證據強度（重要，請先讀）

這節的結論建立在三類互相獨立的證據上，強度不同，**不可混為一談**：

| 證據類型 | 內容 | 強度 | 可推論到什麼 |
|---|---|---|---|
| **神經解剖分佈** | 哪條神經支配哪個部位 | 中。基礎屍體研究樣本極小（見 3.4） | 只能說明「這區神經支配為何」，**不等於痛覺閾值高低** |
| **壓力不適閾值（pressure discomfort threshold, PDT）** | 實測受試者對壓力的耐受 | 較強。80 名受試者 | 直接對應「戴起來會不會痛」 |
| **機械誘發反射（mechanically-evoked reflex）** | 觸碰特定部位引發咳嗽 | 強。臨床觀察，樣本數百人 | 直接對應「碰到會不會有反射反應」 |

**三者必須分開引用。** 神經支配密集不自動等於痛覺敏感；反過來，PDT 高的區域也可能有反射風險。

### ⚠️ 一個必須避免的錯誤推論

耳甲（concha）與耳屏（tragus）是**經皮耳迷走神經刺激（transcutaneous auricular vagus nerve stimulation, taVNS）**的標準刺激靶區，相關文獻顯示刺激該區可產生自律神經（autonomic nervous system）反應，如心率下降。

**但那些研究用的是電刺激（electrical stimulation），不是被動機械壓迫（passive mechanical pressure）。** 不可以從「電刺激耳甲會影響自律神經」推論出「戴耳機壓住耳甲會影響心率」——這是跨越刺激模態的無根據外推。本指引**不作此宣稱**。

反之，**Arnold 咳嗽反射（Arnold's ear-cough reflex）是機械誘發的**（臨床上以觸碰誘發），這一項可以直接用於機械接觸的設計判斷。

---

## 3.1 分區敏感度與部件放置建議

| 部位 | 主要神經支配 | 痛覺／不適證據 | 反射風險 | 可否放置承壓部件 | 來源等級 |
|---|---|---|---|---|---|
| **耳屏（tragus）** | 迷走神經耳支（auricular branch of vagus nerve, ABVN）為主；併有耳顳神經（auriculotemporal nerve）、耳大神經（great auricular nerve） | **六個耳甲量測點中最敏感** | — | **不建議承載固位力**。若必須接觸，壓力應為全機最低 | 【文獻】① ② |
| **耳甲艇（cymba conchae）** | 迷走神經耳支（ABVN） | 未單獨列出排序 | taVNS 主靶區（電刺激，勿外推） | 避免持續集中壓迫；可輕接觸 | 【文獻】① |
| **耳甲腔（cavum conchae）** | 迷走神經耳支（ABVN）、耳顳神經（auriculotemporal nerve）、耳大神經（great auricular nerve）、顏面神經（facial nerve）交通支 | 未單獨列出排序 | — | 可作為支撐面，但須分散壓力 | 【文獻】① |
| **外耳道（external acoustic meatus, EAM）後／下壁** | 迷走神經耳支（ABVN）為主 | — | **Arnold 咳嗽反射誘發區**（見 3.2） | **不建議接觸**。入耳件應避開後下象限 | 【文獻】① |
| **外耳道（EAM）前壁** | 混合：耳顳神經、耳大神經、迷走神經耳支 | — | 反射率較後下壁低 | 相對可接觸 | 【文獻】① |
| **對耳輪（antihelix）／對耳屏（antitragus）** | 耳大神經（great auricular nerve）＋迷走神經耳支（ABVN），重疊多 | — | — | 可作支撐面 | 【文獻】① |
| **耳輪（helix）／舟狀窩（scapha）** | 枕小神經（lesser occipital nerve）、耳大神經為主；迷走神經耳支貢獻極少或不定 | — | 迷走風險最低 | **相對安全區**，適合放置固位結構 | 【文獻】① |
| **耳垂（lobule）** | 耳大神經為主；文獻述「相對不含迷走傳入纖維（vagal afferents）」 | — | 迷走風險最低 | **相對安全區** | 【文獻】① |

**綜合結論（設計用）：**
- **最需避開**：耳屏（tragus，痛覺最敏感）、外耳道後下壁（EAM posteroinferior wall，反射）
- **相對安全**：耳輪（helix）、舟狀窩（scapha）、耳垂（lobule）、對耳輪（antihelix）
- 設計張力：市售耳機常用耳屏作固位支點，但耳屏正是實測最敏感區。**整夜佩戴產品應優先改用耳輪／對耳輪固位。**（本指引推論，標【推論】）

---

## 3.2 Arnold 咳嗽反射（Arnold's ear-cough reflex）— 可量化的機械風險

觸碰外耳道（EAM）特定區域可誘發咳嗽反射，發生率有臨床數字：

| 觸發部位 | 陽性率 | 樣本 | 來源等級 |
|---|---|---|---|
| 外耳道後象限＋下象限 | **4.2%** | 21／500 人 | 【文獻】① |
| 外耳道前象限 | **2.0%** | 10／500 人 | 【文獻】① |
| 外耳道後下側 | **2.1%** | 11／514 人 | 【文獻】① |
| 整體耳—咳反射盛行率 | **1.7–4.2%** | 綜合 | 【文獻】① |

**設計意義**：若入耳件持續接觸外耳道後下壁，可預期約 **2–4% 使用者**會出現咳嗽反應。對助眠產品而言，這不是舒適度扣分，是直接破壞產品目的——夜間咳嗽會中斷睡眠。

---

## 3.3 壓力不適閾值（PDT）

| 條目 | 內容 | 來源等級 |
|---|---|---|
| 耳甲（concha）六點中最敏感部位 | **耳屏（tragus）** | 【文獻】② |
| **性別（sex）** 對 PDT 影響 | **無顯著影響** | 【文獻】② |
| 左右對稱性（symmetry）對 PDT 影響 | 無顯著影響 | 【文獻】② |
| 身體質量指數（body mass index, BMI）對 PDT 影響 | 無顯著影響 | 【文獻】② |
| 六點各自的 PDT 絕對數值（kPa／N） | **待核 — 全文付費牆，僅取得摘要** | 【待核】 |

### ★ 對「人因分男／女」指示的重要修正

需求方指示人因部份分男／女。依現有證據，這個切分**只適用於尺寸，不適用於壓力閾值**：

| 項目 | 是否分男／女 | 依據 |
|---|---|---|
| 耳部**尺寸（dimensions）** | **要分**。多數族群男性耳部大於女性 | 【文獻】③ |
| **壓力不適閾值（PDT）** | **不分**。實測性別無顯著影響 | 【文獻】② |

→ Part 2 尺寸表分男女；本節壓力門檻男女共用單一數值，反而比分開更有依據。

---

## 3.4 本節的證據限制（不得隱去）

1. **神經分佈的底層資料樣本極小。** 常被引用的 Peuker & Filler (2002) 屍體研究（cadaveric study）僅 **7 具屍體／14 耳**。
2. **該研究自身存在表／文矛盾**，由來源① 明確指出：耳屏 ABVN 支配率表列 45%，內文卻寫「耳大神經 45%、耳顳神經 9%、兩者皆有 46%」完全未提 ABVN；耳輪腳（crus of helix）ABVN 支配率表列 20%、內文 0%。
3. **來源① 明言精確的外耳皮節圖（cutaneous map／dermatome map）「不切實際」**：個體間差異大、神經纖維走行中互相交通、皮節邊界不清且重疊。
4. **PDT 絕對數值未取得**，目前只能給相對排序，無法寫成「壓力 ≤ X kPa」這種可判定門檻。
5. 因此本節分區為**風險分級**，不是精確邊界。實際產品仍須實體試戴驗證。

---

## 3.5 待補（可具體行動）

| 缺口 | 取得方式 | 影響 |
|---|---|---|
| PDT 六點絕對數值 | 取得來源② 全文（Applied Ergonomics 期刊訂閱／機構帳號） | 可把本節從相對排序升級為可判定數值門檻 |
| 亞洲族群專屬 PDT | 來源② 作者群為中國山東大學／齊魯工業大學／歌爾聲學，受試族群很可能為中國人，與目標市場相符——**待全文確認受試者國籍** | 若相符，本數據對亞洲市場適用性佳 |

---

## 來源

① Butt, M.F., Albusoda, A., Farmer, A.D., Aziz, Q. **The anatomical basis for transcutaneous auricular vagus nerve stimulation.** *Journal of Anatomy*. DOI: [10.1111/joa.13122](https://doi.org/10.1111/joa.13122) ｜ 開放全文：<https://pmc.ncbi.nlm.nih.gov/articles/PMC7083568/>
　類型：學術論文。**已實際開啟並讀取內文確認。** 註：線上版年份標示 2019、期刊卷期年份標示 2020，引用時建議以 DOI 為準。

② Yuan, X., Wang, Z., Feng, F., Bu, Y., Fan, Z., Liu, H., Li, P., Zhang, L., Li, X., Hu, Z. **Measurement of pressure discomfort threshold in auricular concha for in-ear wearables design.** *Applied Ergonomics*, 2023, 113: 104078. DOI: [10.1016/j.apergo.2023.104078](https://doi.org/10.1016/j.apergo.2023.104078)
　類型：學術論文。**摘要已透過 Europe PMC API 取得並核對；全文為付費牆（Semantic Scholar 標示 openAccess status = CLOSED），未取得數值表。**

③ Fu, F., Luximon, Y. **A systematic review on ear anthropometry and its industrial design applications.** *Human Factors and Ergonomics in Manufacturing & Service Industries*, 2020, 30: 176–194. DOI: [10.1002/hfm.20832](https://doi.org/10.1002/hfm.20832) ｜ 免費全文：<https://ira.lib.polyu.edu.hk/bitstream/10397/89894/1/a0733-n14_1220_hfm.pdf>
　類型：學術論文（系統性回顧，50 篇）。**已下載並讀取原文確認。**
