showmin/ear_3d_model_survey/cn/08-cmf.md

# Part 8 — CMF（Color, Material, Finish）

狀態：初稿 ｜ 最後更新 2026-08-21

> 🌐 日本語版：[jp/08-cmf.md](../jp/08-cmf.md)

> **用語規範**：耳部與醫學名詞中文在前、英文於括號內。

---

## 8.1 ★ 指示燈亮度 — 睡眠產品特有，一般耳機 CMF 規範不會有這條

暗室中的一顆呼吸燈足以破壞睡眠產品的核心價值。而且這件事有紮實的量化生理學依據，不是主觀偏好。

### 證據

來源① 為 PNAS 2019 研究，量測夜間光照對褪黑激素（melatonin）的抑制：

| 條目 | 數值 | 來源等級 |
|---|---|---|
| 群體平均 ED₅₀（造成 50% 褪黑激素抑制的光照度） | **24.60 lux** | 【文獻】① |
| **個體差異範圍** | **最敏感者 6 lux，最不敏感者 350 lux**（跨越一個數量級以上） | 【文獻】① |
| 10 lux 造成的褪黑激素起始延遲 | 約 **22 分鐘** | 【文獻】① |
| 30 lux | 約 **77 分鐘** | 【文獻】① |
| 50 lux | 約 **109 分鐘** | 【文獻】① |

### ⚠️ 這裡有一個關鍵區分，設計者最容易搞錯

上述 lux 值是**角膜照度（corneal illuminance，即眼睛實際接收到的光）**，不是 LED 的發光強度。距離、角度、遮蔽都會大幅改變實際到達眼睛的量。**不可以直接把 LED 規格書的數字拿來跟這些門檻比較。**

由此推導出的重要結論：

| 光源位置 | 對配戴者眼睛的影響 | 設計優先度 |
|---|---|---|
| **耳機本體上的 LED** | 配戴時位於耳內或耳廓（auricle）上，**基本不在配戴者視野內** | 低（對配戴者）。但**對同床者可見**，仍須控制 |
| **充電盒／底座上的 LED** | 通常放在床頭櫃，**正對配戴者視野，距離近** | **最高。這才是真正的風險點** |

**多數設計會花力氣控制耳機本體的燈，卻忽略充電盒的燈——後者才是直接照到眼睛的那個。**【推論】

### 設計條文

| 條目 | 門檻 | 來源等級 | 備註 |
|---|---|---|---|
| 睡眠模式下，充電盒／底座指示燈 | **預設全滅** | 【推論】基於【文獻】① | 最安全的設計是不亮。任何亮度都落在某些人的敏感範圍內 |
| 若功能上必須顯示狀態 | 以**最敏感個體 6 lux** 為設計基準，不可用群體平均 24.6 lux | 【推論】基於【文獻】① | 群體平均會讓約半數敏感使用者受影響 |
| 色溫 | 偏暖色優先，避免藍光與冷白光 | 【慣例】 | 短波長對褪黑激素抑制效率較高為既有共識；**本團隊未核驗到可引用的具體波長門檻數值**，故標【慣例】 |
| 閃爍／呼吸效果 | 睡眠模式下禁用 | 【推論】 | 變化的光比恆定光更容易引起注意 |
| 實際驗證方式 | 於實際使用距離與角度，以照度計量測**到達眼睛位置**的 lux | 【推論】 | 唯一可靠的檢查方式。規格書數字不可替代 |

**證據限制**：來源① 量測的是「傍晚光照對褪黑激素起始的影響」，受試情境與「已入睡後床頭燈光」不完全相同。個體差異達一個數量級以上，任何單一門檻都不適用於所有人——這正是「預設全滅」比「訂一個門檻」更可靠的原因。【推論】

## 8.2 視覺

| 條目 | 內容 | 來源等級 | 備註 |
|---|---|---|---|
| 整體調性 | 低調、非科技感 | 【慣例】 | 睡眠產品置於臥室，屬寢具情境而非 3C 情境 |
| 表面光澤 | 低光澤（matte）優先 | 【慣例】 | 避免反射床頭燈或晨光 |
| 深／淺色的取捨 | 深色顯皮脂痕跡，淺色顯髒污與變黃 | 【慣例】 | 耳部接觸件長期接觸皮脂，兩者皆須考量。中性色與紋理表面可降低顯著度 |

## 8.3 觸感與表面處理

| 條目 | 內容 | 來源等級 | 備註 |
|---|---|---|---|
| 接觸面觸感 | 柔軟、非黏膩、無銳邊 | 【慣例】 | 黏膩感在整夜佩戴與出汗情境下會被放大 |
| 表面處理與清潔的衝突 | 表面處理必須耐受清潔方式 | 【文獻】 | 見 Part 6 E 段：每日 70% 異丙醇（IPA）擦拭會使矽膠表面霧化、變硬或膨脹。**霧面處理若因清潔而變光亮，等於 8.2 的設計失效** |
| 摸黑操作辨識 | 左右耳、正反面需可觸覺辨識 | 【推論】 | 使用者在暗室中配戴，無法依賴視覺。此需求一般耳機較弱、睡眠耳機必要 |

## 8.4 待補

| 缺口 | 說明 |
|---|---|
| 具體波長／色溫門檻 | 短波長抑制效率較高為共識，但未核驗到可引用的具體數值門檻 |
| 亞洲市場的色彩與材質偏好 | 無可核驗的市場調查資料 |

---

## 來源

① Phillips, A.J.K., Vidafar, P., Burns, A.C., McGlashan, E.M., Anderson, C., Rajaratnam, S.M.W., Lockley, S.W., Cain, S.W. **High sensitivity and interindividual variability in the response of the human circadian system to evening light.** *Proceedings of the National Academy of Sciences (PNAS)*, 2019, 116(24): 12019–12024. DOI: [10.1073/pnas.1901824116](https://doi.org/10.1073/pnas.1901824116)
　類型：學術論文。**摘要與關鍵數值已透過 Europe PMC API 取得並核對。**
