showmin/ear_3d_model_survey/jp/03-sensitive-zones.md

# Part 3 — 耳の敏感領域と配置禁止領域

ステータス：初稿 ｜ 最終更新 2026-08-21

需求方の問いへの回答：**耳のどの部位が痛覚に敏感で、部品の配置を推奨しないか。**

> 🌐 中文版：[cn/03-sensitive-zones.md](../cn/03-sensitive-zones.md)
> **用語規範**：耳の部位名と医学用語は日本語を先に、英語を括弧内に記す。例：耳珠（tragus）。初出時に正式名称と略称を示し、以降は日本語のみでよい。

---

## 3.0 まず本節の証拠強度について（重要。先に読むこと）

本節の結論は互いに独立した 3 種類の証拠に基づいており、強度が異なる。**混同してはならない**：

| 証拠の種類 | 内容 | 強度 | 何を推論できるか |
|---|---|---|---|
| **神経解剖学的分布** | どの神経がどの部位を支配するか | 中。基礎となる屍体研究の標本が極めて小さい（3.4 参照） | 「この領域の神経支配は何か」を説明できるのみ。**痛覚閾値の高低とは等価でない** |
| **圧迫不快閾値（pressure discomfort threshold, PDT）** | 被験者の圧迫耐性の実測 | 比較的強い。被験者 80 名 | 「装着して痛むかどうか」に直接対応 |
| **機械的誘発反射（mechanically-evoked reflex）** | 特定部位への接触が咳嗽を誘発する | 強い。臨床観察、標本数百名 | 「触れたときに反射が起きるか」に直接対応 |

**この 3 者は分けて引用しなければならない。** 神経支配が密であることは自動的に痛覚に敏感であることを意味しない。逆に、PDT が高い領域にも反射のリスクがありうる。

### ⚠️ 避けなければならない誤った推論

耳甲介（concha）と耳珠（tragus）は**経皮的耳介迷走神経刺激（transcutaneous auricular vagus nerve stimulation, taVNS）**の標準的な刺激標的領域であり、関連文献は同領域の刺激が自律神経系（autonomic nervous system）の反応（心拍数の低下など）を生じうると示している。

**しかしそれらの研究が用いているのは電気刺激（electrical stimulation）であり、受動的な機械的圧迫（passive mechanical pressure）ではない。**「耳甲介への電気刺激が自律神経に影響する」から「イヤホンで耳甲介を圧迫すると心拍に影響する」を導くことはできない——これは刺激様式をまたぐ根拠のない外挿である。本ガイドラインは**この主張を行わない**。

逆に、**Arnold 咳嗽反射（Arnold's ear-cough reflex）は機械的に誘発される**（臨床的には接触で誘発される）ため、こちらは機械的接触の設計判断に直接用いてよい。

---

## 3.1 領域別の敏感度と部品配置の推奨

| 部位 | 主な神経支配 | 痛覚／不快の証拠 | 反射リスク | 荷重部品を配置してよいか | 証拠等級 |
|---|---|---|---|---|---|
| **耳珠（tragus）** | 迷走神経耳介枝（auricular branch of vagus nerve, ABVN）が主。耳介側頭神経（auriculotemporal nerve）、大耳介神経（great auricular nerve）も関与 | **耳甲介 6 測定点のうち最も敏感** | — | **保持力を負担させることを推奨しない**。接触が避けられない場合、圧力は全機で最低とすること | 【文献】① ② |
| **耳甲介舟（cymba conchae）** | 迷走神経耳介枝（ABVN） | 順位の個別記載なし | taVNS の主標的（電気刺激。外挿しないこと） | 持続的な集中圧迫を避ける。軽い接触は可 | 【文献】① |
| **耳甲介腔（cavum conchae）** | 迷走神経耳介枝（ABVN）、耳介側頭神経、大耳介神経、顔面神経（facial nerve）の交通枝 | 順位の個別記載なし | — | 支持面として使用可。ただし圧力を分散させること | 【文献】① |
| **外耳道（external acoustic meatus, EAM）の後壁／下壁** | 迷走神経耳介枝（ABVN）が主 | — | **Arnold 咳嗽反射の誘発領域**（3.2 参照） | **接触を推奨しない**。カナル部は後下象限を避けること | 【文献】① |
| **外耳道（EAM）の前壁** | 混合：耳介側頭神経、大耳介神経、迷走神経耳介枝 | — | 反射率は後下壁より低い | 相対的に接触可 | 【文献】① |
| **対耳輪（antihelix）／対耳珠（antitragus）** | 大耳介神経＋迷走神経耳介枝。重複が多い | — | — | 支持面として使用可 | 【文献】① |
| **耳輪（helix）／舟状窩（scapha）** | 小後頭神経（lesser occipital nerve）、大耳介神経が主。迷走神経耳介枝の寄与は極めて小さいか不定 | — | 迷走神経リスク最小 | **相対的に安全な領域**。保持構造の配置に適する | 【文献】① |
| **耳垂（lobule）** | 大耳介神経が主。文献は「迷走神経求心線維（vagal afferents）を相対的に含まない」と記述 | — | 迷走神経リスク最小 | **相対的に安全な領域** | 【文献】① |

**総合結論（設計用）：**
- **最も避けるべき**：耳珠（tragus、痛覚が最も敏感）、外耳道の後下壁（EAM posteroinferior wall、反射）
- **相対的に安全**：耳輪（helix）、舟状窩（scapha）、耳垂（lobule）、対耳輪（antihelix）
- 設計上の緊張：市販イヤホンは耳珠を保持支点にすることが多いが、耳珠こそ実測で最も敏感な領域である。**一晩中装着する製品では耳輪／対耳輪による保持へ優先的に切り替えるべきである。**（本ガイドラインの推論。【推論】と表示）

---

## 3.2 Arnold 咳嗽反射（Arnold's ear-cough reflex）— 定量化できる機械的リスク

外耳道（EAM）の特定領域への接触は咳嗽反射を誘発しうる。発生率には臨床的な数値がある：

| 誘発部位 | 陽性率 | 標本 | 証拠等級 |
|---|---|---|---|
| 外耳道の後象限＋下象限 | **4.2%** | 21／500 名 | 【文献】① |
| 外耳道の前象限 | **2.0%** | 10／500 名 | 【文献】① |
| 外耳道の後下側 | **2.1%** | 11／514 名 | 【文献】① |
| 耳—咳反射の全体有病率 | **1.7–4.2%** | 総合 | 【文献】① |

**設計上の意味**：カナル部が外耳道の後下壁に持続的に接触する場合、約 **2–4% の利用者**に咳嗽反応が生じると予想される。睡眠補助製品にとってこれは快適性の減点ではなく、製品目的そのものの破壊である——夜間の咳嗽は睡眠を中断させる。

---

## 3.3 圧迫不快閾値（PDT）

| 項目 | 内容 | 証拠等級 |
|---|---|---|
| 耳甲介（concha）6 点のうち最も敏感な部位 | **耳珠（tragus）** | 【文献】② |
| **性別（sex）** の PDT への影響 | **有意差なし** | 【文献】② |
| 左右対称性（symmetry）の PDT への影響 | 有意差なし | 【文献】② |
| 体格指数（body mass index, BMI）の PDT への影響 | 有意差なし | 【文献】② |
| 6 点それぞれの PDT 絶対値（kPa／N） | **要確認 — 全文は有料の壁の内側。要旨のみ取得** | 【要確認】 |

### ★「人間工学データを男女で分ける」指示への重要な修正

需求方は人間工学部分を男女で分けるよう指示した。現有の証拠によれば、この区分は**寸法にのみ適用され、圧迫閾値には適用されない**：

| 項目 | 男女で分けるか | 根拠 |
|---|---|---|
| 耳の**寸法（dimensions）** | **分ける**。多くの集団で男性の耳は女性より大きい | 【文献】③ |
| **圧迫不快閾値（PDT）** | **分けない**。実測で性別の有意差なし | 【文献】② |

→ Part 2 の寸法表は男女別とする。本節の圧迫しきい値は男女共通の単一値とするほうが、分けるよりむしろ根拠がある。

---

## 3.4 本節の証拠上の限界（隠してはならない）

1. **神経分布の基礎データの標本が極めて小さい。** よく引用される Peuker & Filler (2002) の屍体研究（cadaveric study）は**屍体 7 体／14 耳**にすぎない。
2. **同研究には表と本文の矛盾がある**。出典① が明確に指摘している：耳珠の ABVN 支配率は表では 45% だが、本文では「大耳介神経 45%、耳介側頭神経 9%、両方 46%」と記され ABVN にまったく触れていない。耳輪脚（crus of helix）の ABVN 支配率は表で 20%、本文で 0%。
3. **出典① は、外耳の正確な皮膚分節図（cutaneous map／dermatome map）は「現実的でない」と明言している**：個体差が大きく、神経線維が走行中に相互に交通し、皮膚分節の境界が不明瞭で重複する。
4. **PDT の絶対値は未取得**であり、現時点では相対順位しか示せず、「圧力 ≤ X kPa」のような判定可能なしきい値にはできない。
5. したがって本節の領域区分は**リスクの等級付け**であり、正確な境界ではない。実際の製品では実機装着による検証が依然として必要である。

---

## 3.5 未取得（具体的に行動可能）

| 欠落 | 取得方法 | 影響 |
|---|---|---|
| PDT 6 点の絶対値 | 出典② の全文を取得する（Applied Ergonomics の購読／機関アカウント） | 本節を相対順位から判定可能な数値しきい値へ格上げできる |
| アジア集団固有の PDT | 出典② の著者群は中国の山東大学／斉魯工業大学／GoerTek であり、被験者集団は中国人である可能性が高く対象市場と一致する——**全文で被験者の国籍を確認する必要がある** | 一致すれば、本データのアジア市場への適用性は良好となる |

---

## 出典

① Butt, M.F., Albusoda, A., Farmer, A.D., Aziz, Q. **The anatomical basis for transcutaneous auricular vagus nerve stimulation.** *Journal of Anatomy*. DOI: [10.1111/joa.13122](https://doi.org/10.1111/joa.13122) ｜ オープンアクセス全文：<https://pmc.ncbi.nlm.nih.gov/articles/PMC7083568/>
　種別：学術論文。**実際に全文を開いて本文を確認済み。** 注：オンライン版の年は 2019、雑誌の巻号年は 2020 と表示される。引用時は DOI を基準とすることを推奨。

② Yuan, X., Wang, Z., Feng, F., Bu, Y., Fan, Z., Liu, H., Li, P., Zhang, L., Li, X., Hu, Z. **Measurement of pressure discomfort threshold in auricular concha for in-ear wearables design.** *Applied Ergonomics*, 2023, 113: 104078. DOI: [10.1016/j.apergo.2023.104078](https://doi.org/10.1016/j.apergo.2023.104078)
　種別：学術論文。**要旨を Europe PMC API で取得し照合済み。全文は有料の壁の内側（Semantic Scholar は openAccess status = CLOSED と表示）であり、数値表は未取得。**

③ Fu, F., Luximon, Y. **A systematic review on ear anthropometry and its industrial design applications.** *Human Factors and Ergonomics in Manufacturing & Service Industries*, 2020, 30: 176–194. DOI: [10.1002/hfm.20832](https://doi.org/10.1002/hfm.20832) ｜ 無料全文：<https://ira.lib.polyu.edu.hk/bitstream/10397/89894/1/a0733-n14_1220_hfm.pdf>
　種別：学術論文（系統的レビュー、50 篇）。**ダウンロードして原文を読解のうえ確認済み。**
