showmin/ear_3d_model_survey/jp/08-cmf.md

# Part 8 — CMF（Color, Material, Finish）

ステータス：初稿 ｜ 最終更新 2026-08-21

> 🌐 中文版：[cn/08-cmf.md](../cn/08-cmf.md)
> **用語規範**：耳の部位名と医学用語は日本語を先に、英語を括弧内に記す。

---

## 8.1 ★ インジケータ輝度 — 睡眠製品に固有であり、一般イヤホンの CMF 規範にはない条項

暗所でのブリージングライト 1 個が、睡眠製品の中核的価値を破壊しうる。しかもこれは主観的な好みではなく、定量的な生理学的根拠がある。

### 証拠

出典① は PNAS 2019 の研究で、夜間光によるメラトニン（melatonin）抑制を測定している：

| 項目 | 数値 | 証拠等級 |
|---|---|---|
| 集団平均 ED₅₀（メラトニンを 50% 抑制する照度） | **24.60 lux** | 【文献】① |
| **個人差の範囲** | **最も感受性が高い者で 6 lux、最も低い者で 350 lux**（一桁以上の開き） | 【文献】① |
| 10 lux によるメラトニン分泌開始の遅延 | 約 **22 分** | 【文献】① |
| 30 lux | 約 **77 分** | 【文献】① |
| 50 lux | 約 **109 分** | 【文献】① |

### ⚠️ ここに設計者が最も取り違えやすい重要な区別がある

上記の lux 値は**角膜照度（corneal illuminance、すなわち目が実際に受け取る光）**であり、LED の発光強度ではない。距離・角度・遮蔽により、実際に目へ到達する量は大きく変わる。**LED のスペックシートの数値をこれらのしきい値と直接比較してはならない。**

ここから導かれる重要な結論：

| 光源の位置 | 装着者の目への影響 | 設計上の優先度 |
|---|---|---|
| **イヤホン本体の LED** | 装着時は耳内または耳介（auricle）上にあり、**基本的に装着者の視野に入らない** | 低（装着者に対して）。ただし**同床者からは見える**ため制御は必要 |
| **充電ケース／ドックの LED** | 通常ベッドサイドに置かれ、**装着者の視野を正面から向き、距離も近い** | **最高。これこそが真のリスク箇所である** |

**多くの設計はイヤホン本体の光を抑えることに労力を割く一方、充電ケースの光を見落とす——目を直接照らしているのは後者である。**【推論】

### 設計条項

| 項目 | しきい値 | 証拠等級 | 備考 |
|---|---|---|---|
| スリープモードにおける充電ケース／ドックのインジケータ | **既定で全消灯** | 【推論】【文献】① に基づく | 最も安全な設計は点灯させないことである。いかなる輝度も、誰かの感受性の範囲に入る |
| 機能上どうしても状態表示が必要な場合 | **最も感受性の高い個人の 6 lux** を設計基準とし、集団平均 24.6 lux を用いてはならない | 【推論】【文献】① に基づく | 集団平均を用いると感受性の高い利用者の約半数が影響を受ける |
| 色温度 | 暖色寄りを優先し、青色光と冷白色光を避ける | 【慣例】 | 短波長のメラトニン抑制効率が高いことは既存の共通認識である。ただし**当チームは引用可能な具体的波長しきい値を確認できていない**ため【慣例】と表示する |
| 点滅／ブリージング効果 | スリープモードでは禁止 | 【推論】 | 変化する光は一定の光より注意を引きやすい |
| 実際の検証方法 | 実使用時の距離と角度で、照度計により**目の位置に到達する** lux を測定する | 【推論】 | 唯一信頼できる確認方法である。スペックシートの数値では代替できない |

**証拠の限界**：出典① が測定しているのは「就寝前の夕方の光がメラトニン分泌開始に与える影響」であり、被験環境は「入眠後のベッドサイドの光」とは完全には一致しない。個人差は一桁以上に及び、いかなる単一のしきい値も全員には当てはまらない——これこそが「既定で全消灯」が「しきい値を一つ定める」より信頼できる理由である。【推論】

## 8.2 視覚

| 項目 | 内容 | 証拠等級 | 備考 |
|---|---|---|---|
| 全体のトーン | 控えめで、テック感を出さない | 【慣例】 | 睡眠製品は寝室に置かれ、3C 機器ではなく寝具の文脈に属する |
| 表面光沢 | 低光沢（マット）を優先 | 【慣例】 | ベッドサイドの照明や朝日の反射を避ける |
| 濃色／淡色のトレードオフ | 濃色は皮脂の跡が目立ち、淡色は汚れと黄変が目立つ | 【慣例】 | 耳への接触部品は長期間皮脂に触れるため双方を考慮する必要がある。中性色とテクスチャ表面で目立ちにくくできる |

## 8.3 触感と表面処理

| 項目 | 内容 | 証拠等級 | 備考 |
|---|---|---|---|
| 接触面の触感 | 柔らかく、べたつかず、鋭利なエッジがないこと | 【慣例】 | べたつきは一晩装着と発汗の状況で増幅される |
| 表面処理と洗浄の衝突 | 表面処理は想定する洗浄方法に耐えること | 【文献】 | Part 6 E 節参照：毎日 70% イソプロピルアルコール（IPA）で拭くとシリコーン表面が白化・硬化・膨潤する。**マット処理が洗浄によって光沢化すれば、8.2 の設計は破綻する** |
| 暗所での識別 | 左右耳と表裏を触覚で識別できること | 【推論】 | 利用者は暗所で装着するため視覚に頼れない。この要求は一般イヤホンでは弱いが、睡眠用イヤホンでは必須である |

## 8.4 未取得

| 欠落 | 説明 |
|---|---|
| 具体的な波長／色温度のしきい値 | 短波長の抑制効率が高いことは共通認識だが、引用可能な具体的数値しきい値を確認できていない |
| アジア市場の色彩・素材の嗜好 | 検証可能な市場調査データがない |

---

## 出典

① Phillips, A.J.K., Vidafar, P., Burns, A.C., McGlashan, E.M., Anderson, C., Rajaratnam, S.M.W., Lockley, S.W., Cain, S.W. **High sensitivity and interindividual variability in the response of the human circadian system to evening light.** *Proceedings of the National Academy of Sciences (PNAS)*, 2019, 116(24): 12019–12024. DOI: [10.1073/pnas.1901824116](https://doi.org/10.1073/pnas.1901824116)
　種別：学術論文。**要旨と主要数値を Europe PMC API で取得し照合済み。**
