showmin/ear_3d_model_survey/jp/TERMS.md

# 用語対照表（中文 → 日本語）

本 `jp/` ディレクトリの全文書はこの対照表に従う。**解剖学用語は中国語の漢字をそのまま流用してはならない**——日中で正式名称が異なる語が多い。

## 耳の解剖

| 中文 | 日本語 | English |
|---|---|---|
| 耳廓 | **耳介** | auricle |
| 耳屏 | **耳珠** | tragus |
| 對耳屏 | **対耳珠** | antitragus |
| 耳輪 | 耳輪 | helix |
| 對耳輪 | **対耳輪** | antihelix |
| 耳輪腳 | **耳輪脚** | crus of helix |
| 耳甲 | **耳甲介** | concha |
| 耳甲腔 | **耳甲介腔** | cavum conchae |
| 耳甲艇 | **耳甲介舟** | cymba conchae |
| 舟狀窩 | **舟状窩** | scapha |
| 耳垂 | 耳垂 | lobule |
| 外耳道 | 外耳道 | external acoustic meatus (EAM) |
| 耳屏間切跡 | **珠間切痕** | intertragic notch |
| 耳前切跡 | **前切痕** | incisura anterior auris |
| 乳突區 | **乳様突起部** | mastoid |
| 顳部 | **側頭部** | temple |

## 神経

| 中文 | 日本語 | English |
|---|---|---|
| 迷走神經耳支 | **迷走神経耳介枝** | auricular branch of vagus nerve (ABVN) |
| 耳大神經 | **大耳介神経** | great auricular nerve |
| 耳顳神經 | **耳介側頭神経** | auriculotemporal nerve |
| 枕小神經 | **小後頭神経** | lesser occipital nerve |
| 顏面神經 | 顔面神経 | facial nerve |
| 顳顎關節 | **顎関節** | temporomandibular joint (TMJ) |
| 下顎髁突 | **下顎頭** | mandibular condyle |

## 睡眠姿勢・場面

| 中文 | 日本語 |
|---|---|
| 正睡／仰睡 | **仰向け寝** |
| 側睡 | **横向き寝** |
| 俯臥 | **うつ伏せ寝** |
| 坐睡 | **座位睡眠** |
| 翻身 | **寝返り** |
| 枕頭 | 枕 |
| 頸枕 | **ネックピロー** |

## 製品・設計

| 中文 | 日本語 |
|---|---|
| 佩戴 | **装着** |
| 耳塞 | **イヤーチップ** |
| 耳翼 | **イヤーウィング** |
| 凸出高度 | **突出高さ** |
| 機型 S／M／L | **機種 S／M／L** |
| 耳型分段 I／II／III | **耳型区分 I／II／III** |
| 掛耳式 | **イヤーフック型** |
| 入耳式 | **カナル型** |
| 扁平耳罩 | **フラットオーバーイヤー型** |
| 頭帶／眼罩式 | **ヘッドバンド／アイマスク型** |
| 骨傳導 | **骨伝導** |
| 壓力不適閾值 | **圧迫不快閾値**（PDT） |
| 遮蔽效應 | **オクルージョン効果** |
| 漏氣路徑 | **漏れ経路** |
| 前腔／後腔 | **前気室／後気室** |
| 密封 | **密閉** |
| 可製造性 | **製造可能性** |
| 列印 | **プリント／造形** |

## 証拠等級（そのまま訳す）

| 中文 | 日本語 |
|---|---|
| 【實測】 | **【実測】** |
| 【文獻】 | **【文献】** |
| 【慣例】 | **【慣例】** |
| 【推論】 | **【推論】** |
| 【待核】 | **【要確認】** |
| 【假設】 | **【仮定】** |

## 表記規則

原文（中文版）は「中国語＋括弧内に英語」。**日本語版は「日本語＋括弧内に英語」**とする。例：耳珠（tragus）、耳甲介腔（cavum conchae）、迷走神経耳介枝（auricular branch of vagus nerve, ABVN）。

数値・引用文献・DOI・出典は**一切変更しない**。
