showmin/ear_3d_model_survey/004/output/v3_AnkerSleepA30/004_v3_soft_silicone_sleeve.stl

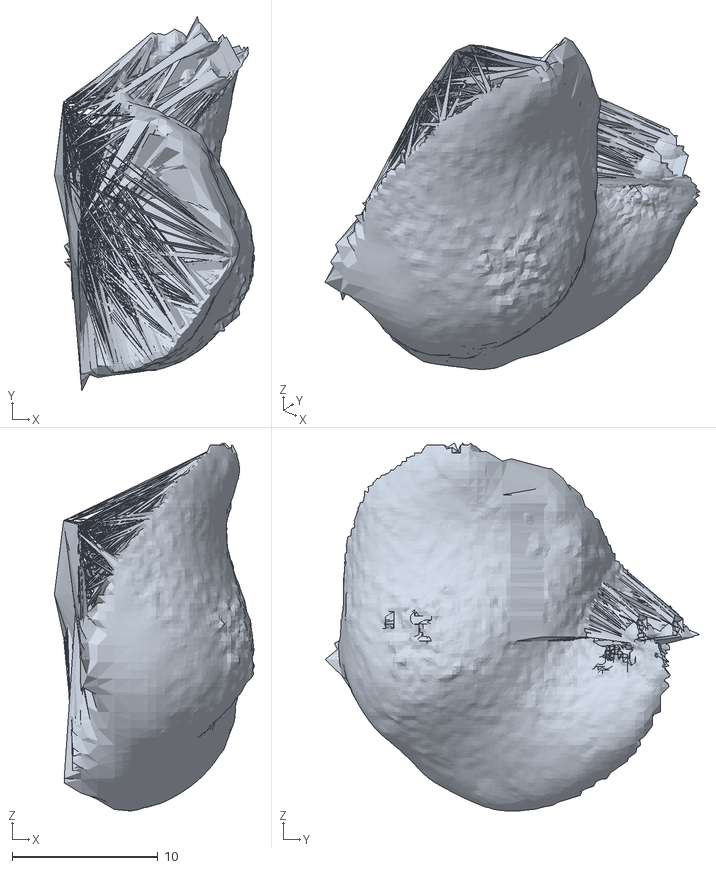
[picture p18: CAD file, 2026-08-28]
004/output/v3_AnkerSleepA30/004_v3_soft_silicone_sleeve.stl
13.7 x 25.7 x 25.2
