showmin/ear_3d_model_survey/004/output/product/airpods_pro_body.stl

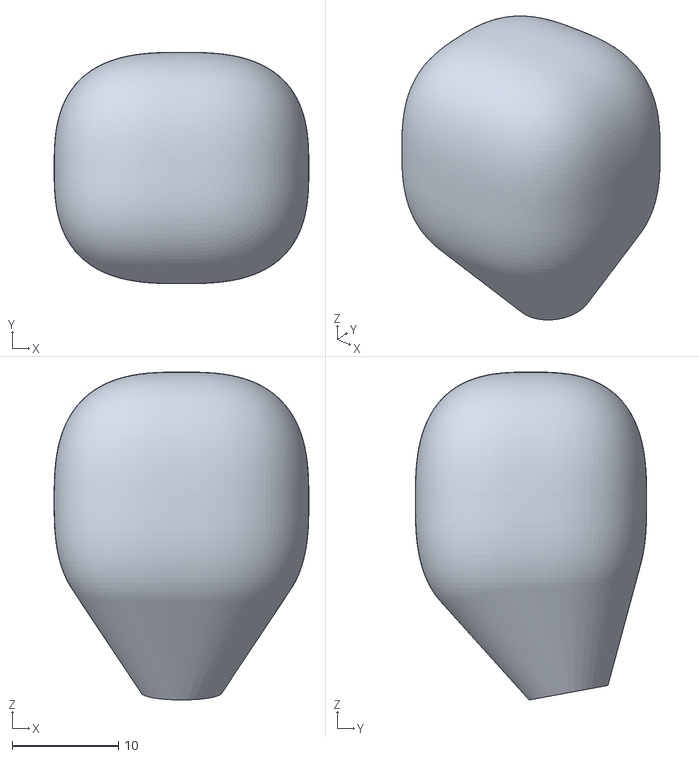
[picture p19: CAD file, 2026-08-28]
004/output/product/airpods_pro_body.stl
24.0 x 21.8 x 30.9
