showmin/ear_3d_model_survey/004/output/product/anker_soundcore_sleep_a30_body.stl

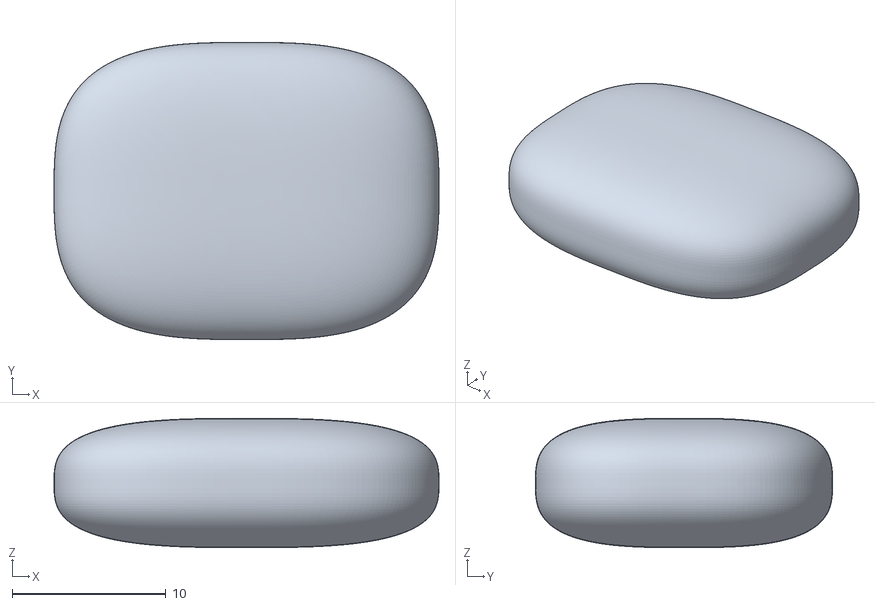
[picture p20: CAD file, 2026-08-28]
004/output/product/anker_soundcore_sleep_a30_body.stl
25.0 x 19.3 x 8.40
