showmin/ear_3d_model_survey/004/output/v1_AirPodsPro/004_v1_soft_silicone_sleeve.stl

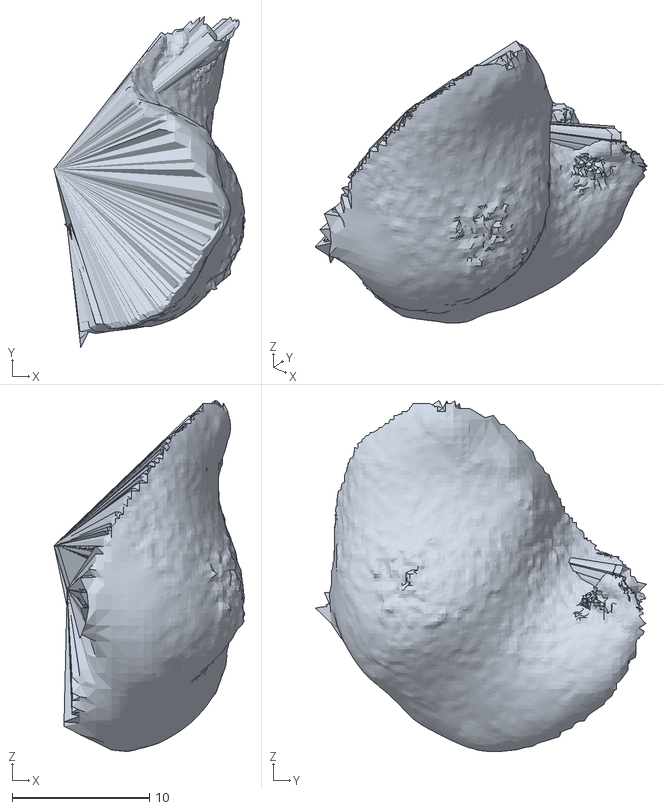
[picture p21: CAD file, 2026-08-28]
004/output/v1_AirPodsPro/004_v1_soft_silicone_sleeve.stl
13.9 x 24.1 x 25.6
