showmin/ear_3d_model_survey/004/output/v2_SonyLinkBudsS/004_v2_soft_silicone_sleeve.stl

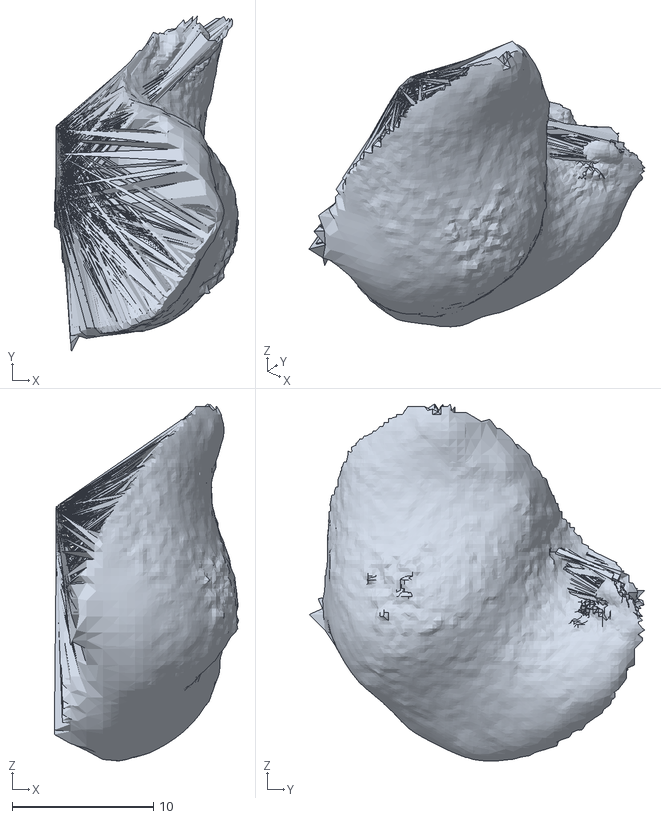
[picture p22: CAD file, 2026-08-28]
004/output/v2_SonyLinkBudsS/004_v2_soft_silicone_sleeve.stl
13.0 x 23.8 x 25.3
