showmin/ear_3d_model_survey/004/output/product/sony_linkbuds_s_in_ear.FCStd

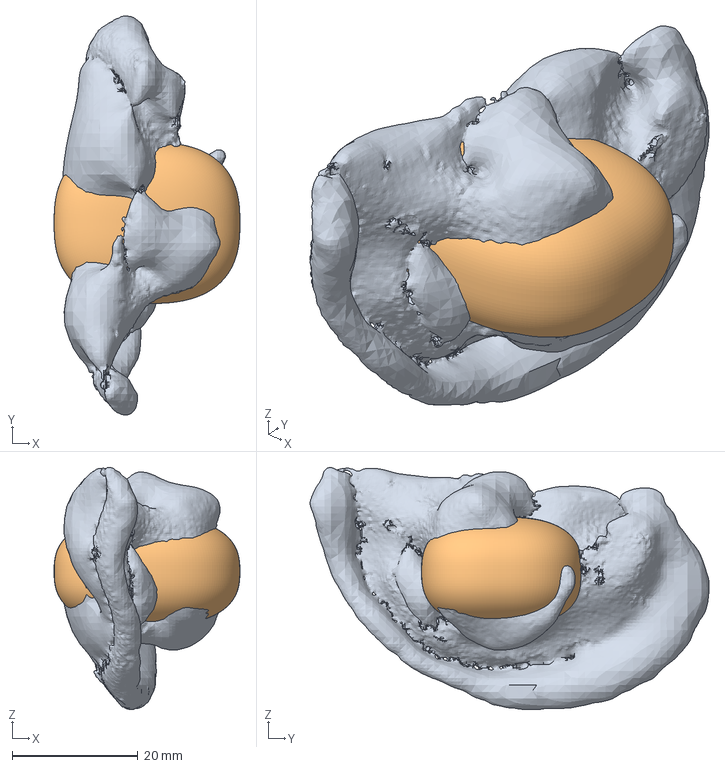
[picture p23: CAD file, 2026-08-28]
004/output/product/sony_linkbuds_s_in_ear.FCStd
29.5 x 63.4 x 38.5 mm
Human_Ear_004
Product_Sony_LinkBuds_S
