showmin/ear_3d_model_survey/004/output/reference_ear/004_concha_basin.stl

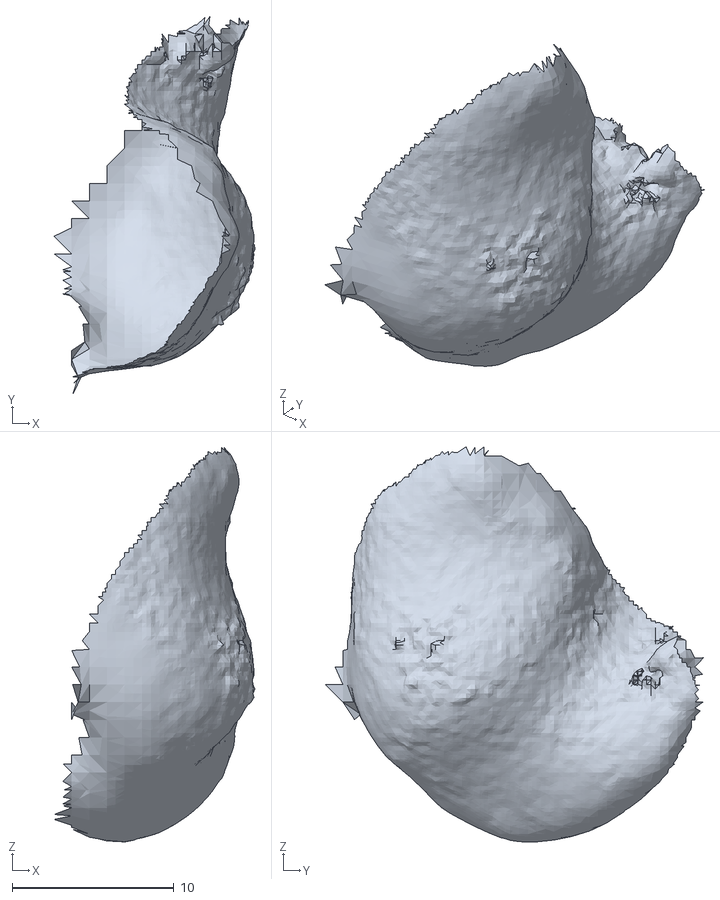
[picture p24: CAD file, 2026-08-28]
004/output/reference_ear/004_concha_basin.stl
12.4 x 23.4 x 24.4
