showmin/ear_3d_model_survey/004/output/product/anker_soundcore_sleep_a30_in_ear.FCStd

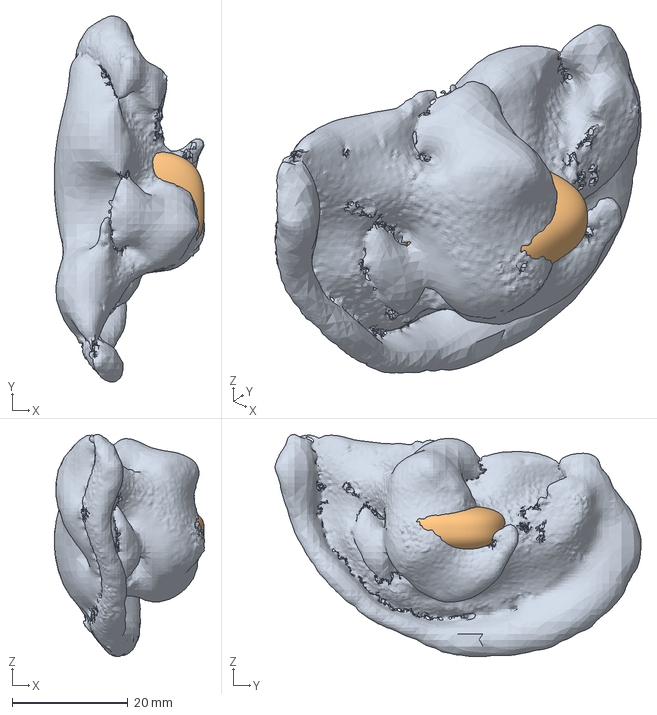
[picture p25: CAD file, 2026-08-28]
004/output/product/anker_soundcore_sleep_a30_in_ear.FCStd
26.0 x 63.4 x 38.5 mm
Human_Ear_004
Product_Anker_Sleep_A30
