showmin/ear_3d_model_survey/004/output/reference_ear/004_canal_entrance.stl

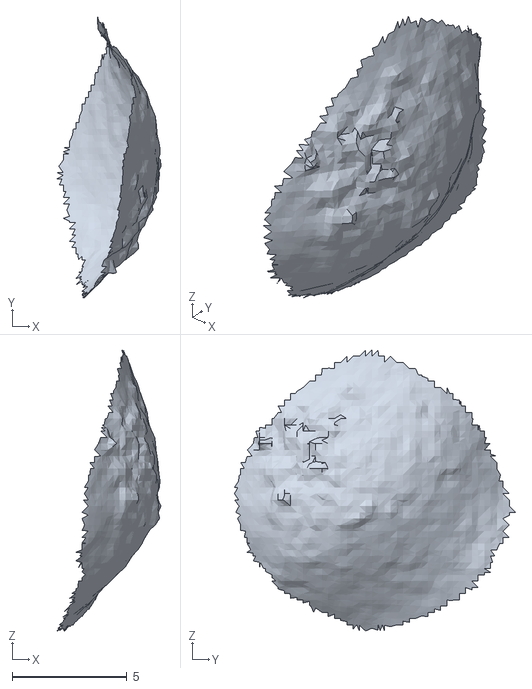
[picture p26: CAD file, 2026-08-28]
004/output/reference_ear/004_canal_entrance.stl
4.53 x 12.2 x 12.2
