showmin/ear_3d_model_survey/004/output/product/anker_soundcore_sleep_a30_airwing.stl

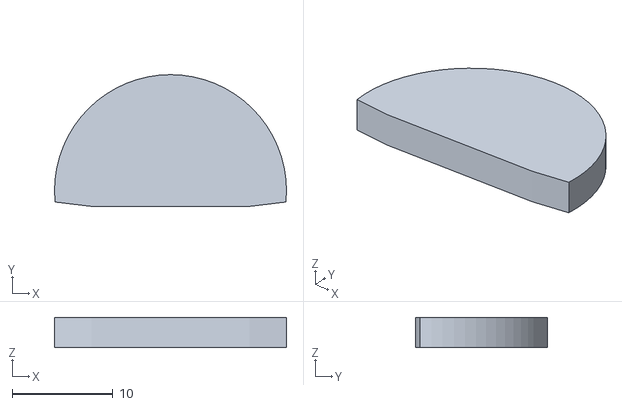
[picture p27: CAD file, 2026-08-28]
004/output/product/anker_soundcore_sleep_a30_airwing.stl
23.0 x 13.1 x 3.00
