showmin/ear_3d_model_survey/004/output/product/sony_linkbuds_s_right.step

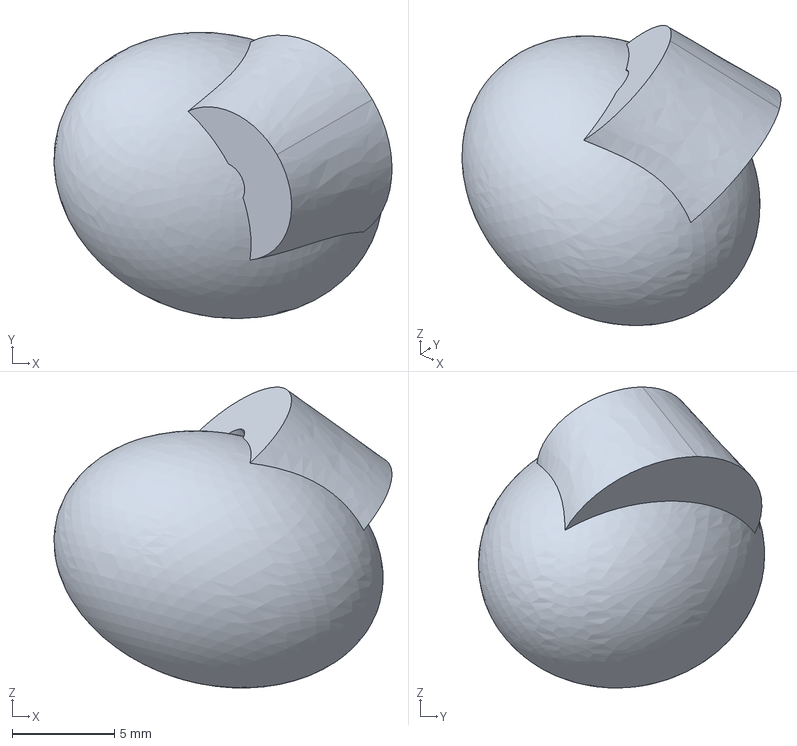
[picture p28: CAD file, 2026-08-28]
004/output/product/sony_linkbuds_s_right.step
16.5 x 14.0 x 14.7 mm
