showmin/ear_3d_model_survey/004/output/product/anker_soundcore_sleep_a30_right.step

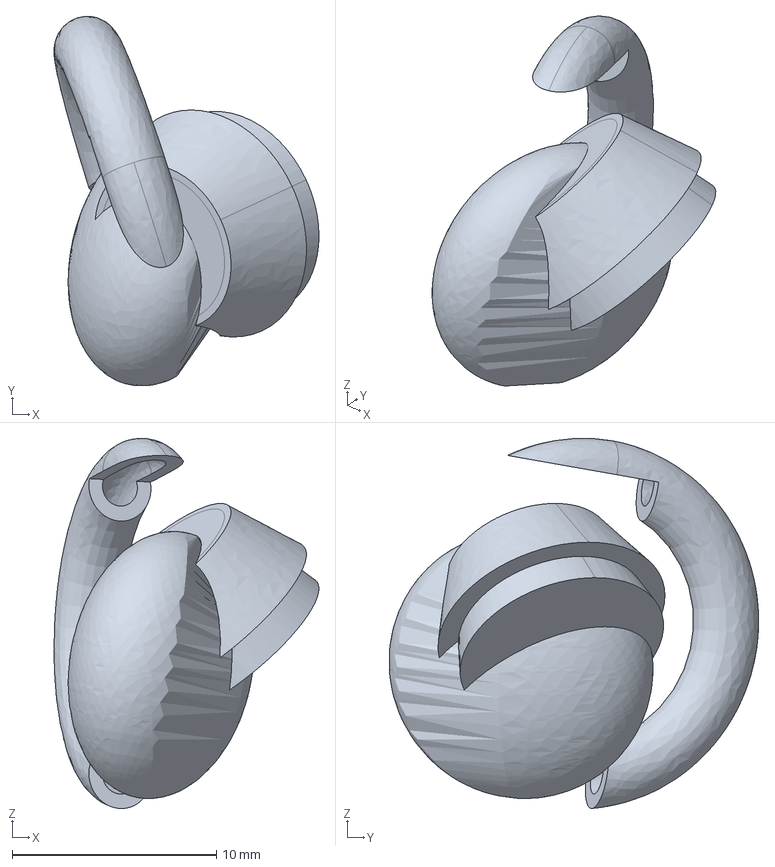
[picture p29: CAD file, 2026-08-28]
004/output/product/anker_soundcore_sleep_a30_right.step
13.0 x 18.1 x 18.1 mm
